jduanen/Acoustic-Camera/RASPBERRY_PI.md

# Running `acoustic_camera_p3.py` on a Raspberry Pi 5

Guide for running the existing Phase 3 live script (`src/acoustic_camera_p3.py`, 16-ch
UMA-16 v2 → 2D beamform → webcam overlay) directly on a Raspberry Pi 5, today, with the
mic array hardware that already exists. This is distinct from the Phase 4 plan
([PHASE4.md](./PHASE4.md)), which uses a Pi 5 as the compute host for a *future* 96-ch
FPGA-fed array. The steps below get the current 16-ch pipeline running standalone in
the meantime, and most of the setup (OS packages, PortAudio, OpenBLAS) carries over
directly to that later phase.

Assumes Raspberry Pi OS, 64-bit, Pi 5 (4 or 8 GB). Written against Debian Bookworm and
confirmed hands-on on Trixie as well. Package names, PortAudio, and the CSI-camera/
`picamera2` situation are the same on both. One real difference found on Trixie: OpenBLAS
is **not** installed by default (see §2). Do that check/install regardless of which OS
version you're on.

**Desktop vs. Lite**: §5 (Display) assumes the Desktop image, which auto-starts a GUI
session (X11 or Wayland). On **Raspberry Pi OS Lite**, there is no display server
running at all -- see the Lite-specific fix in §5.

## 1. System Packages

```bash
sudo apt update
sudo apt install -y libportaudio2 portaudio19-dev python3-opencv v4l-utils
```

- `libportaudio2` / `portaudio19-dev`: `sounddevice` is a thin wrapper over PortAudio;
  without the shared lib it fails to import.
- `python3-opencv`: Raspberry Pi OS's apt build of OpenCV includes GTK GUI support, so
  `cv2.imshow` works out of the box. **Prefer this over `pip install opencv-python`**:
  the PyPI wheel is frequently built headless on ARM and silently breaks `cv2.imshow`
  with a "not implemented" backend error at runtime, not at import time.
- `v4l-utils`: gives you `v4l2-ctl --list-devices` to confirm a USB webcam enumerates
  before wiring it into the script.

## 2. Python Environment

Reuse the project's existing `requirements.txt`. No Pi-specific fork needed, but skip
the packages the live script doesn't import (`acoular`, `pyroomacoustics`, `acoupipe`
are Phase 1 simulation-only):

```bash
python3 -m venv --system-site-packages venv
source venv/bin/activate
pip install numpy scipy sounddevice
```

`--system-site-packages` matters here: it lets the venv see the apt-installed
`cv2` (with GUI support) instead of pulling in a headless wheel from PyPI.

**Confirmed on Raspberry Pi OS Trixie: OpenBLAS is not installed by default.** A stock
Trixie image only has `libblas3`/`liblapack3` (Netlib reference implementations; no
NEON vectorization, single-threaded). `numpy.show_config()` on an unmodified Trixie
install shows generic `name: blas` / `name: lapack` with `openblas configuration:
unknown`, which is the tell that it's riding on the reference implementation rather
than OpenBLAS. This makes MVDR/MUSIC (`scipy.linalg.inv`, `numpy.linalg.eigh`) far
slower than the estimates in §6, so install it explicitly:

```bash
sudo apt install libopenblas0-pthread
```

Debian's `update-alternatives` gives the OpenBLAS build a higher priority (100) than
the reference implementation (10), so this switches automatically. Confirm this with:

```bash
update-alternatives --display libblas.so.3-aarch64-linux-gnu
update-alternatives --display liblapack.so.3-aarch64-linux-gnu
```

Both should report "link currently points to" a path containing `openblas-pthread`.
If not, force it with `sudo update-alternatives --config libblas.so.3-aarch64-linux-gnu`
(and the `liblapack` equivalent) and pick the OpenBLAS entry.

Then confirm from Python:

```bash
python3 -c "import numpy; numpy.show_config()"
```

Note that even with OpenBLAS correctly selected via `update-alternatives`,
`numpy.show_config()` may still print the generic `blas`/`lapack` name with
`openblas configuration: unknown` rather than an explicit `openblas` entry. NumPy's
build-time pkgconfig detection doesn't see through Debian's alternatives indirection.
The `update-alternatives --display` output above is the reliable way to confirm which
implementation is actually linked, not `show_config()`'s `name` field.

This was not something the Bookworm-era assumption in this guide accounted for
(Bookworm's `python3-numpy` was believed to pull in OpenBLAS directly). Treat "is
OpenBLAS actually selected" as a required check on any fresh Pi OS install, not a
formality.

## 3. UMA-16 v2 Hookup

This is dentical to the desktop case -- the UMA-16 is a driverless UAC2 USB device, no Pi-specific
driver needed. Verify it enumerates the same way as in
[nb16](./notebooks/16_uma16_capture.ipynb):

```bash
lsusb | grep -i minidsp        # miniDSP UMA16v2
arecord -l                     # card N: UMA16v2, device 0
python3 -c "import sounddevice as sd; print([d for d in sd.query_devices() if 'uma' in d['name'].lower()])"
```

`find_device()` in `acoustic_camera_p3.py` matches on `'uma' in name`, same as the
notebooks, so no `--device` override should be needed. USB bandwidth for 16 channels ×
24-bit × 48 kHz is trivial for any Pi 5 USB port (no hub/bandwidth concerns).

## 4. Camera

### USB Webcam

The script uses `cv2.VideoCapture(args.video)` (i.e. a V4L2 device index), this only
works with a **USB webcam**, not the Pi Camera Module (CSI). Bookworm removed the
legacy camera stack; the CSI camera is exposed through `libcamera`/`picamera2`, which
`cv2.VideoCapture` cannot open directly. If you only have a Camera Module on hand:

- Easiest: plug in a USB webcam instead; zero code changes.
- Camera Module: use the `--csi` flag — see below. Same direction
  [PHASE4.md](./PHASE4.md#why-pi-5-not-pi-4-or-cm4) already planned for the future 96-ch
  host, implemented here first instead of doing this work twice.

Use `v4l2-ctl --list-devices` to find the right `--video` index. It will very likely
**not** be 0 on a Pi with both a USB webcam and other V4L2-capable hardware present.

### MIPI-CSI Camera

Install 22-pin ribbon cable on one of the connectors near RJ45 connector (contacts facing towards the RJ45).
Earlier Raspberry Pis used 15-pin ribbon cables, can use adaptors to make some of these cameras work with Raspberry Pi 5 boards.
Use camera with M12 lens mount so I can select a lens with the desired FOV.

**Lens choice: 100° FOV.** Two reasons this beats both narrower and wider options on hand
(80/100/120/140/160/200°):

- **Matches the beamforming display window.** The overlay/crosshair math
  (`px = (az_peak + az_fov/2) / az_fov * w`) is a *linear* angle-to-pixel mapping, so the
  camera's real FOV needs to match `--az_fov`/`--el_fov` for the overlay to land on the
  correct pixel. **Confirmed**: switched to this lens, and the code defaults are now
  `az_fov=100°` (matches the lens spec directly) and `el_fov=42°` (scaled from `az_fov`
  by the frame's pixel aspect ratio, `542/1280`, rather than assuming a vertical-FOV
  spec — consistent with the code's own linear-degrees-per-pixel convention, but still
  an approximation pending an empirical check: point the camera at two reference points
  a known angle apart and confirm the crosshair lands where expected).
- **Avoids fisheye distortion.** Lenses above ~100-120° horizontal FOV are essentially
  always fisheye/equidistant-projection, not rectilinear — the linear pixel mapping above
  would be systematically wrong (worse toward the frame edges) without adding a lens
  calibration + `cv2.remap()` undistortion step, which isn't implemented. 100° is the
  widest of the available lenses still likely to be genuinely rectilinear; 80° would be
  the more conservative/certain choice at the cost of a narrower view.

If the wider lenses (120°+) end up preferred later for scene coverage, undistortion is
cheap to add if needed: a one-time `cv2.fisheye.initUndistortRectifyMap()` at startup,
then `cv2.remap()` per frame (~5-8ms at 1280x720 on this hardware, extrapolating from
the comparable-cost `cv2.resize` step already measured in §7 — fits easily in the ~19 ms
of slack under the 50 ms/20 fps budget). The lens calibration itself (checkerboard
capture + `cv2.fisheye.calibrate`) is a one-time setup cost, not a runtime one.

Sensor resolution: no reason to exceed the Touch Display 2's own **1280x720** — the
pipeline never uses more pixels than it displays (no zoom/pan on the video), and §7
already shows overlay-render/`cv2.imshow` cost scaling with pixel count. Target the
sensor's 720p output mode rather than its highest native resolution.

**Software**: `cv2.VideoCapture` cannot open a CSI camera directly (see above), so the
script uses `picamera2` as a second, alternate capture path — pass `--csi` to select it
(`--video` is ignored in that case):

```bash
sudo apt install python3-picamera2   # if not already present on the Desktop image
python src/acoustic_camera_p3.py --algo ds --grid_deg 1.0 --csi
```

`picamera2` is an apt package tied to the system `libcamera` stack, not pip-installable
in an isolated venv — same reasoning as `python3-opencv` in §2: the venv needs
`--system-site-packages` to see it.

Implementation note: `picamera2`'s `"RGB888"` format is actually packed as BGR in
memory (a known naming quirk in `libcamera`), which happens to be exactly the byte
order `cv2` expects — so the capture wrapper (`Picam2Capture` in
`acoustic_camera_p3.py`) does **not** call `cv2.cvtColor` on it. **Confirmed correct on
hardware** — colors display correctly with no conversion. If colors ever look swapped
(red/blue reversed) on a different `picamera2` version, that conversion is the first
thing to add back.

**Confirmed on hardware — this was worth doing**: `cam=0.6 ms`, vs. the USB webcam's
40.7 ms (§7). Total per-frame work drops to ~30.8 ms, under the 50 ms budget, so the
adaptive pacing fix (§7) sleeps out the remainder and this hits the full **~20 fps**
target — a large improvement over the USB webcam's ~14 fps. See §7 for the full
before/after comparison.

Default capture size is `1280x542`, not the panel's native `1280x720` — the missing
`178px` (`2*44 + 90`) is reserved for the Fhi slider strip, spectrum plot, and Flo
slider strip stacked below the video (see README.md's Phase 3 "Touch UI" writeup for
why they're laid out that way), so the combined display still exactly fills the
1280x720 panel with no letterboxing.

## 5. Display

`cv2.imshow` needs a real GUI session. The options below assume the **Desktop** image,
which auto-starts a local GUI session (X11, confirmed by what worked below) on the
HDMI-attached monitor at boot.

**Important distinction confirmed on hardware**: "a desktop session is running on the
Pi" is not the same as "your shell can draw to it." A plain SSH login is a separate
session (`XDG_SESSION_TYPE=tty`, no `DISPLAY`/`XAUTHORITY` set) from the auto-started
local desktop session on `seat0`, even though both exist on the same machine at the
same time (check with `loginctl list-sessions`). Three distinct scenarios:

- **Logged in locally** (keyboard/monitor directly on the Pi, or VNC into that same
  session): just works, `DISPLAY` is already set correctly in that session's own
  terminal.
- **SSH with `-X`/`-Y` forwarding**: works, but *not* by drawing on the Pi's monitor:
  it creates a **new**, separate X11 display on the Pi that tunnels every frame back
  over the network to your own machine's X server. The window appears on your laptop,
  not the Pi's HDMI output. Also far too slow for live 15-20 fps video, it is useful only
  for a one-off sanity check.
- **SSH, no `-Y`, attaching to the Pi's own already-running local desktop session**:
  this is what actually renders on the Pi's physical HDMI monitor while running the
  command remotely. **Confirmed working recipe:**

  ```bash
  export DISPLAY=:0
  export XAUTHORITY=/home/pi/.Xauthority   # your actual home dir
  python acoustic_camera_p3.py --video 0 --grid_deg 1.0
  ```

  Both variables are required. `DISPLAY=:0` alone fails with "could not connect to
  display" (Qt still needs the auth cookie to attach to someone else's X session).
  This is a plain X11 session using the standard per-user `~/.Xauthority`, which is simpler
  than initially expected; no Xwayland-specific rootless auth file hunting needed.

Add `--fullscreen` to fill the whole monitor (borderless window) -- see §6.

### Raspberry Pi OS Lite (partial, not fully validated)

Lite has no display server running at all -- no X11, no Wayland compositor. `cv2.imshow`
fails with:

```
qt.qpa.xcb: could not connect to display
qt.qpa.plugin: Could not load the Qt platform plugin "xcb" ...
```

This looks like a GTK-vs-Qt OpenCV backend problem (the plugin list even offers
`wayland`), but it isn't; there is simply no compositor for any backend to attach to.
The lightest fix, in principle, is a bare X server with no window manager, using
`xinit` to launch the script as the sole X client:

```bash
sudo apt install --no-install-recommends xserver-xorg xinit x11-xserver-utils
xinit /path/to/venv/bin/python /path/to/acoustic_camera_p3.py --video 0 --grid_deg 1.0 -- :0
```

**This was not fully validated**: on real hardware this problem occurred `Fatal server error:
Cannot run in framebuffer mode. Please specify busIDs for all framebuffer devices`.
Xorg is falling back to the `fbdev` driver instead of `modesetting`/KMS (the Pi 5 has no
non-KMS mode). The likely fix is forcing the driver explicitly:

```bash
sudo mkdir -p /etc/X11/xorg.conf.d
sudo tee /etc/X11/xorg.conf.d/10-modesetting.conf <<'EOF'
Section "Device"
    Identifier "Pi5"
    Driver "modesetting"
    Option "kmsdev" "/dev/dri/card0"
EndSection
EOF
```

(`modesetting` is built into `xserver-xorg-core`, not a separate package; no install
needed for the driver itself.) This was not re-tested. The Pi was reinstalled with
the Desktop image instead, which avoids the whole class of problem. If you need a
Lite-based headless deployment later (e.g. a lighter Phase 4 field unit), start here
but expect to need this driver fix, and confirm `/dev/dri/card0` is actually the right
device (`ls /dev/dri/`) before assuming it.

### DSI Display

Tested first using HDMI-attached display. Now using the Raspberry Pi Touch Display 2
(https://www.raspberrypi.com/documentation/accessories/touch-display-2.html#raspberry-pi-touch-display-2),
connected via the DSI port. Touch works out of the box as mouse input for the script's
frequency sliders — no config needed there.

The panel's native orientation is portrait; rotate it to landscape at login. Raspberry
Pi OS Desktop on Trixie runs **Wayland (`labwc`)**, with `:0` served via XWayland for X11
compatibility — so this must be done with `wlr-randr` (the Wayland-native output tool),
**not** `xrandr`: `xrandr` talks to XWayland's emulated root window, which can't be
resized/rotated and fails with a RandR `BadMatch` error for this. `wlr-randr` talks to
the compositor directly and works.

First confirm your actual output name (`wlr-randr` with no arguments lists all outputs —
this DSI port enumerated as `DSI-2`, not `DSI-1`, on this hardware; don't assume it
matches without checking), then add the rotation to `labwc`'s autostart script so it
applies on every login, not just the current session:

```bash
wlr-randr                      # confirm the output name first
mkdir -p ~/.config/labwc
echo 'wlr-randr --output DSI-2 --transform 270 &' >> ~/.config/labwc/autostart
chmod +x ~/.config/labwc/autostart
```

`--transform` takes `90`/`180`/`270` (or `flipped-90` etc. for mirrored orientations) —
adjust if the picture comes up rotated the wrong way. Reboot (or log out/in) to confirm
it persists; a manually-run `wlr-randr` command only affects the current session.

#### Touchscreen

Edit `/etc/xdg/libfm/libfm.conf` and change `single_click=0` to `single_click=1`.

### Auto-start on boot

A system-level systemd unit ([systemd/acoustic-camera.service](./systemd/acoustic-camera.service))
launches the script automatically once the Desktop image's auto-login GUI session comes
up, using the same `DISPLAY=:0` / `XAUTHORITY` recipe confirmed above. It's a system
unit rather than a `~/.config/systemd/user/` one so it doesn't depend on whether
labwc's autologin session actually signals `graphical-session.target` for the user's
systemd instance — instead it targets `graphical.target` (reached once any display
manager/session starts) and leans on `Restart=on-failure` + `RestartSec=5` (with the
`[Unit]` start-limit disabled) to self-heal through the boot race if it launches before
the desktop session has actually finished coming up, rather than a bespoke wait-for-X
script. Pressing `q` to quit exits 0, so it won't auto-relaunch after a deliberate quit.

Install:

```bash
sudo cp systemd/acoustic-camera.service /etc/systemd/system/
sudo systemctl daemon-reload
sudo systemctl enable --now acoustic-camera.service
```

The unit hardcodes user `jdn` and path `/home/jdn/Code/Acoustic-Camera` — edit
`User=`, `WorkingDirectory=`, `XAUTHORITY=`, and `ExecStart=` if deploying under a
different account or checkout path. Check status/logs with
`systemctl status acoustic-camera.service` / `journalctl -u acoustic-camera.service -f`.

### Home Screen Icons for System Control

Once the `Exit` button is pushed on the Acoustic Camera application's popup window, the application will exit and the Raspberry Pi Trixie desktop will be shown.
In addition to the standard desktop taskbar, there are several icons on the Desktop that can be used to quickly control the application and system.

#### Acoustic Camera



Touching this icon starts the Acoustic Camera application (which takes over the full screen).

The Acoustic Camera icon's action is defined in `./Desktop/acousticcamera.desktop`.

#### Reboot

Reboot Icon

Touching this icon causes the Raspberry Pi to reboot and relaunch the Acoustic Camera application.

The system reboot icon's action is defined in `./Desktop/reboot.desktop`.

#### System Shutdown

Shutdown Icon

Touching this icon will cause the system to shutdown.

The system shutdown icon's action is defined in `./Desktop/shutdown.desktop`.

#### Battery

Battery Icon

Shows the current UPS charge as a percentage, baked into the icon graphic itself (green ≥50%, amber ≥20%, red below). The icon is regenerated from the INA219 fuel-gauge chip (same reading as the live overlay's own battery indicator, see `src/acoustic_camera_p3.py`) by `bin/battery_icon.py`, which writes `assets/battery_icon.png`. Touching the icon re-runs that script for an immediate refresh; otherwise it's kept current automatically by `battery-icon.timer` (every 60s).

The battery icon's action is defined in `./Desktop/battery.desktop`. Install the timer:

```bash
sudo cp etc/systemd/system/battery-icon.service etc/systemd/system/battery-icon.timer /etc/systemd/system/
sudo systemctl daemon-reload
sudo systemctl enable --now battery-icon.timer
```

Note: whether the desktop actually redraws an already-displayed icon when its target PNG changes on disk depends on the desktop shell's icon-cache behavior — `bin/battery_icon.py` also touches `Desktop/battery.desktop`'s mtime after each render as a best-effort nudge, but this hasn't been fully validated against Trixie's desktop (pcmanfm/labwc). If it doesn't auto-refresh in practice, tapping the icon (or `F5`) forces a redraw.

#### Calibrate

Calibrate Icon

Runs `src/calibrate_uma16.py`, a terminal walkthrough of the same boresight-reference procedure as [`notebooks/17_uma16_calibration.ipynb`](notebooks/17_uma16_calibration.ipynb) (frequency-domain cross-correlation for per-mic delay, RMS ratios for per-mic gain), so the array can be re-calibrated directly on the appliance without a dev machine or Jupyter. It records a 5s boresight clip on prompt, prints the measured delay/gain per channel, backs up any existing `test/UMA16/cal.npy` to `cal.npy.bak`, saves the new calibration vector, and reports the boresight DoA peak (D&S and MVDR) before vs after as a sanity check.

Touching the icon opens `lxterminal` running `bin/calibrate.sh`, so the prompts and results are visible; the window stays open until you press Enter at the final prompt. The calibrate icon's action is defined in `./Desktop/calibrate.desktop` — it assumes `lxterminal` is the installed terminal emulator (Raspberry Pi OS's default); swap the `Exec=` command if a different one is in use.

**Tone frequency**: the script prompts for a **1 kHz** tone (`CAL_FREQ` in `src/calibrate_uma16.py`), matching both source notebooks. 1 kHz is:
- well below the array's ~4082 Hz spatial Nyquist (`NYQUIST` in `src/beamforming.py`, set by the 42mm mic spacing), so there's no spatial-aliasing ambiguity in the phase measurement;
- easily reproduced cleanly by a phone or laptop speaker (most roll off below 1 kHz or beam/distort above it);
- short enough a wavelength (~343mm) relative to typical mic-to-mic delays that the delay-to-phase conversion (`2π·f·delay`) stays well within ±π, avoiding phase-wrap ambiguity.

Any phone tone-generator app works, or from a laptop with `sox` installed:
```bash
play -n synth 5 sine 1000
```

**Device selection**: like `acoustic_camera_p3.py`, the script auto-detects the UMA-16 via
`find_device()` (first device whose name contains "uma" with ≥16 input channels), or you can
pin it explicitly with `--device IDX`. Do this if the main app needs `--device` to find the
right entry too (some ALSA setups enumerate the same physical device more than once, e.g. a
raw `hw:X` PCM alongside a `plughw`/`dsnoop`-wrapped one). Run
`python -c "import sounddevice as sd; print(sd.query_devices())"` to see all candidates and
their indices.

**Recording method**: the script captures via `sd.InputStream(..., blocksize=256, callback=...)`
— the exact same method `acoustic_camera_p3.py` uses — rather than the simpler
`sd.rec()`/`sd.wait()` convenience call, which lets PortAudio pick its own default
blocksize/latency. This wasn't confirmed to be the actual cause of any specific failure, but
matching the main app's proven-working capture method removes one source of behavioral
difference between the two scripts.

**Validity check is SNR-based, not amplitude-based**: `calibrate_uma16.py` checks that
`CAL_FREQ` is at least `_MIN_SNR_DB` (20 dB) above the noise floor, not that the recording
is loud in absolute terms. This matters because a real, usable tone can be very quiet in
absolute amplitude — well under 1% of full scale — if the source is distant or this
particular UMA-16 unit's capture chain runs at low gain, while still being extremely clean
relative to the noise floor (a real observed case: ~46 dB SNR at ~0.1% of full scale). An
earlier version of this check used absolute peak amplitude instead and incorrectly rejected
recordings like that one. If you ever want to check a recording's SNR by hand:
```bash
python3 -c "
import numpy as np, scipy.io.wavfile as wavfile
fs, ref = wavfile.read('test/UMA16/cal_ref.wav')
seg = ref[:8192, 0].astype(np.float32) * np.hanning(8192)
F = np.abs(np.fft.rfft(seg))**2
freqs = np.fft.rfftfreq(8192, 1/fs)
pk = np.argmin(np.abs(freqs - 1000))
print('SNR (dB):', 10*np.log10(F[pk-3:pk+4].mean() / np.median(F)))
"
```

**If the tone isn't actually audible to the array** — too quiet, too far, not playing, or
the wrong input device — the reference recording is just mic/ADC self-noise, and the
resulting delay/gain estimates are meaningless (typically visible as several channels
locking onto suspiciously identical exact-integer-sample delays, since noise has no real
cross-channel phase relationship). `calibrate_uma16.py` checks for this: if the loudest
sample in the recording is below 2% of full scale, it aborts with an explanation instead of
saving a bogus calibration — the existing `cal.npy` is left untouched. Watch the per-channel
RMS bar chart the script prints right after recording; a real tone shows clearly elevated
bars, not near-empty ones.

## 6. Performance Expectations

The Pi 5's Cortex-A76 @ 2.4 GHz with OpenBLAS runs dense BLAS roughly 3-4× slower than a
modern desktop CPU (measured basis for this estimate: [PHASE4.md](./PHASE4.md) scaling
analysis for the 96-ch Phase 4 host). Scaling the existing 16-ch desktop benchmarks from
[PHASE3.md](./PHASE3.md)'s `benchmark_algos.py` results:

| Grid | D&S (desktop measured) | D&S (Pi 5, est.) | MVDR/MUSIC (Pi 5, est.) | CLEAN-SC 20 iter (Pi 5, est.) |
|---|---|---|---|---|
| 0.5°/pt (181×121 = 21,901 pts) | ~21 ms | ~70-85 ms | ~75-90 ms | ~300-350 ms |
| 1.0°/pt (91×61 = 5,551 pts) | ~7 ms  | ~20-25 ms | ~20-25 ms | ~55-65 ms |

At 1.0°/pt, D&S/MVDR/MUSIC should sustain roughly 15-20 fps on the Pi 5 *purely on compute
cost*. At the default 0.5°/pt, D&S is likely still fine but MVDR/MUSIC and especially
CLEAN-SC will visibly lag. **These estimates only cover the CSM+beamform math** — see §7
for what the live script actually costs end-to-end, which is substantially more than this
table alone would suggest.

**Recommended starting command**: coarser grid, cheapest algorithm, confirm it runs
before turning up resolution or trying MVDR/MUSIC/CLEAN-SC:

```bash
python src/acoustic_camera_p3.py --algo ds --grid_deg 1.0
```

For a fixed HDMI-monitor "camera appliance" deployment, add `--fullscreen` to fill the
whole screen with a borderless window (see §5 for how to get the display attached in
the first place):

```bash
python src/acoustic_camera_p3.py --algo ds --grid_deg 1.0 --fullscreen
```

If you want real numbers instead of estimates before wiring up the camera/display,
run the existing benchmark script directly on the Pi first. It needs no camera, no
display, and no live mic input (it loads `test/UMA16/capture_nb16.wav`):

```bash
python src/benchmark_algos.py --grid_deg 1.0
```

That gives per-algorithm mean time and RT% on the actual Pi 5 hardware, which is more
trustworthy than the estimates in the table above.

## 7. Performance Measurements

The §6 estimates come from the offline `benchmark_algos.py` script, which only measures
CSM + beamform math. The live script (`acoustic_camera_p3.py`) also does camera capture,
overlay rendering, and `cv2.imshow`, none of which appear in that benchmark — and on real
hardware, those turned out to matter more than the compute estimates did. The script has a
`--profile` flag that prints a per-stage timing breakdown to stderr every 20 frames:

```bash
python src/acoustic_camera_p3.py --algo ds --grid_deg 1.0 --video 0 --profile
```

**Confirmed on hardware** (Pi 5, D&S, 1.0°/pt, real UMA-16):

| Stage | USB webcam (`--video 0`) | No camera (`--video 99`) | MIPI-CSI (`--csi`) |
|---|---|---|---|
| camera capture | 40.7 ms | 0.1 ms | **0.6 ms** |
| audio buffer → array | 6.2 ms | 6.0 ms | 6.5 ms |
| CSM + D&S | 13.1 ms | 12.6 ms | 13.2 ms |
| overlay render | 6.3 ms | 5.7 ms | 6.2 ms |
| `cv2.imshow` + `waitKey` | 4.0 ms | 3.9 ms | 4.3 ms |
| **compute total** | **70.3 ms** | **28.2 ms** | **30.8 ms** |

`--fullscreen` made no measurable difference to any of these — the source frame `cv2.imshow`
receives is the same size either way; only the window-manager-side scale-to-screen changes,
which isn't where the cost is.

- USB webcam: 70.3 ms of work already exceeds the 50 ms budget → sleep contributes ~0 →
  **~14 fps** (up from the original ~8 fps), limited purely by camera capture cost
- No camera: 28.2 ms of work + ~21.8 ms sleep ≈ 50 ms/frame → **~20 fps** (hits the intended target after fixing the loop delay bug)
- MIPI-CSI: 30.8 ms of work + ~19.2 ms sleep ≈ 50 ms/frame → **~20 fps** — matches the
  no-camera ceiling, i.e. the CSI camera is effectively free compared to the beamforming
  compute cost. This is the best available camera configuration on this hardware.

### Camera Backend: default auto-selection was already the best option

`cam.read()`'s ~40 ms floor was tried two ways to reduce, both regressions on this hardware:

| Backend | `cam.read()` |
|---|---|
| Default (`cv2.VideoCapture(idx)`, auto-selects GStreamer) | **40.7 ms** |
| Forced `cv2.CAP_V4L2`, no format hint | 65.2 ms |
| Forced `cv2.CAP_V4L2` + explicit `cv2.VideoWriter_fourcc(*'MJPG')` | 64.0 ms |

Likely explanation: GStreamer's auto-negotiated pipeline was probably already requesting a
compressed (MJPEG) format from the webcam, while raw V4L2 without an explicit format request
defaulted to something uncompressed (e.g. YUYV) — roughly double the bytes over USB plus more
software color-conversion work. **Reverted to the plain default** (`cv2.VideoCapture(args.video)`,
no explicit backend/format) — confirmed the fastest of the three on this specific webcam/Pi
combination. This is device-specific; a different USB webcam could behave differently.

### Confirmed: MIPI-CSI camera via `picamera2` solves the camera bottleneck

Implemented (`--csi` flag, see §4) and confirmed on hardware — numbers above. A
CSI-attached Camera Module bypasses USB and GStreamer entirely, talking to the Pi's
ISP/DMA pipeline directly via `picamera2` rather than `cv2.VideoCapture` (which cannot
open a CSI camera at all). Same direction
[PHASE4.md](./PHASE4.md#camera-pi-camera-module-3-wide) already planned for the 96-ch
host — implemented here first instead of doing the work twice. Colors confirmed correct
with no `cv2.cvtColor` needed (see §4's `RGB888`/BGR note).

## 8. System Hardware

When running the `acoustic_camera_p3.py` program, the system consumes up to around 1.75A @ 5V.
This means that not only do I have to power this with a (ideally battery) source that can provide in excess of 2A at 5.V (actually 5.1V), but I also have to have cabling that can support this current load without imposing a significant resistive loss.

Furthermore, even with a large heatsink with a fan, the CPU temperature gets up to ~60C (with ~25C ambient).

### Power Supply

The system is powered by three 18650 Li batteries in a series configuration and managed by a Waveshare UPS 3S module (see https://www.waveshare.com/ups-module-3s.htm).

The Battery Management System (BMS) provides balanced charging, reverse warning, and battery protection for the Li batteries, as well as voltage and current monitoring, 3.3V and 5V regulation, and an I2C bus interface to the Raspberry Pi.

The Raspberry Pi's I2C interface must first be enabled by running `raspi-config` and selecting `Options -> I2C -> Yes`.

A Waveshare-provided program that prints the current voltage, current, power, and remaining battery percentage is found in https://files.waveshare.com/upload/e/ea/UPS_Module_3S_Code.zip.

`acoustic_camera_p3.py` reads the same INA219 chip directly (via `ups/UPS_Module_3S_V2/INA219.py`, I2C address `0x41`) and draws a battery icon + percentage next to the settings tab in the top-right corner of the live display. It needs apt's `python3-smbus` (see requirements.txt); without it, or without a UPS attached, the indicator is simply not drawn.

N.B. It is important to source the Li batteries from a well-known reliable source as they are very energetic and could cause a problem if they were to malfunction.

## 9. Known Issues Summary

| Symptom | Cause | Fix |
|---|---|---|
| `sounddevice` import error | missing `libportaudio2` | `apt install libportaudio2` |
| `cv2.imshow` errors "not implemented" | headless OpenCV wheel from `pip` | use apt `python3-opencv`, venv with `--system-site-packages` |
| Camera won't open / wrong device | Pi Camera Module (CSI), not a USB webcam | use a USB webcam, or pass `--csi` for `picamera2` (see §4/§7) |
| `cv2.imshow` hangs / X errors over SSH | no display session, or SSH session not attached to the Pi's local desktop session | log in locally/VNC, or export `DISPLAY=:0` + `XAUTHORITY=~/.Xauthority` (see §5) |
| `ssh -Y` window appears on your own machine, not the Pi's monitor | `-Y` tunnels a **new** X display back to your client; it never touches the Pi's HDMI output | use the `DISPLAY`/`XAUTHORITY` attach recipe in §5 instead of `-Y` |
| Low fps at default settings | 0.5°/pt grid + MVDR/MUSIC/CLEAN-SC too heavy for Pi 5 | `--grid_deg 1.0`, start with `--algo ds` |
| Live fps much lower than §6 compute estimates suggest | camera capture (~40 ms) + a frame-pacing bug (fixed sleep added *on top of* work, not a target) both add cost the offline benchmark never measured | see §7; pacing bug is fixed in current code, camera cost is a hardware floor with this webcam |
| MVDR/MUSIC far slower than §6 estimates | OpenBLAS not installed (confirmed default on Trixie); NumPy silently falls back to reference BLAS/LAPACK | `apt install libopenblas0-pthread`, verify with `update-alternatives --display libblas.so.3-aarch64-linux-gnu` |
| Xorg: `Cannot run in framebuffer mode...` (Lite only) | falling back to `fbdev` instead of `modesetting`/KMS | force `modesetting` via `/etc/X11/xorg.conf.d` (see §5, not fully validated) |
| Touch sliders felt laggy / seemed to cross despite clamping | stale read used for display, not the clamp math | see README.md's Phase 3 "Touch UI" section |
| `calibrate_uma16.py` aborts with "X Hz is only Y dB above the noise floor" | genuinely no usable tone in the recording — not just quiet, but no clean peak at `CAL_FREQ` at all | confirm the tone is really playing (not timed out/stopped), check device selection, re-run — see §8 Calibrate |
| RMS bars all look tiny / peak amplitude is well under 1% of full scale | not necessarily a problem — check the printed SNR line instead of judging by eye. A real tone can be very quiet in absolute terms yet still pass easily (observed: ~46 dB SNR at ~0.1% of full scale) | see §8 Calibrate's "Validity check is SNR-based" note; if SNR is also low, then it's a real issue (see row above) |
