jduanen/Acoustic-Camera/assets/arm_board.png

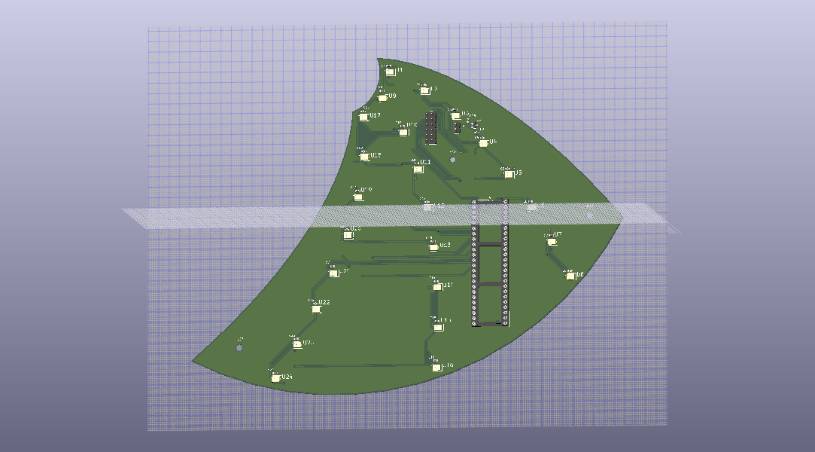
assets/arm_board.png
