jduanen/Acoustic-Camera/assets/hub.png

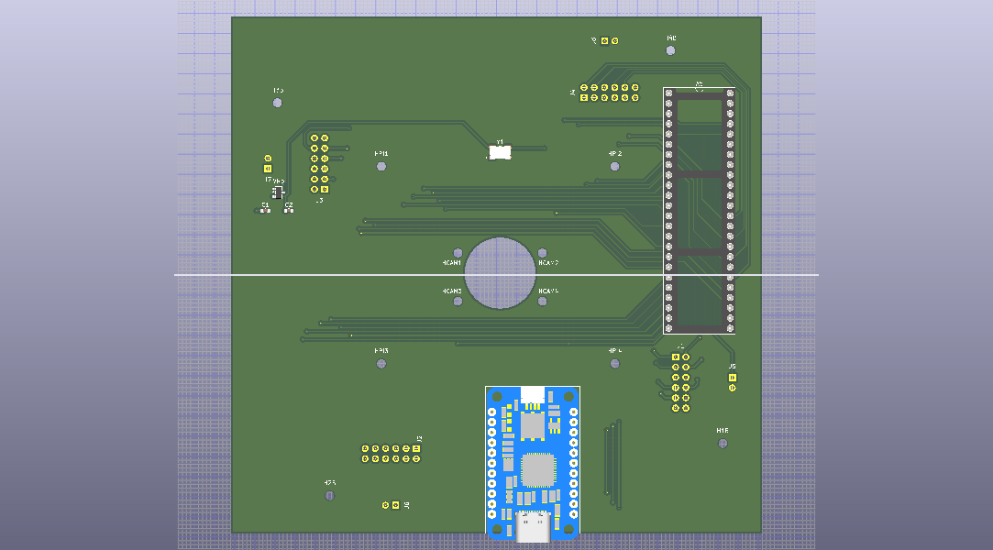
assets/hub.png
