jduanen/Acoustic-Camera/assets/Phase3InsideTop.jpg

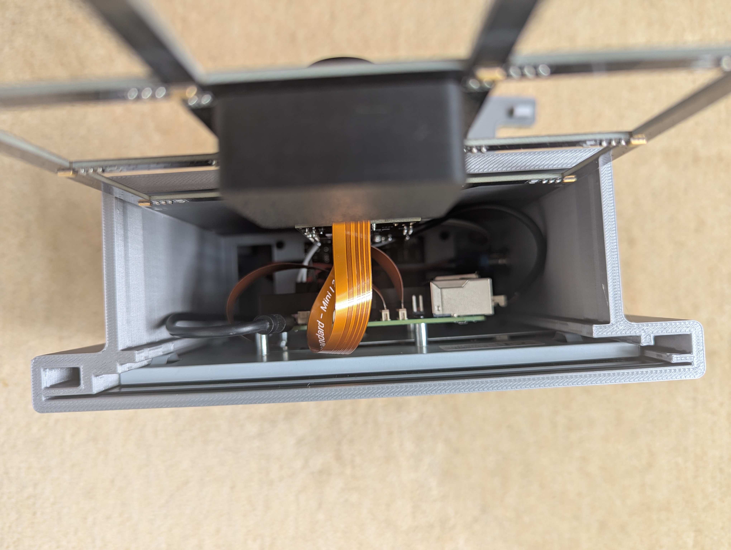
assets/Phase3InsideTop.jpg
