jduanen/Acoustic-Camera/images/phase4_array_configs.png

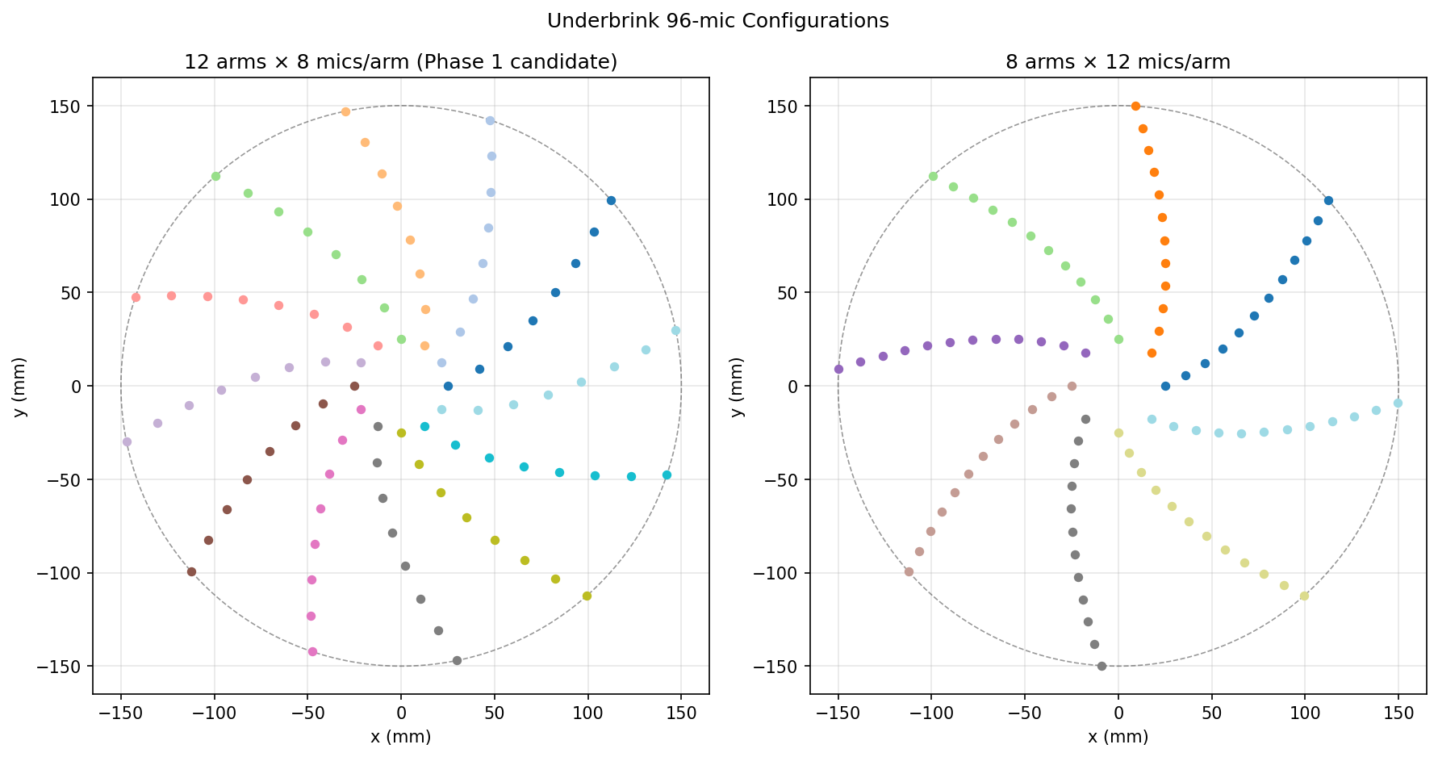
images/phase4_array_configs.png
