jduanen/Acoustic-Camera/images/phase4_array_layout.png

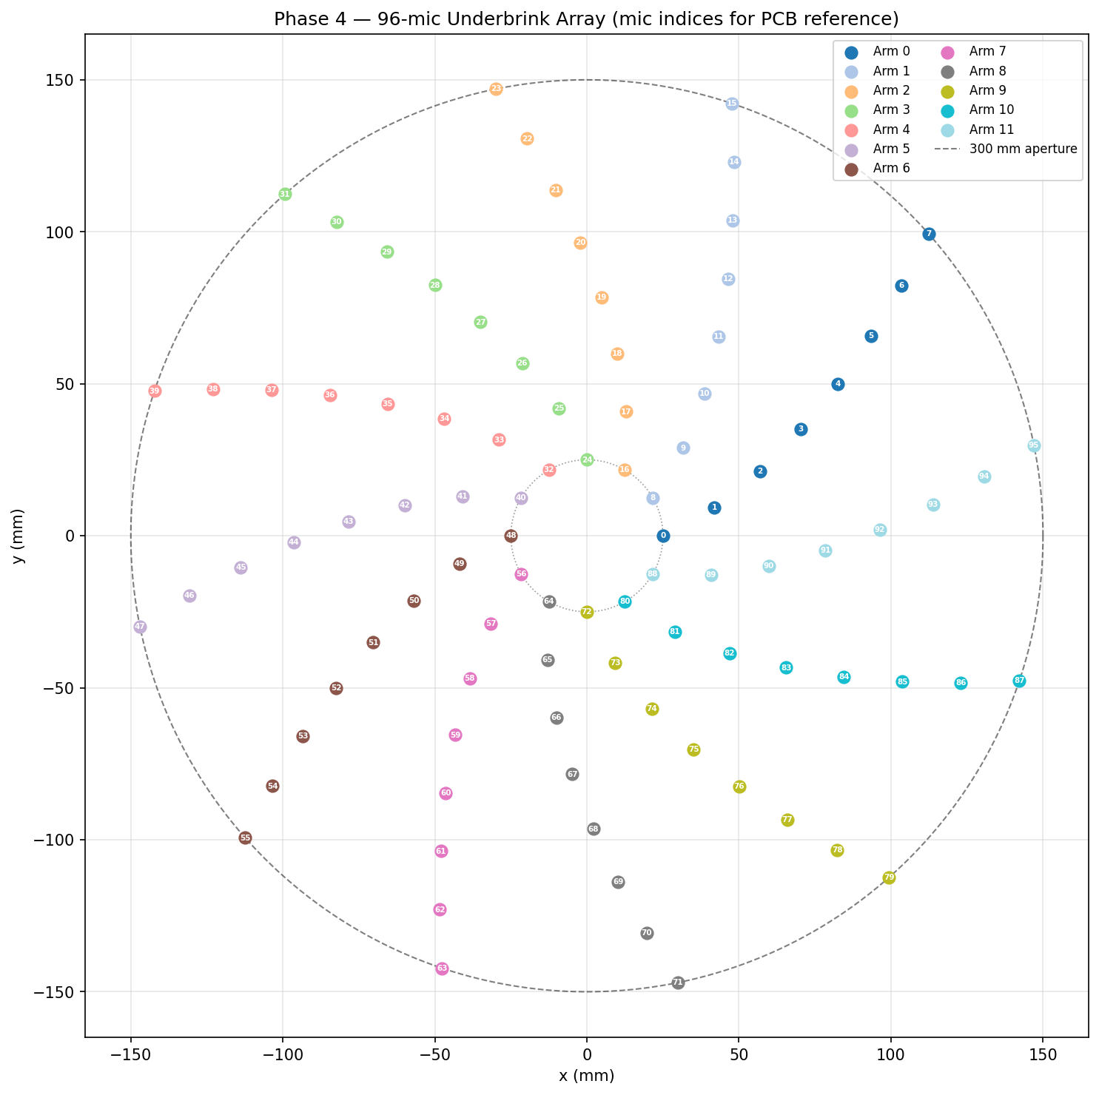
images/phase4_array_layout.png
