jduanen/Acoustic-Camera/images/phase4_hpbw.png

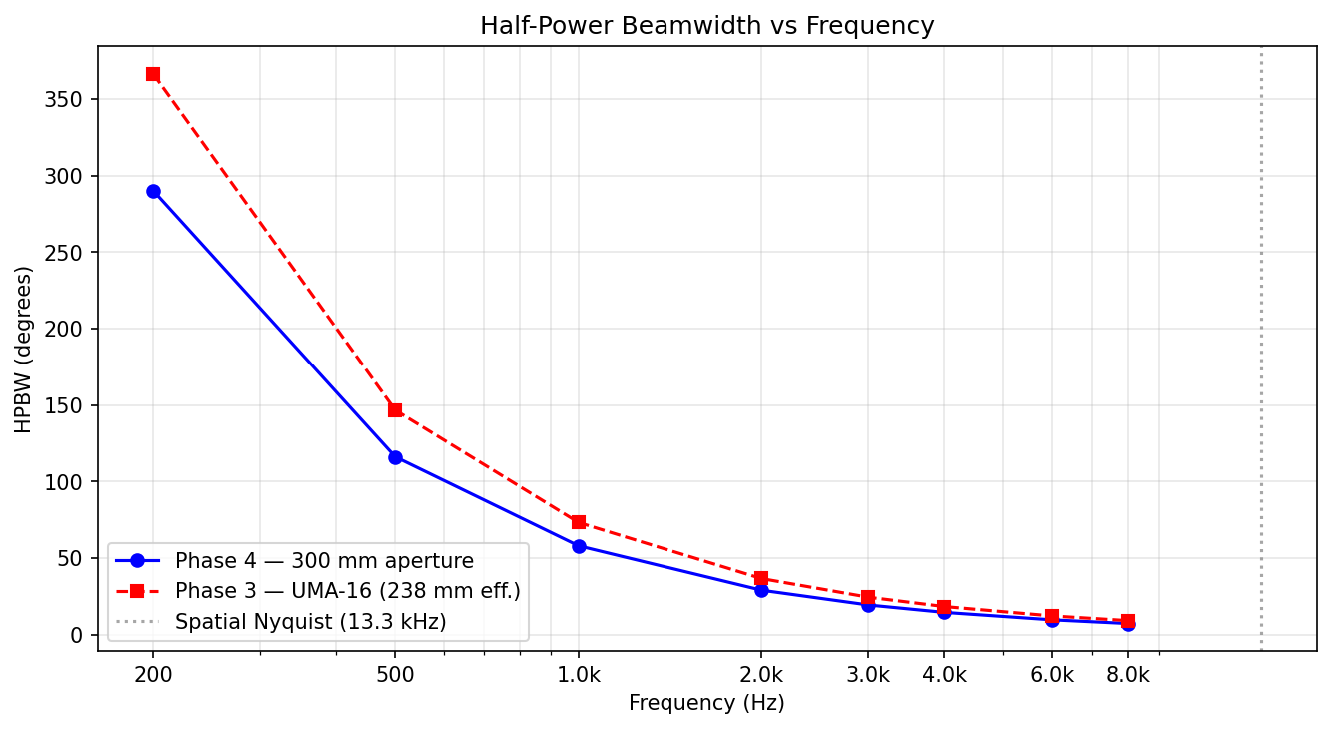
images/phase4_hpbw.png
