jduanen/Acoustic-Camera/images/phase4_nn_hist.png

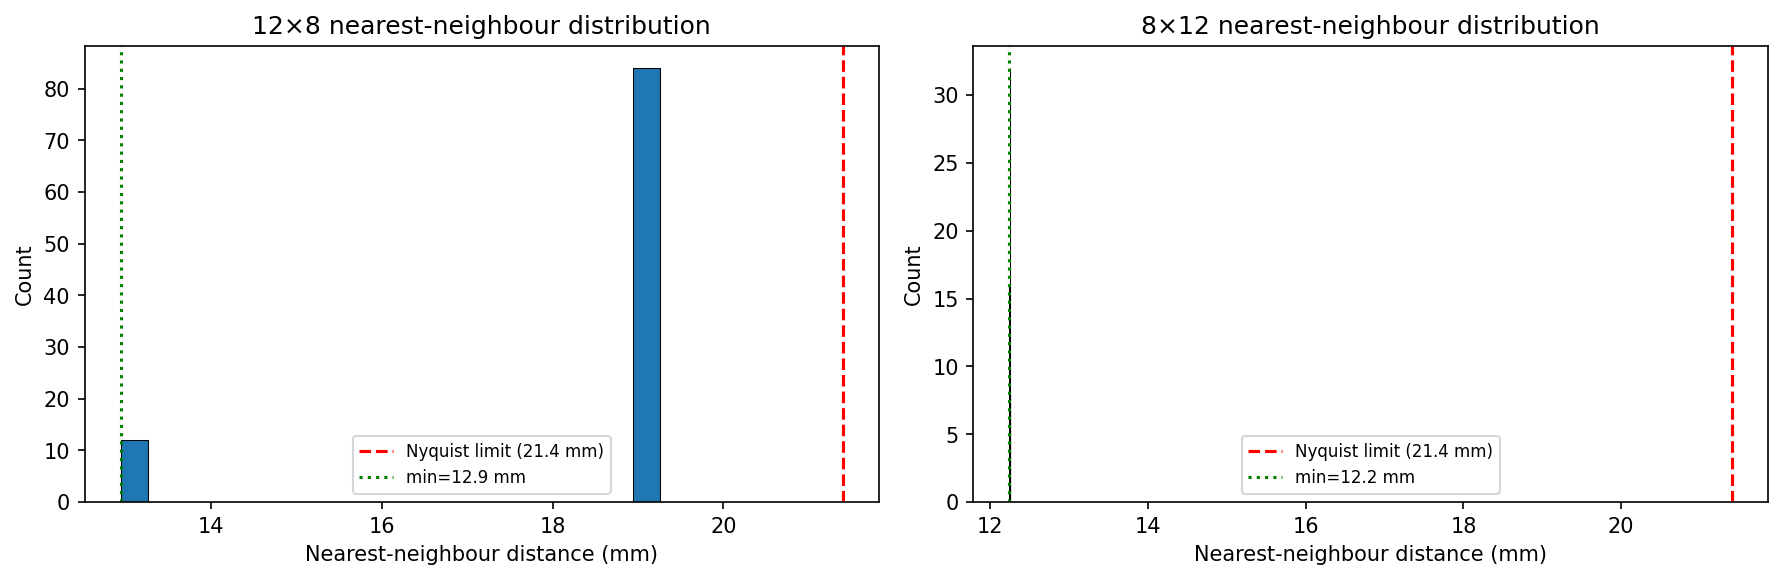
images/phase4_nn_hist.png
