jduanen/Acoustic-Camera/notebooks/2d_algo_comparison.png

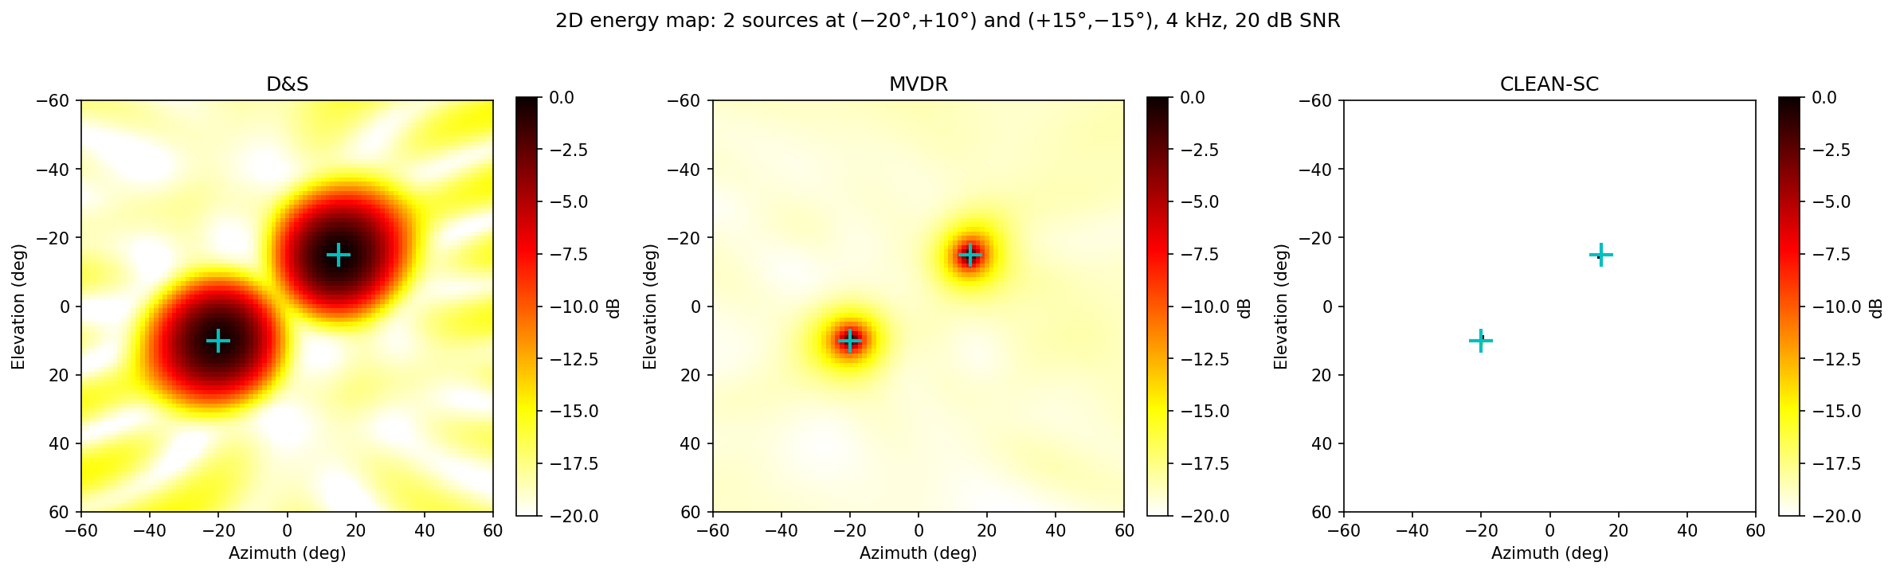
notebooks/2d_algo_comparison.png
