jduanen/Acoustic-Camera/notebooks/2d_psf_freq.png

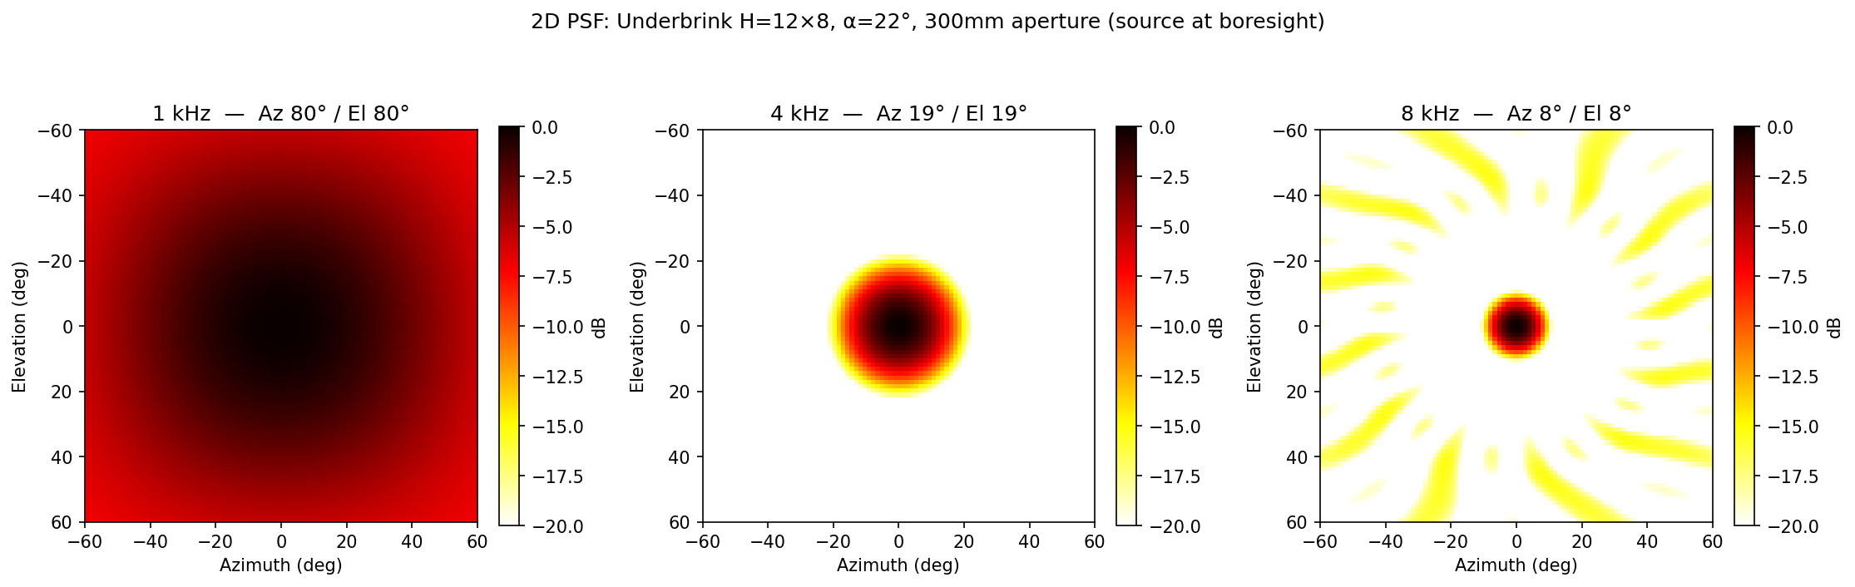
notebooks/2d_psf_freq.png
