jduanen/Acoustic-Camera/notebooks/algo_single_source.png

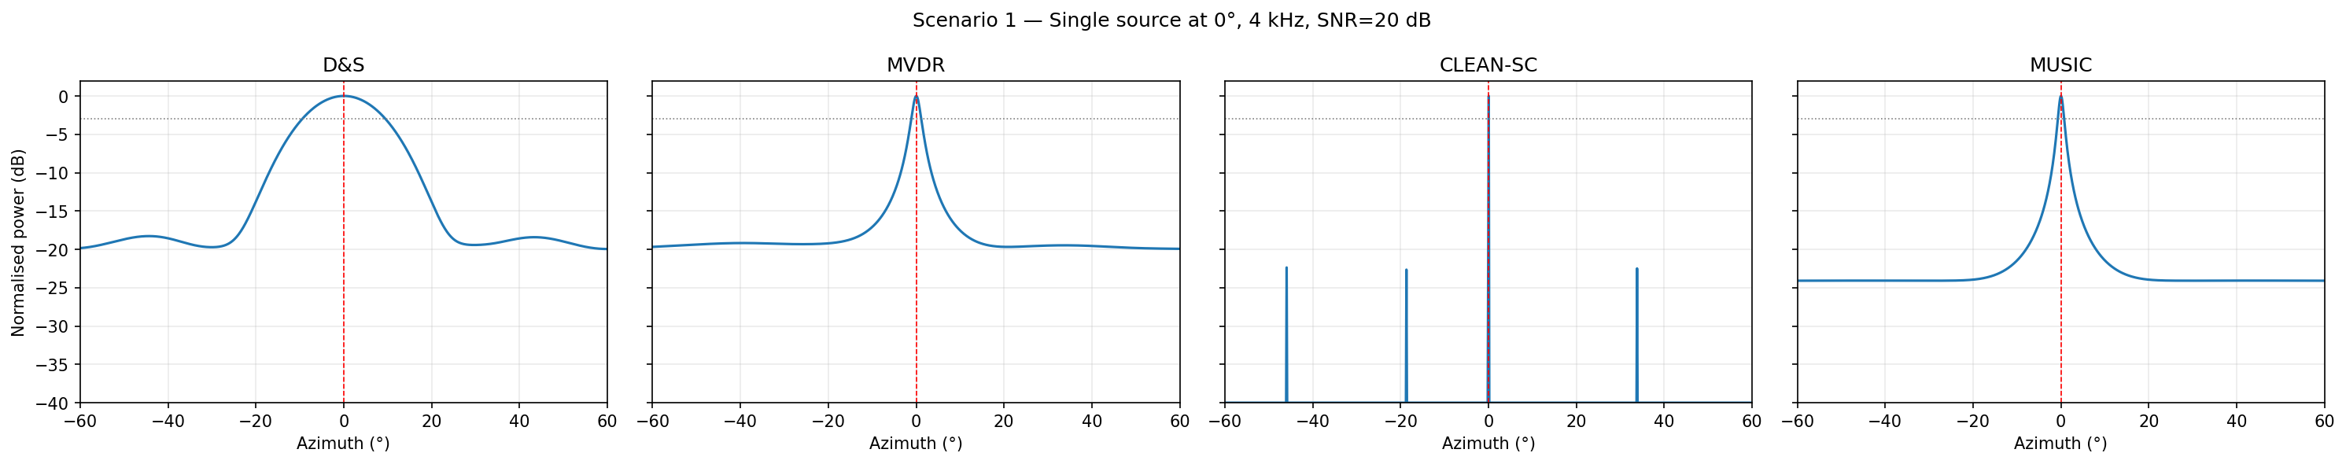
notebooks/algo_single_source.png
