jduanen/Acoustic-Camera/notebooks/algo_snr_sweep.png

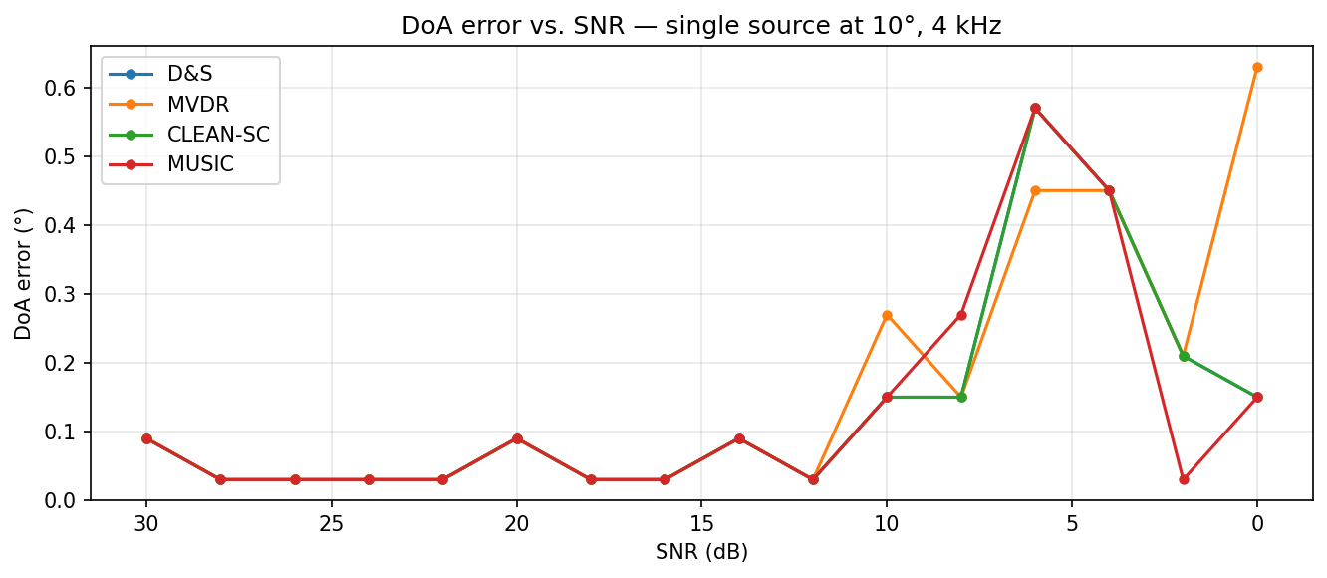
notebooks/algo_snr_sweep.png
