jduanen/Acoustic-Camera/notebooks/algo_two_sources_30deg.png

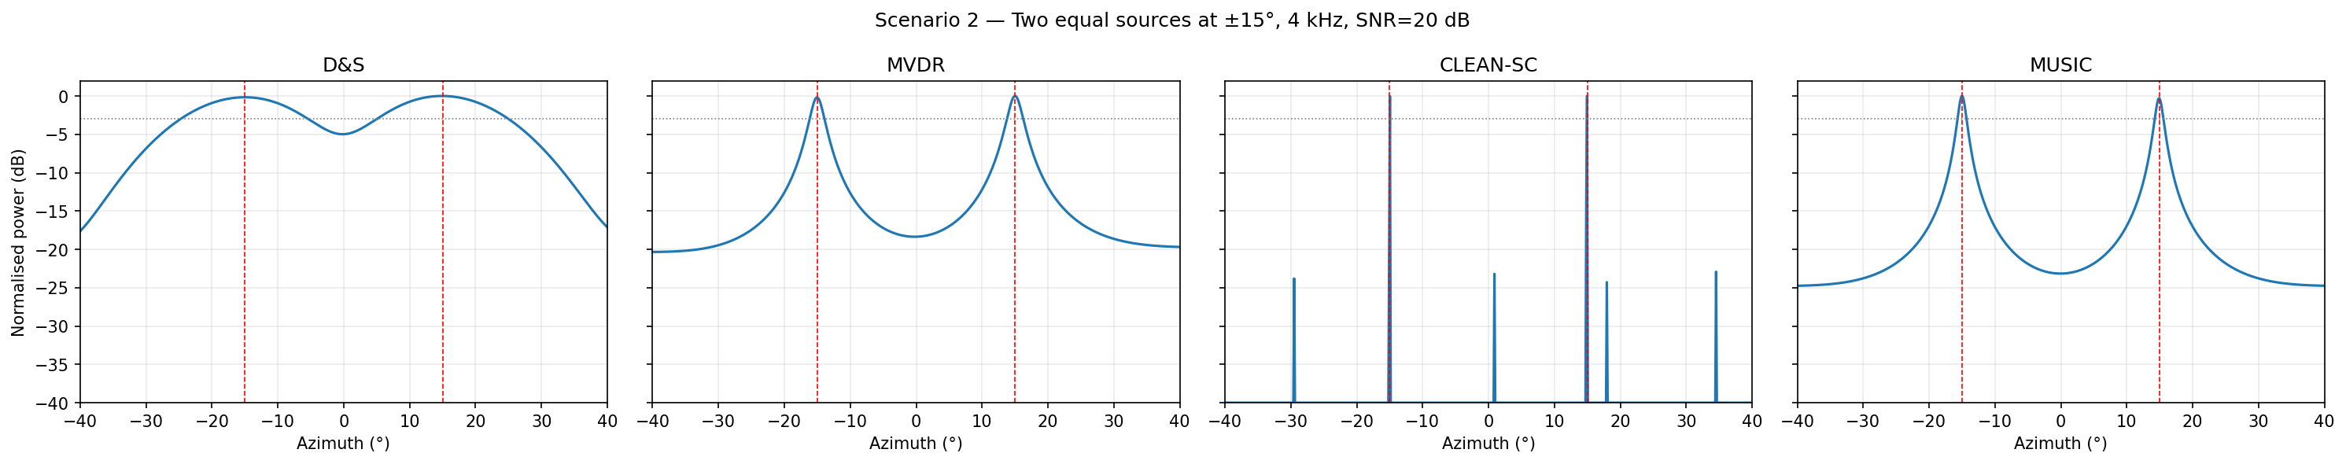
notebooks/algo_two_sources_30deg.png
