jduanen/Acoustic-Camera/notebooks/algo_two_sources_close.png

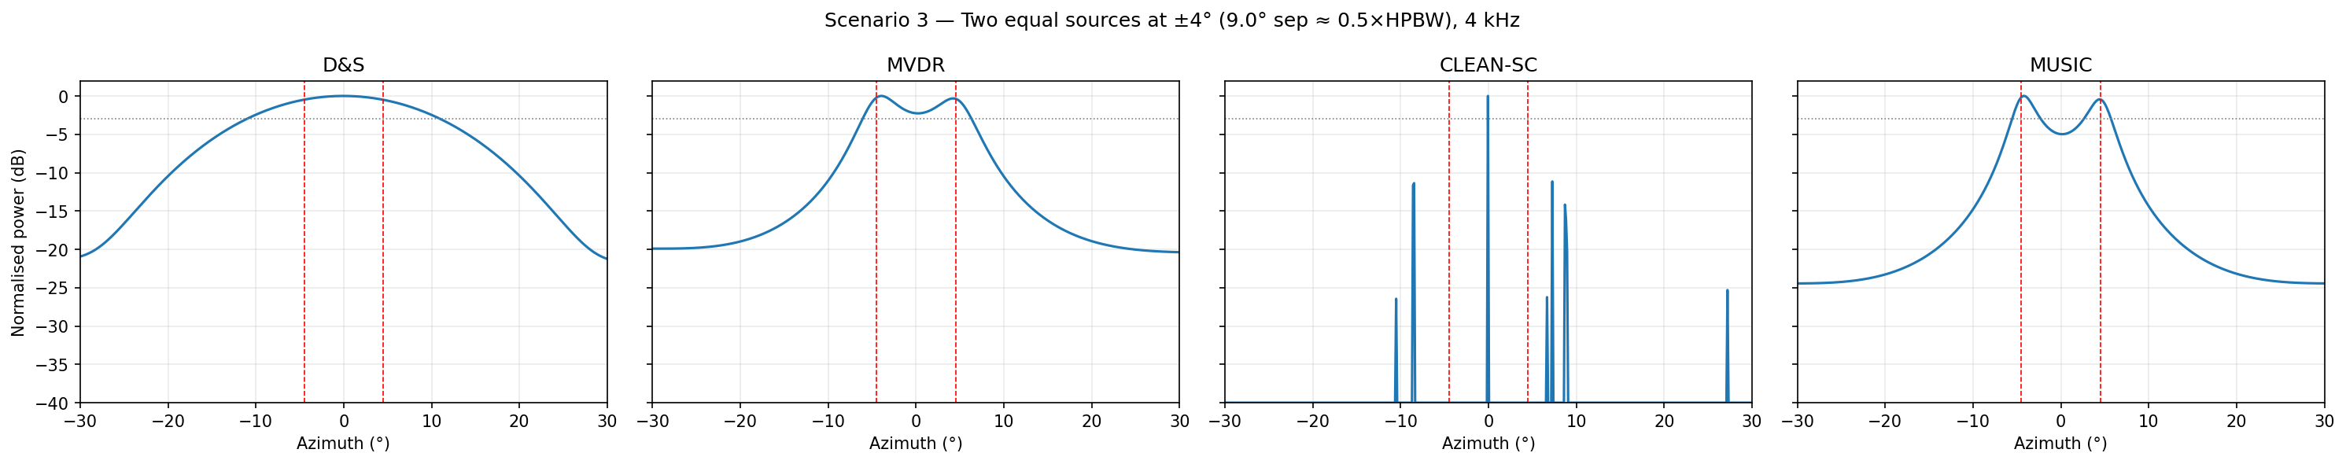
notebooks/algo_two_sources_close.png
