jduanen/Acoustic-Camera/notebooks/array_layouts.png

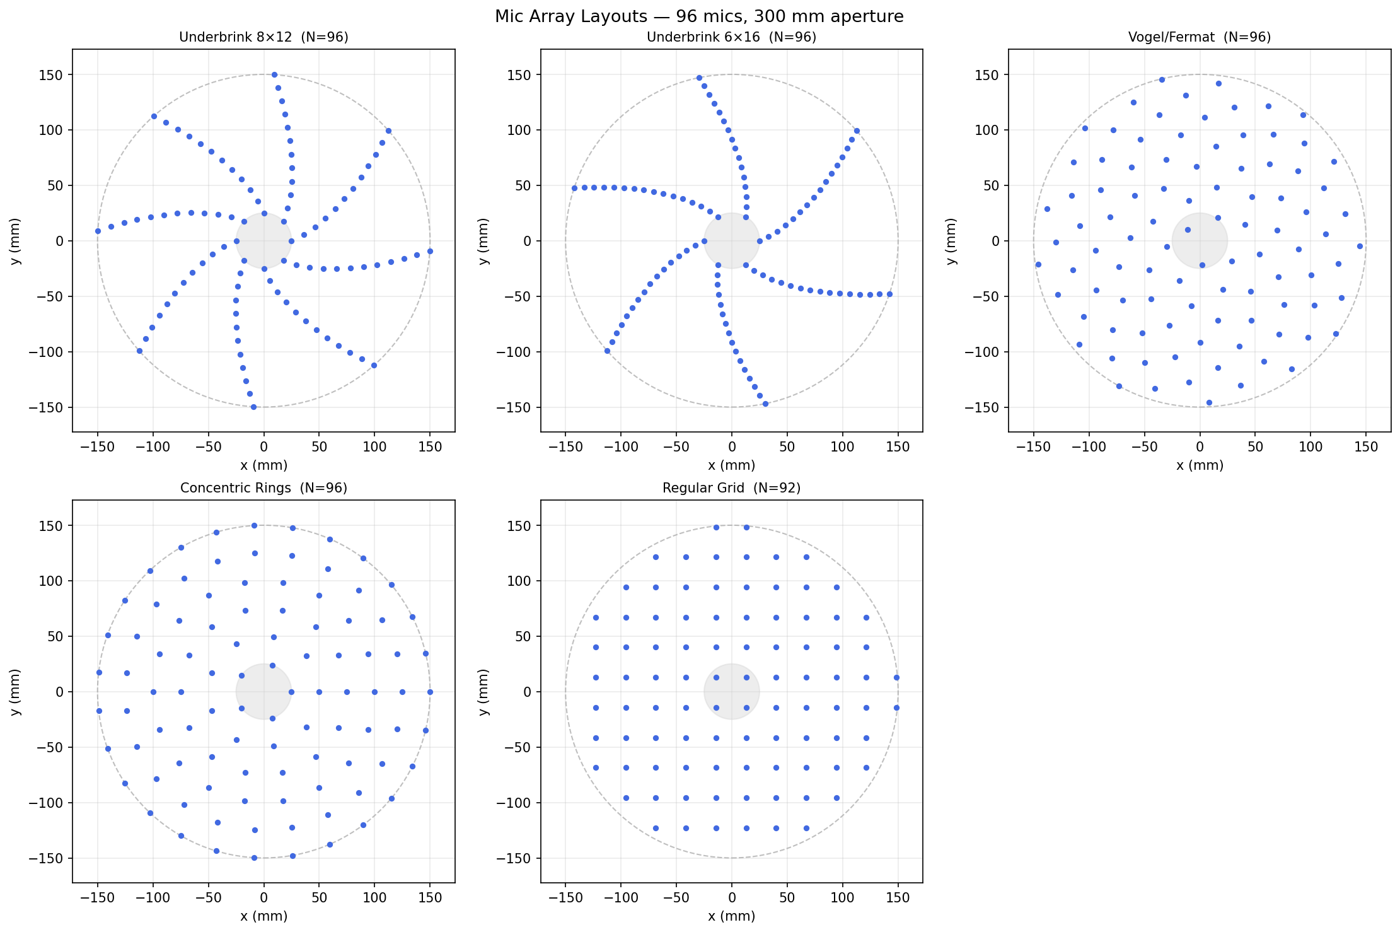
notebooks/array_layouts.png
