jduanen/Acoustic-Camera/notebooks/bb_algo_vs_freq.png

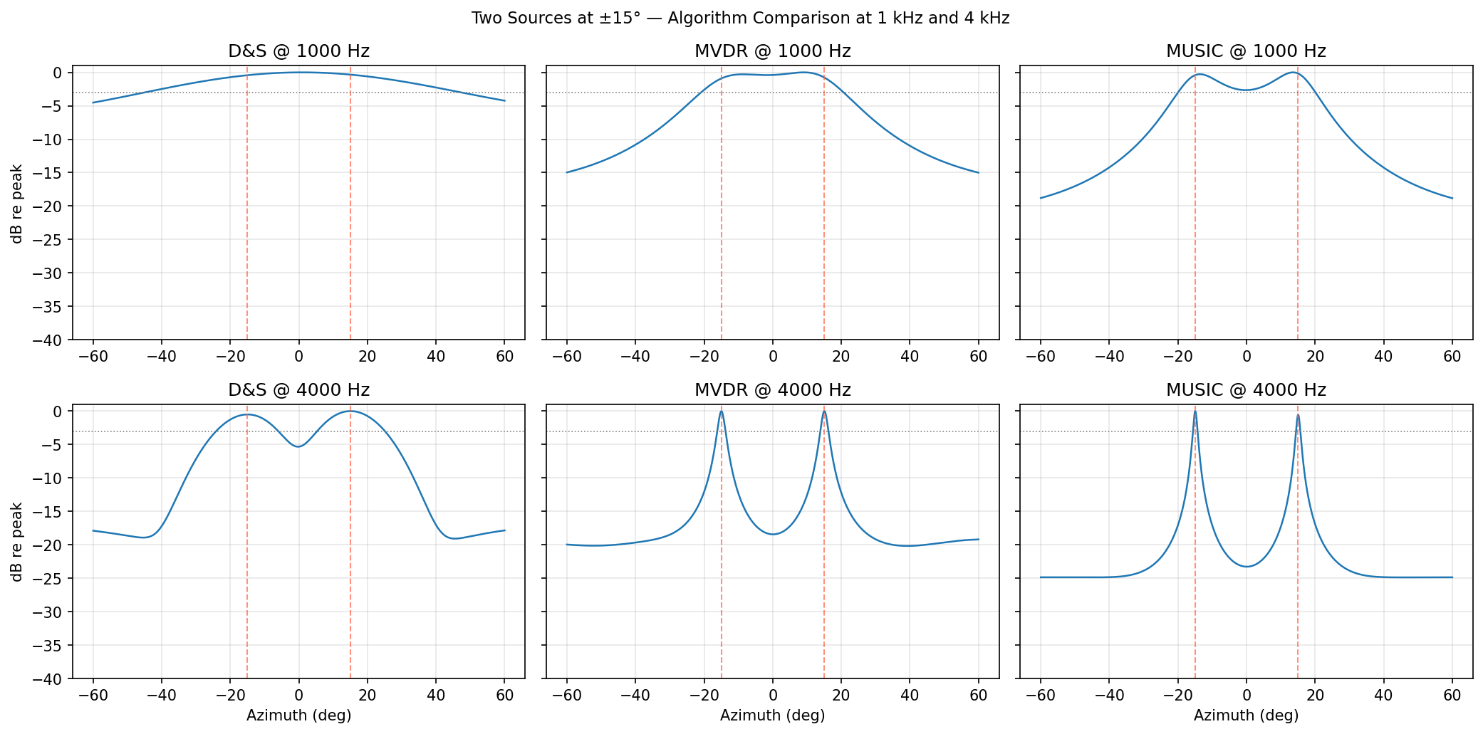
notebooks/bb_algo_vs_freq.png
