jduanen/Acoustic-Camera/notebooks/bb_aliasing.png

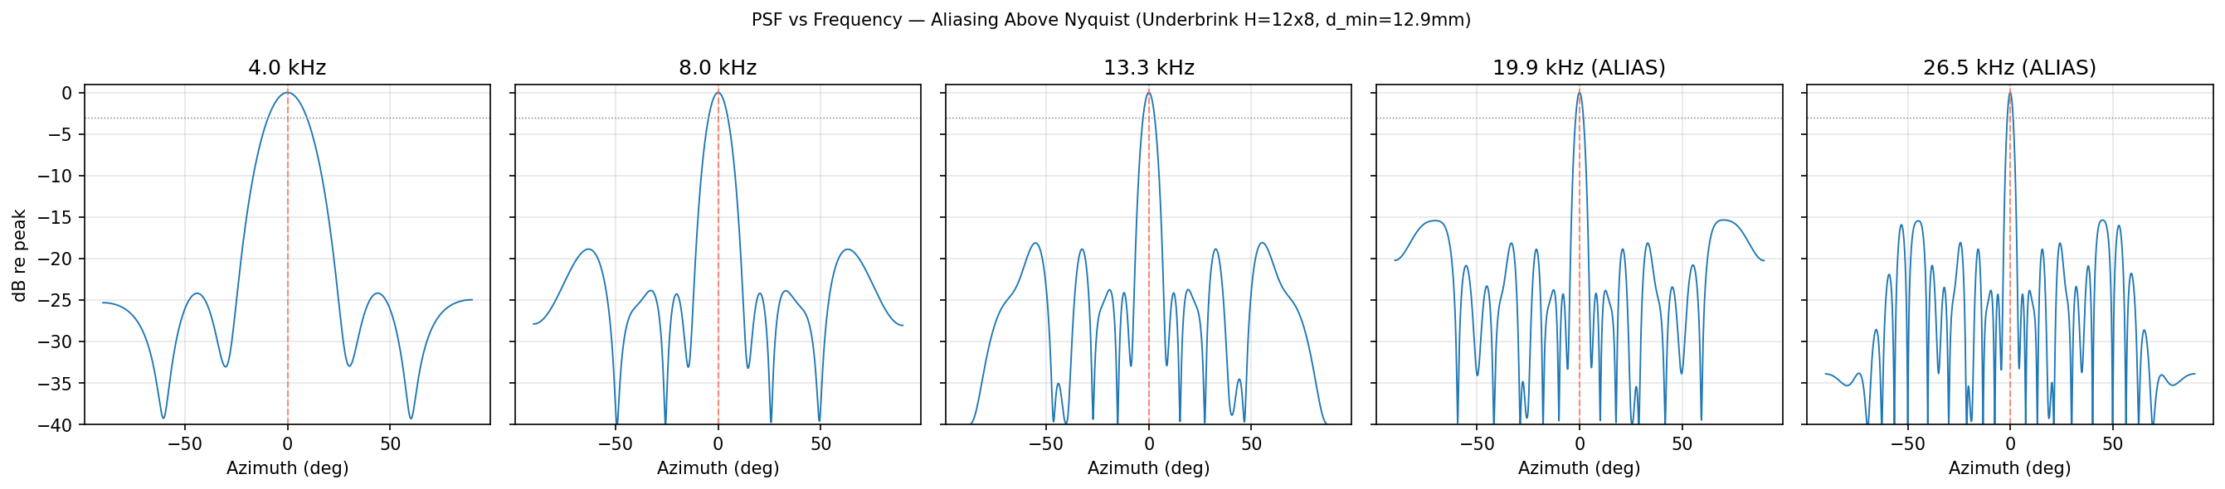
notebooks/bb_aliasing.png
