jduanen/Acoustic-Camera/notebooks/bb_hpbw_vs_freq.png

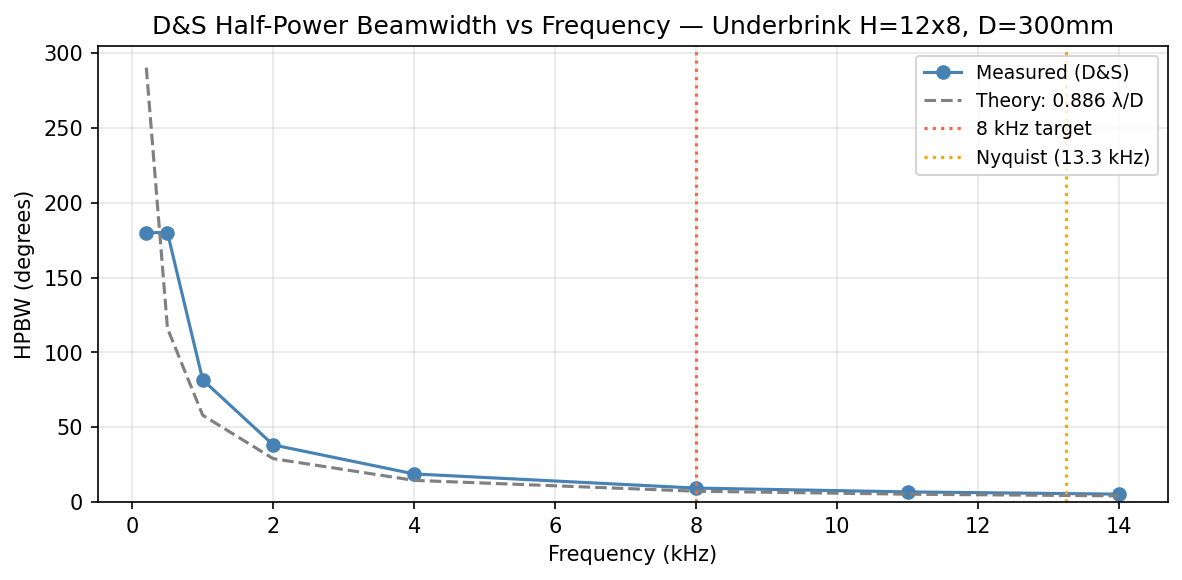
notebooks/bb_hpbw_vs_freq.png
