jduanen/Acoustic-Camera/notebooks/bb_octave_maps.png

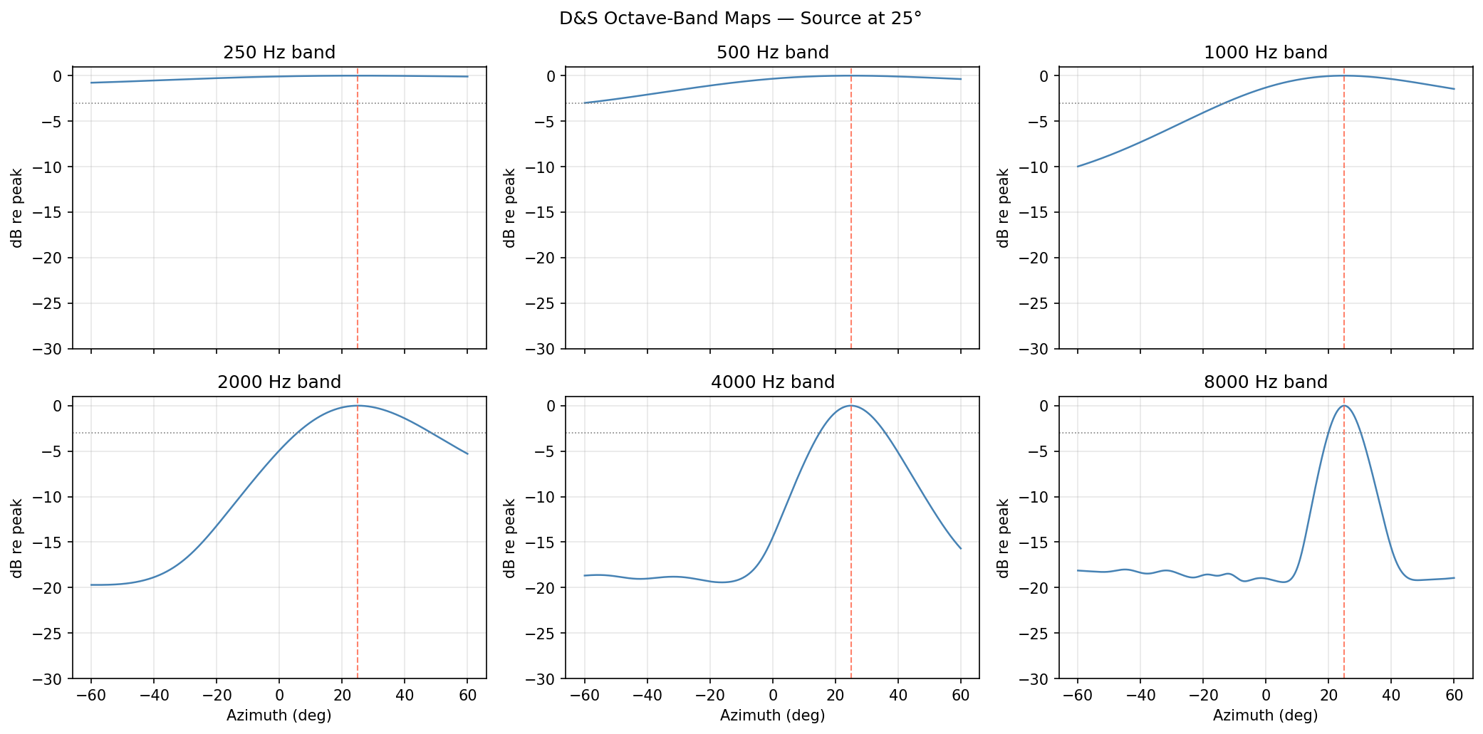
notebooks/bb_octave_maps.png
