jduanen/Acoustic-Camera/notebooks/bb_octave_overlay.png

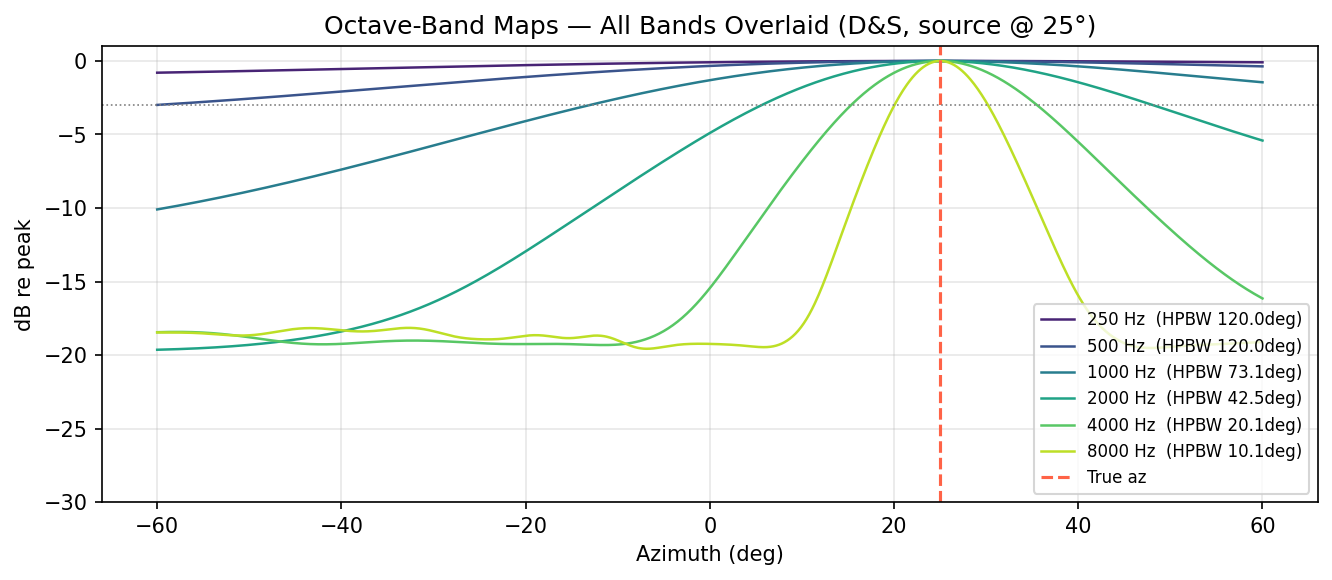
notebooks/bb_octave_overlay.png
