jduanen/Acoustic-Camera/notebooks/cal_correction_effect.png

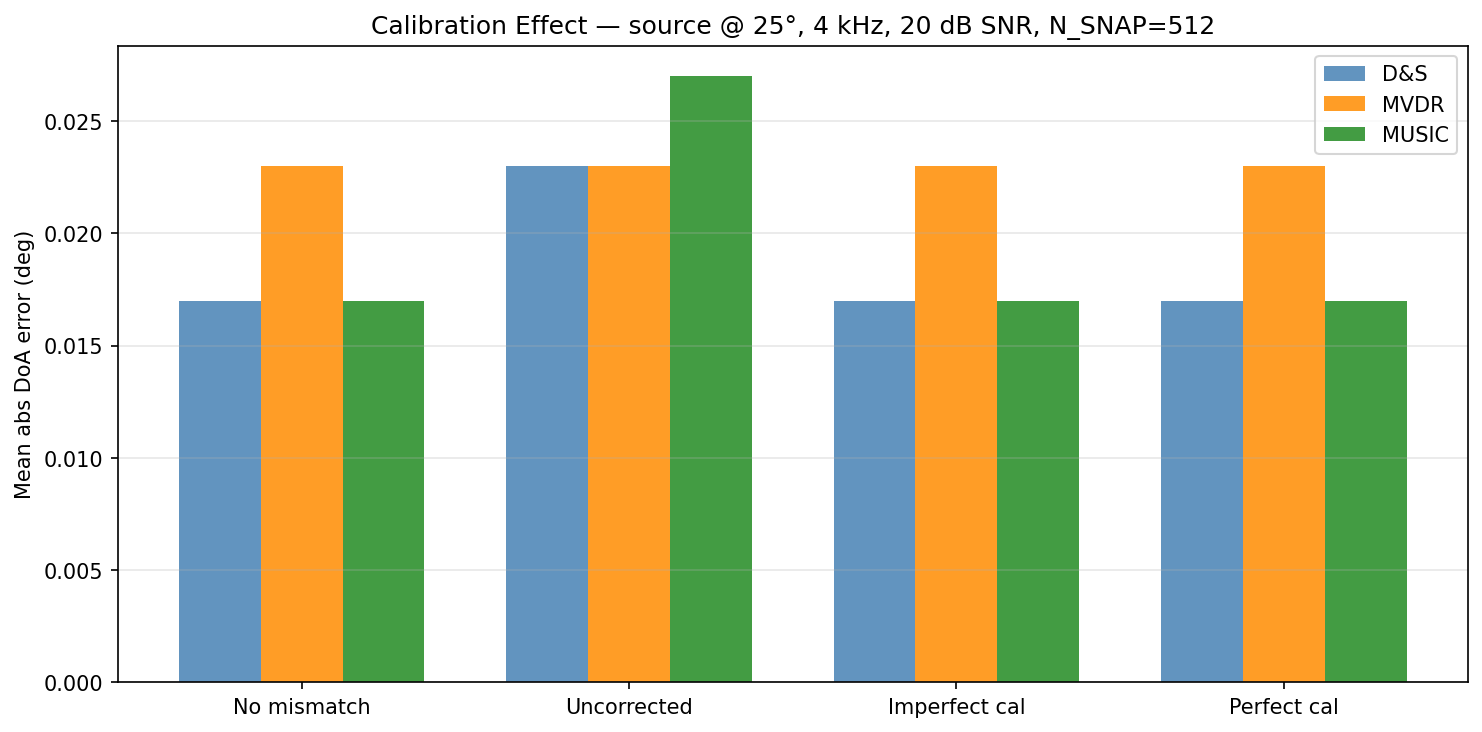
notebooks/cal_correction_effect.png
