jduanen/Acoustic-Camera/notebooks/cal_doa_vs_mismatch.png

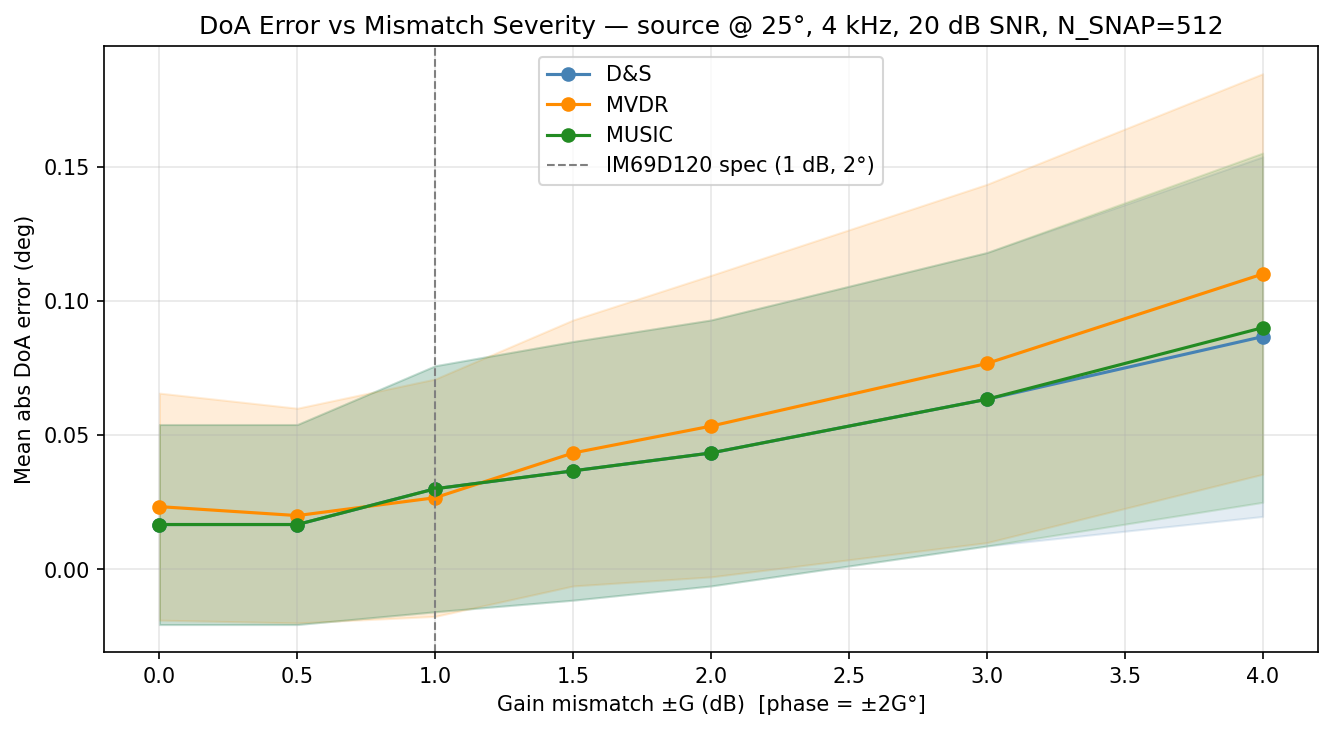
notebooks/cal_doa_vs_mismatch.png
