jduanen/Acoustic-Camera/notebooks/music_detect_vs_snap.png

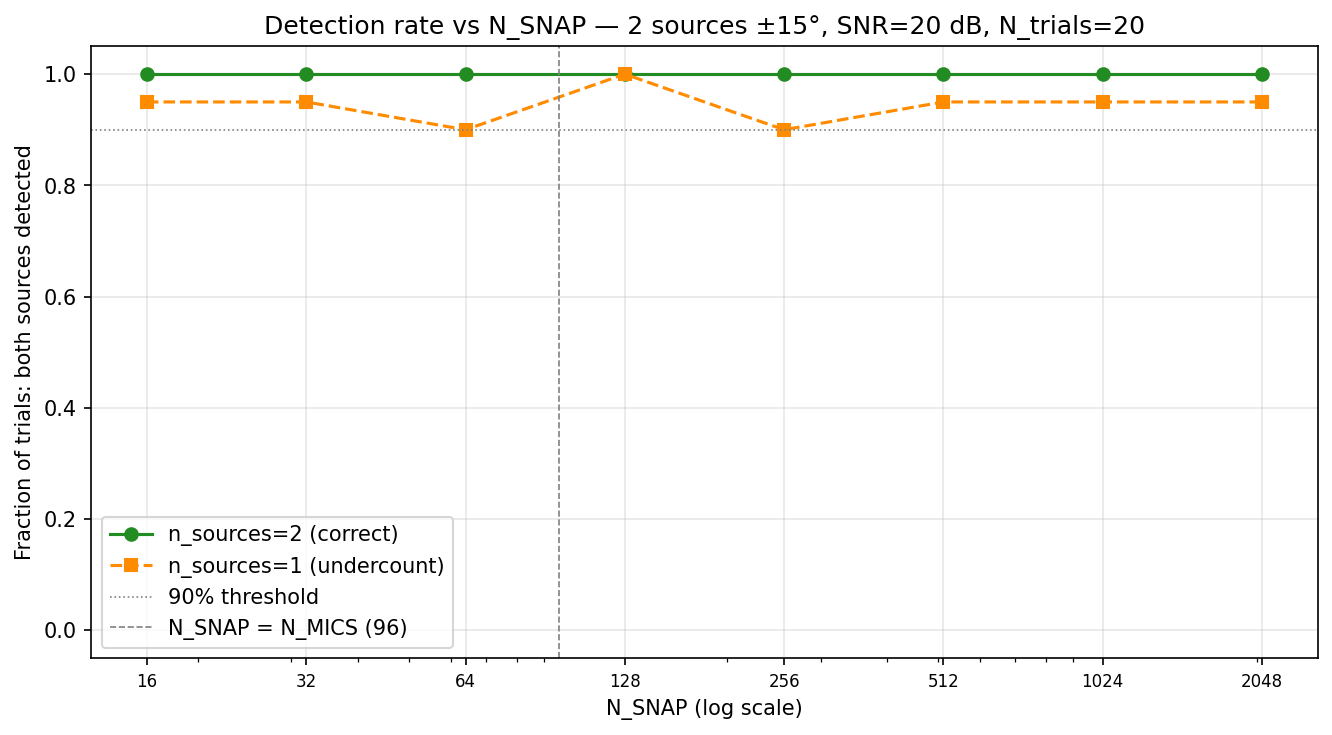
notebooks/music_detect_vs_snap.png
