jduanen/Acoustic-Camera/notebooks/music_detect_vs_snr.png

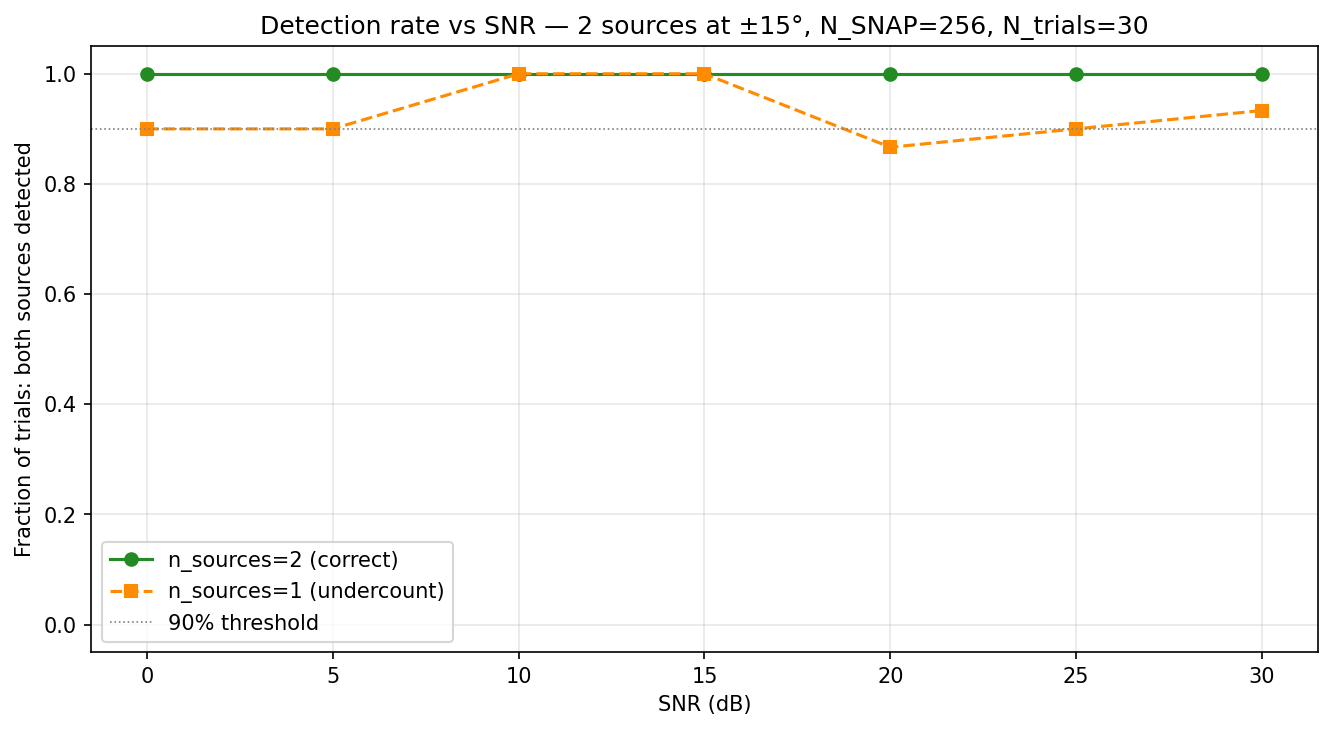
notebooks/music_detect_vs_snr.png
