jduanen/Acoustic-Camera/notebooks/music_fa_vs_snr.png

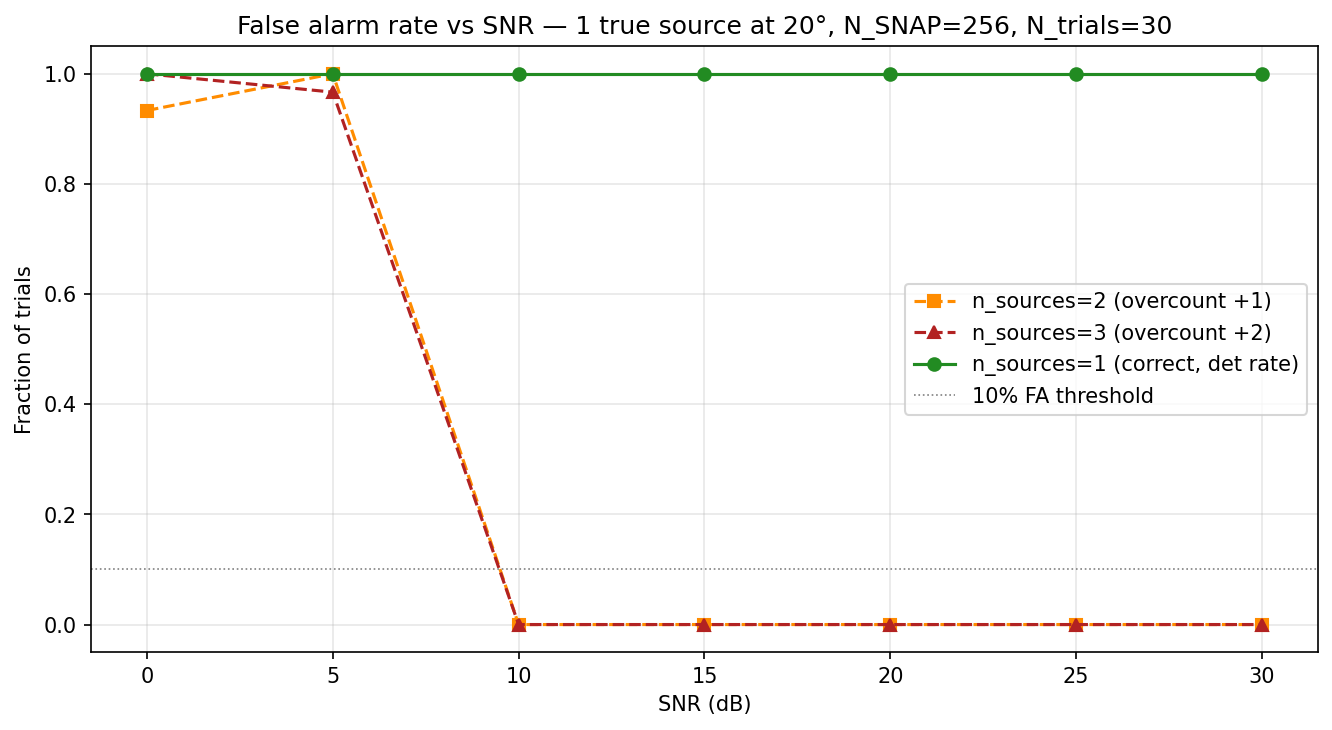
notebooks/music_fa_vs_snr.png
