jduanen/Acoustic-Camera/notebooks/music_spectrum_mismatch.png

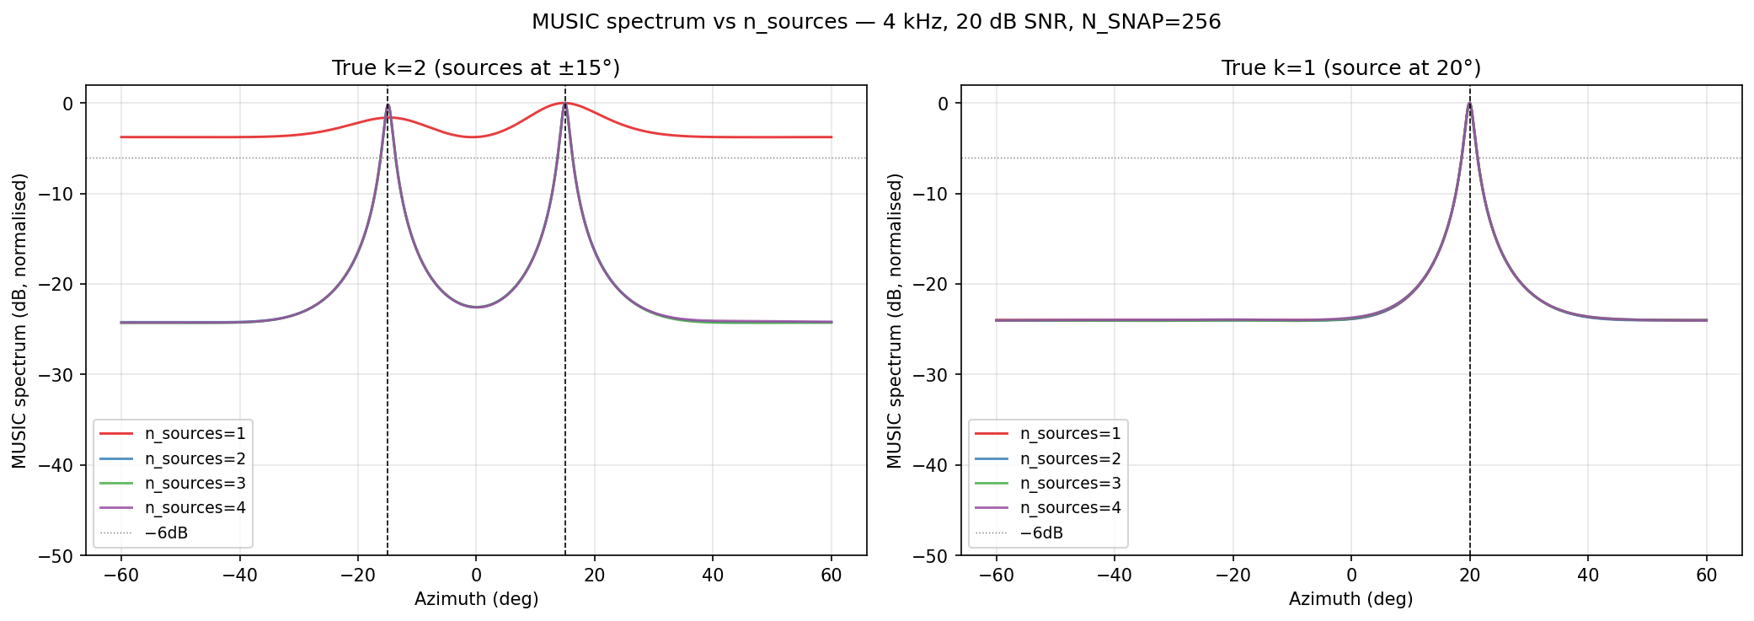
notebooks/music_spectrum_mismatch.png
