jduanen/Acoustic-Camera/notebooks/nf_1d_comparison.png

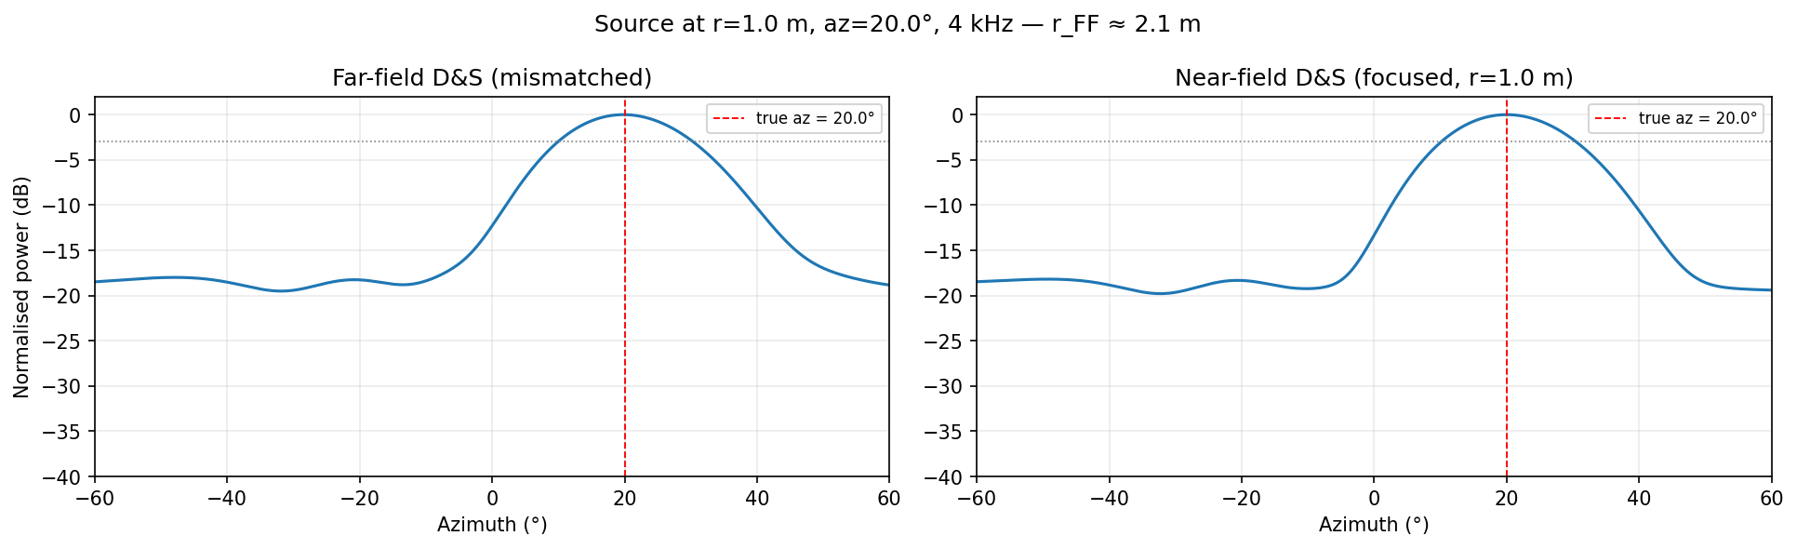
notebooks/nf_1d_comparison.png
