jduanen/Acoustic-Camera/notebooks/nf_cleansc_doa_vs_range.png

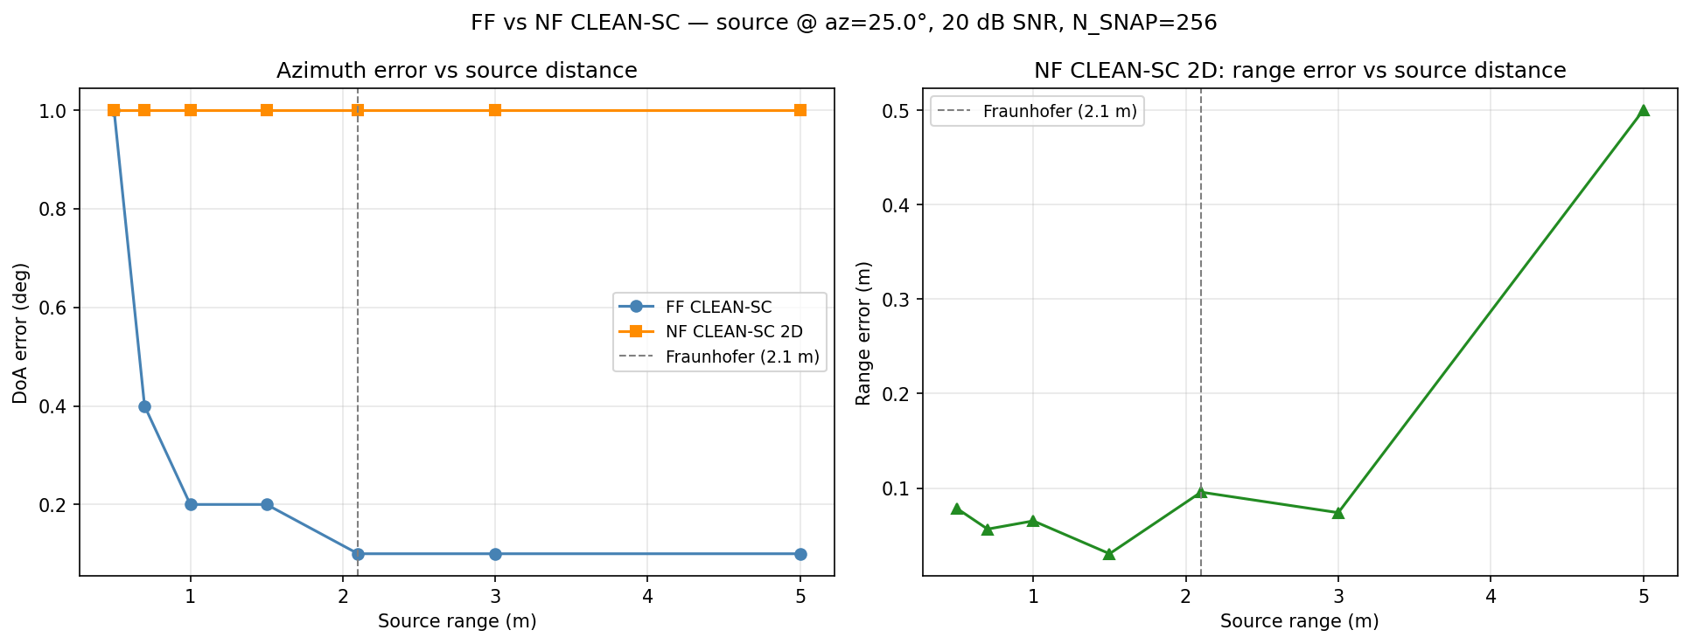
notebooks/nf_cleansc_doa_vs_range.png
