jduanen/Acoustic-Camera/notebooks/nf_cleansc_range_sep.png

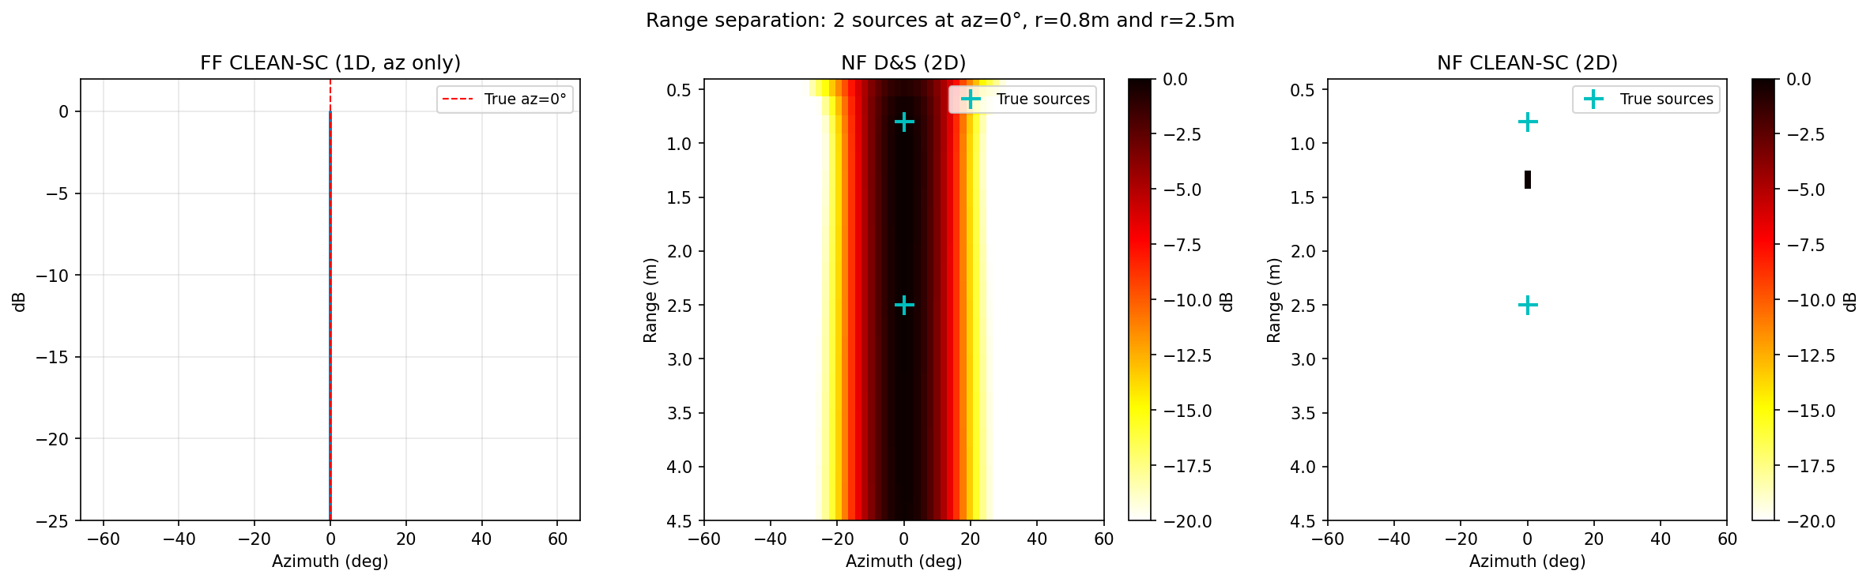
notebooks/nf_cleansc_range_sep.png
