jduanen/Acoustic-Camera/notebooks/nf_cleansc_single.png

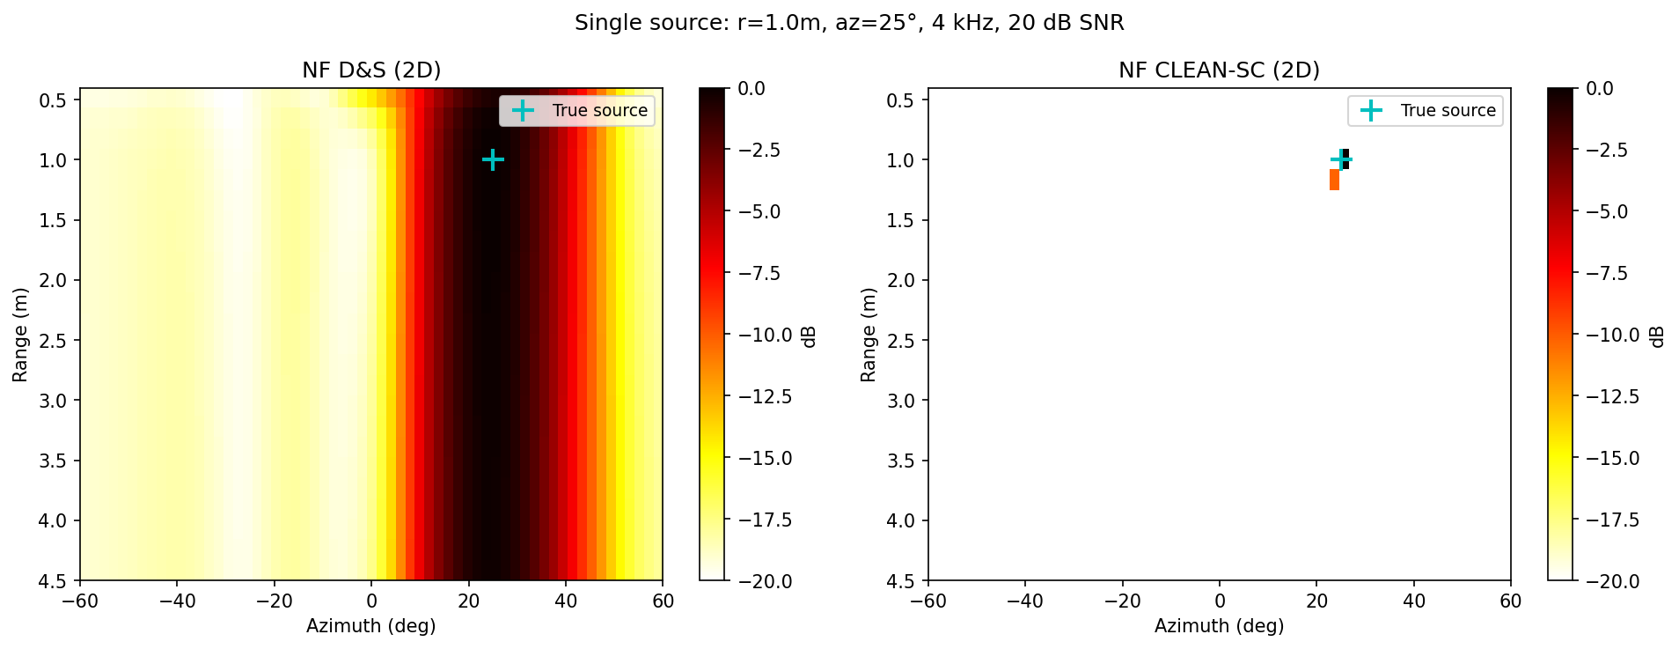
notebooks/nf_cleansc_single.png
