jduanen/Acoustic-Camera/notebooks/nf_cleansc_twosrc_2d.png

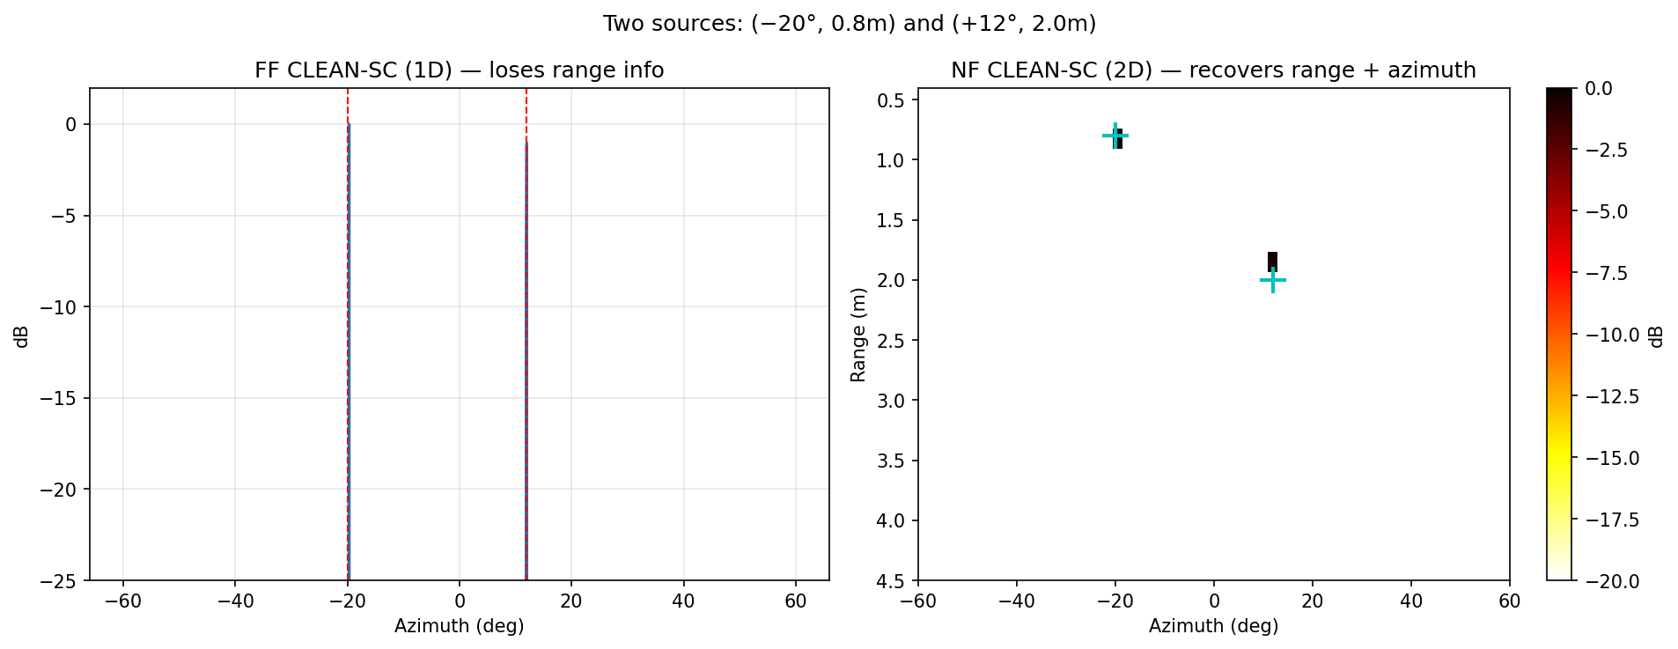
notebooks/nf_cleansc_twosrc_2d.png
