jduanen/Acoustic-Camera/notebooks/nf_criterion.png

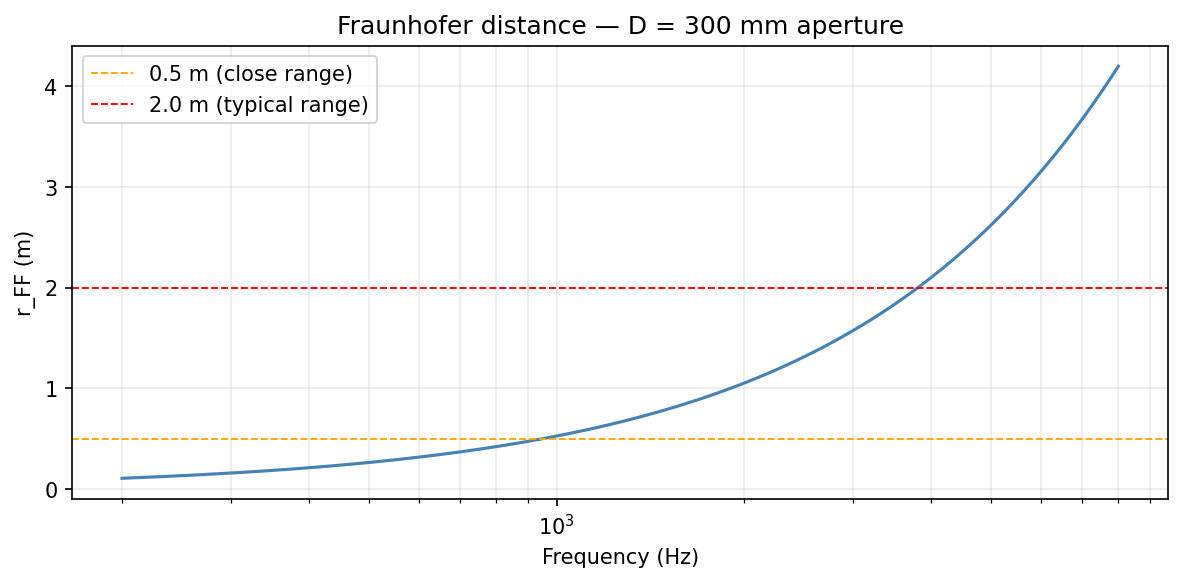
notebooks/nf_criterion.png
