jduanen/Acoustic-Camera/notebooks/nf_focused_2d.png

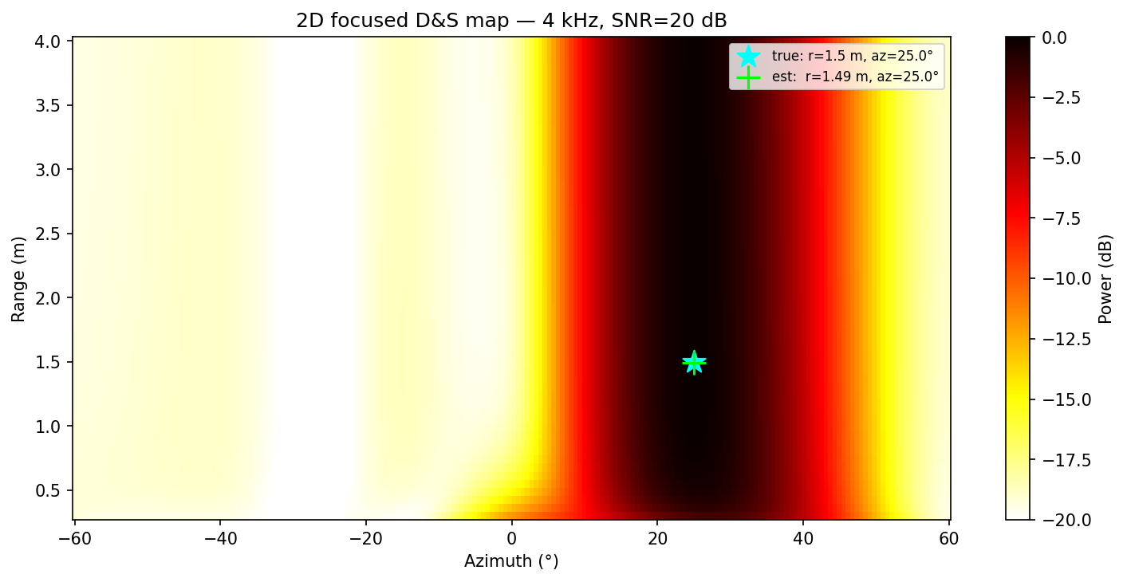
notebooks/nf_focused_2d.png
