jduanen/Acoustic-Camera/notebooks/nf_focused_2d_twosrc.png

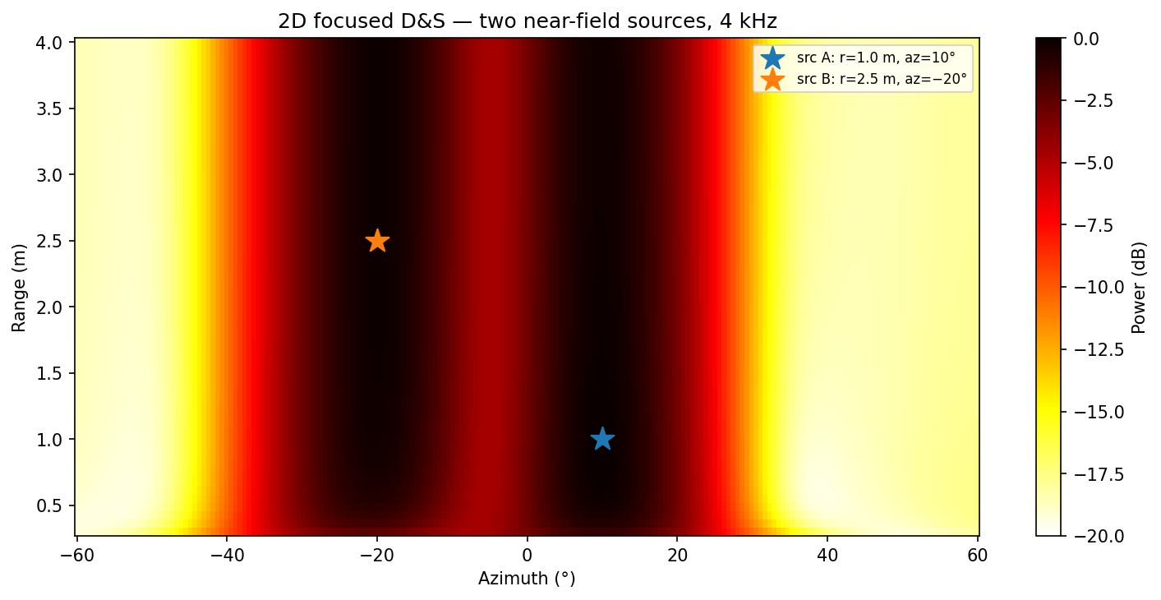
notebooks/nf_focused_2d_twosrc.png
