jduanen/Acoustic-Camera/notebooks/nf_range_sweep.png

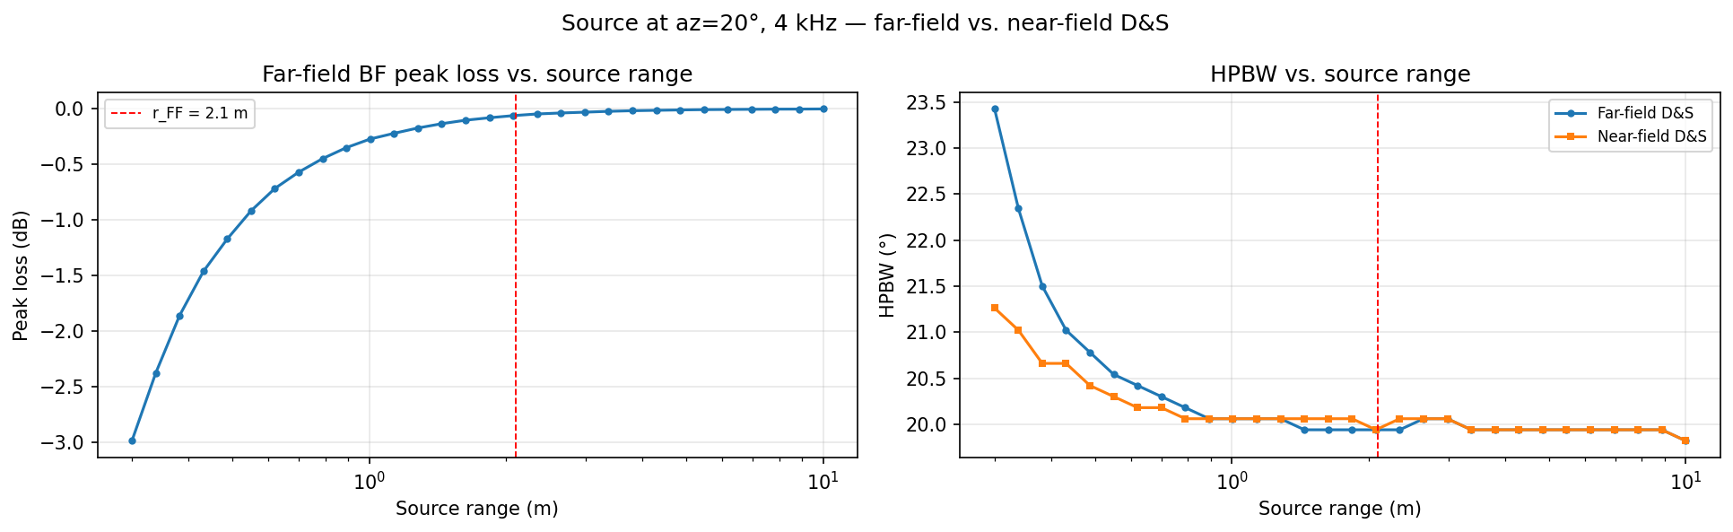
notebooks/nf_range_sweep.png
