jduanen/Acoustic-Camera/notebooks/psf_2d_final_comparison.png

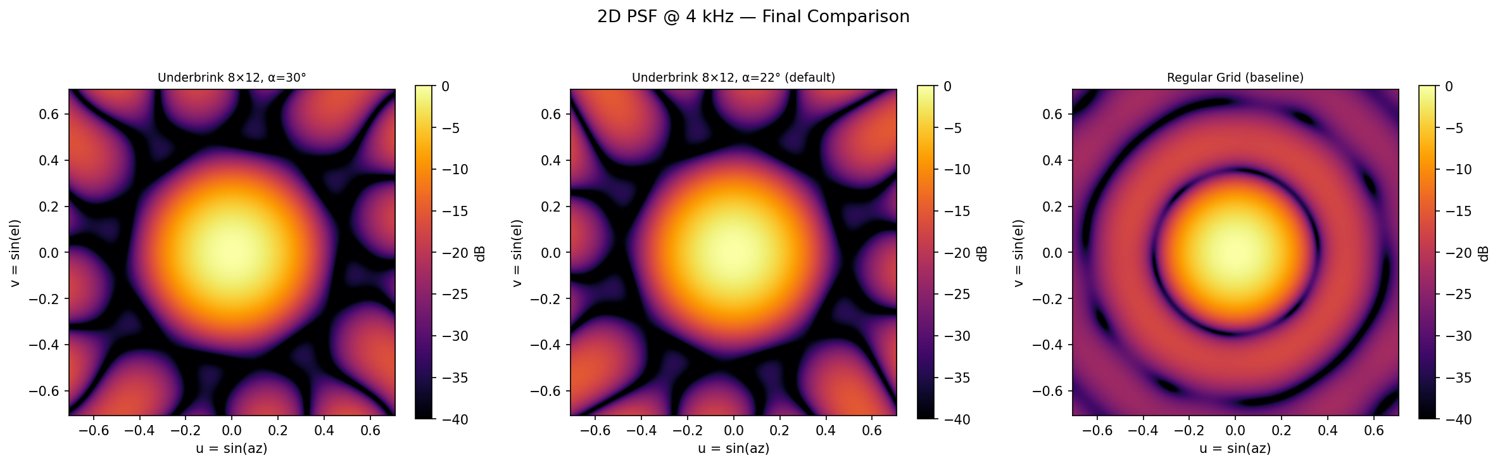
notebooks/psf_2d_final_comparison.png
