jduanen/Acoustic-Camera/notebooks/psf_2d_underbrink_8x12.png

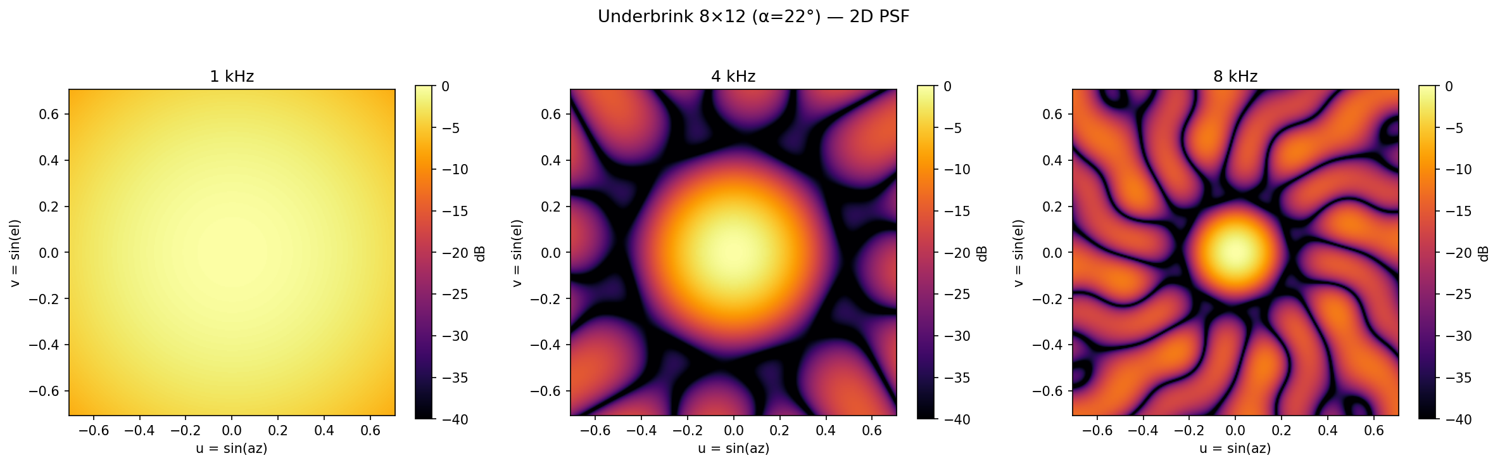
notebooks/psf_2d_underbrink_8x12.png
