jduanen/Acoustic-Camera/notebooks/psf_angle_comparison.png

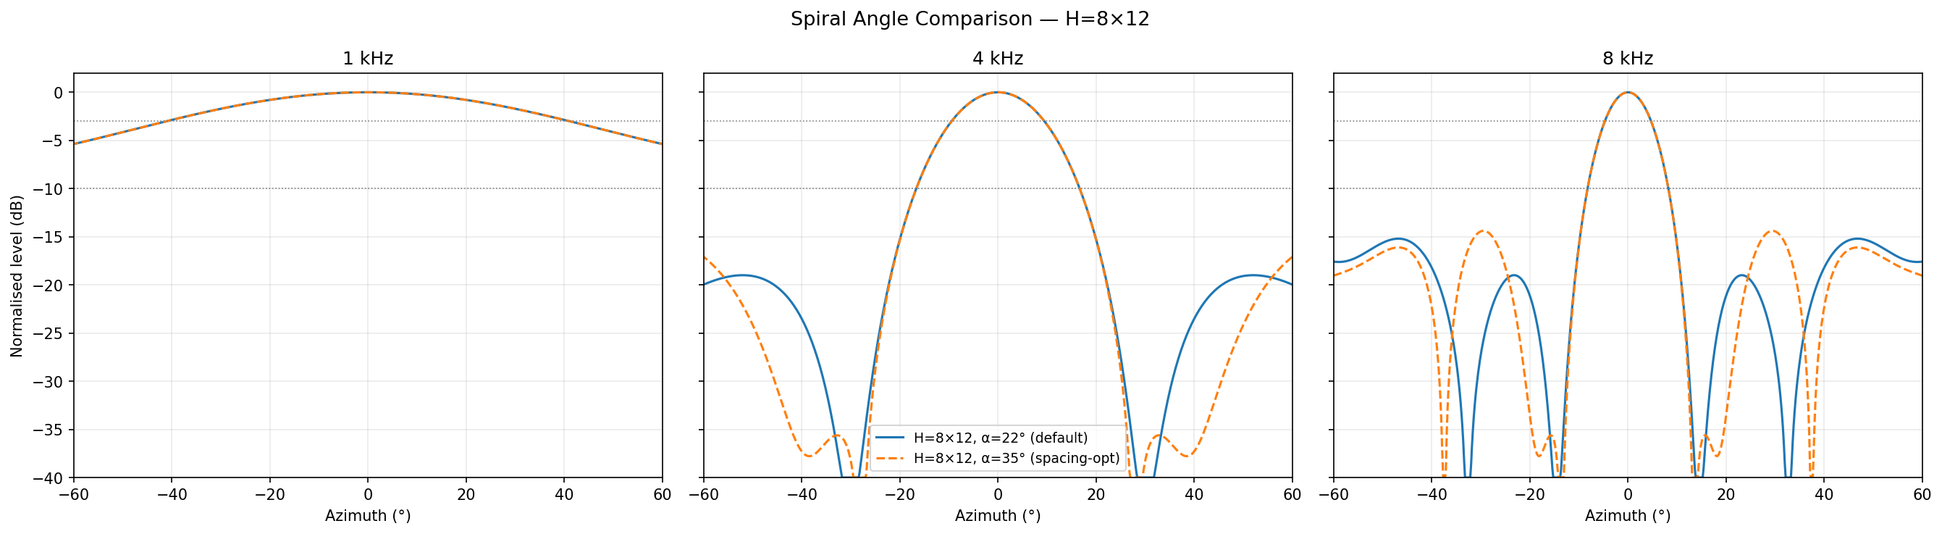
notebooks/psf_angle_comparison.png
