jduanen/Acoustic-Camera/notebooks/psf_angle_vs_metrics.png

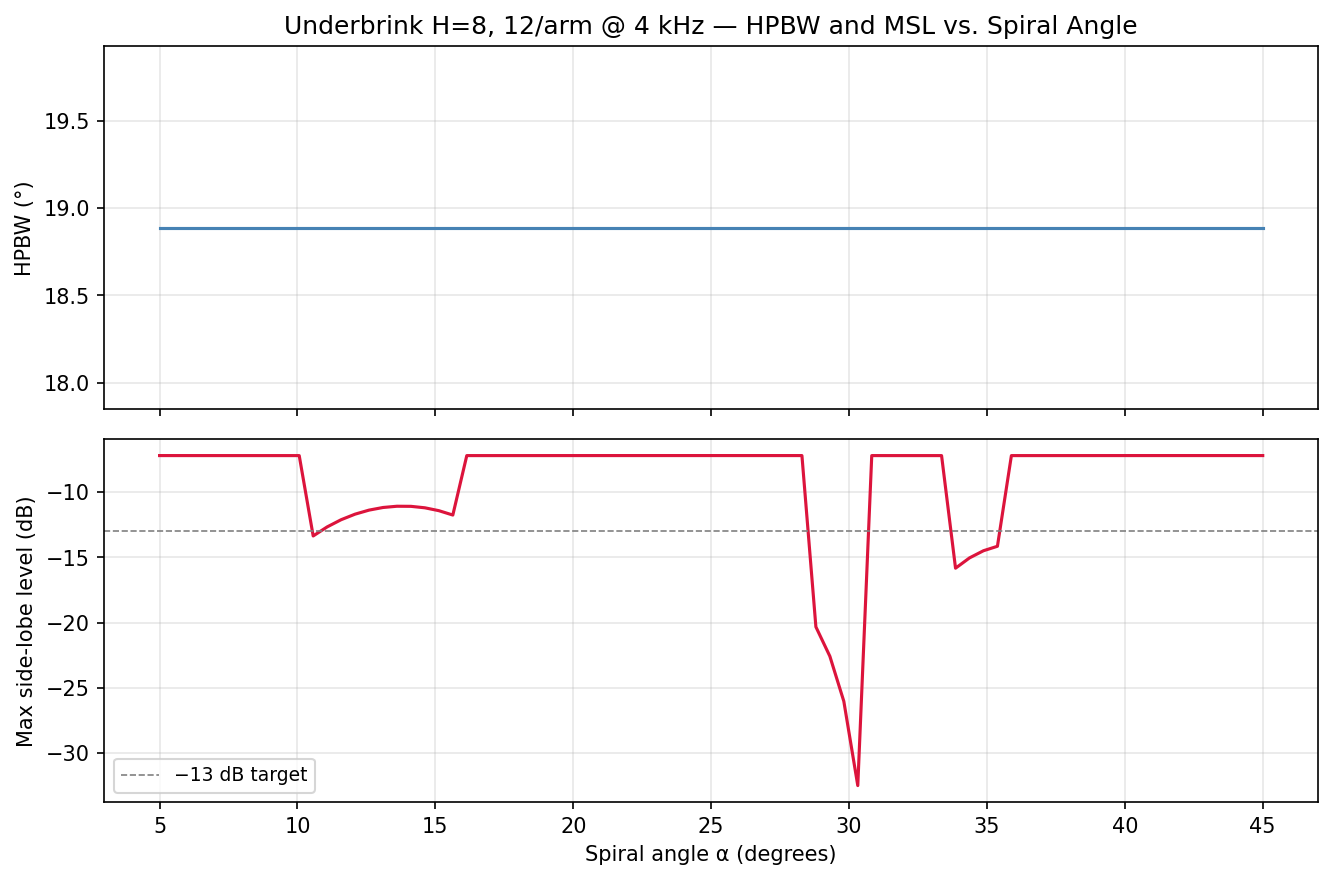
notebooks/psf_angle_vs_metrics.png
