jduanen/Acoustic-Camera/notebooks/psf_arms_sweep_4kHz.png

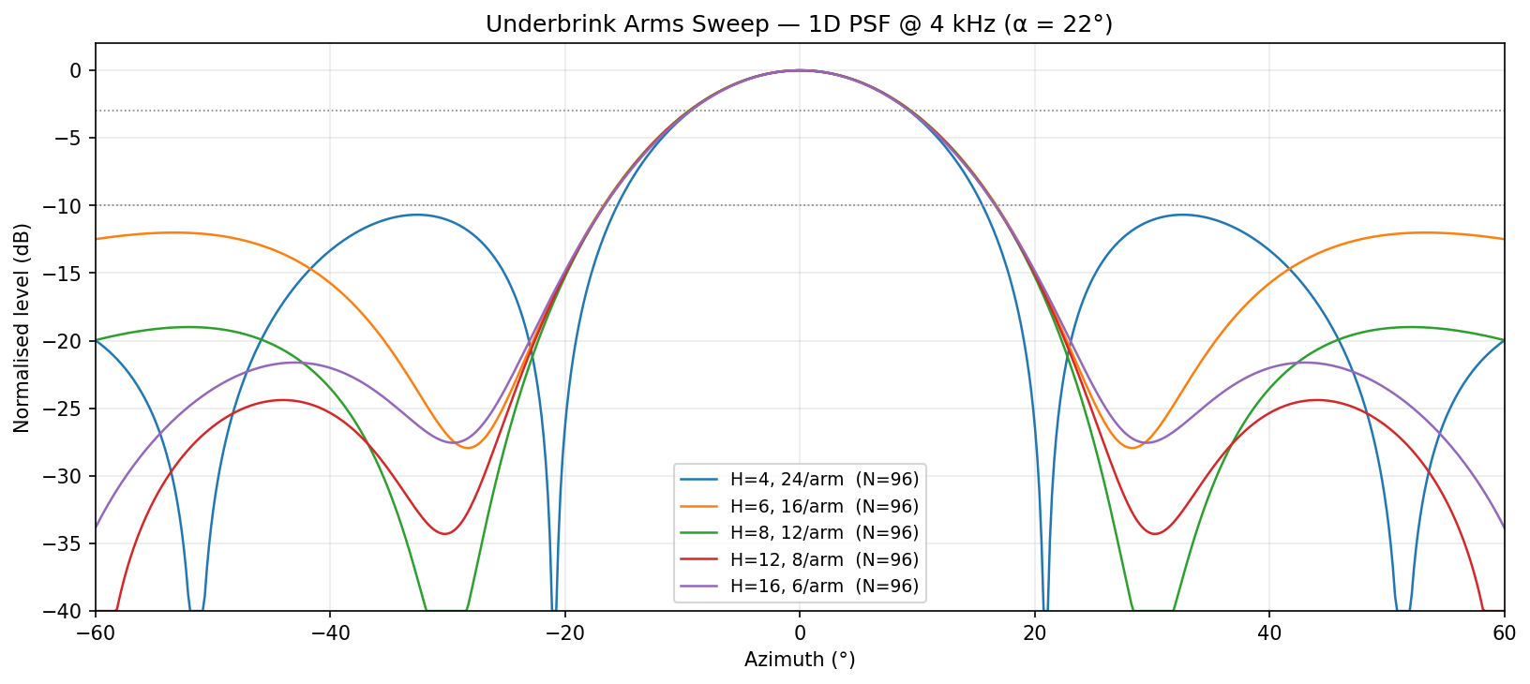
notebooks/psf_arms_sweep_4kHz.png
