jduanen/Acoustic-Camera/notebooks/psf_pattern_comparison.png

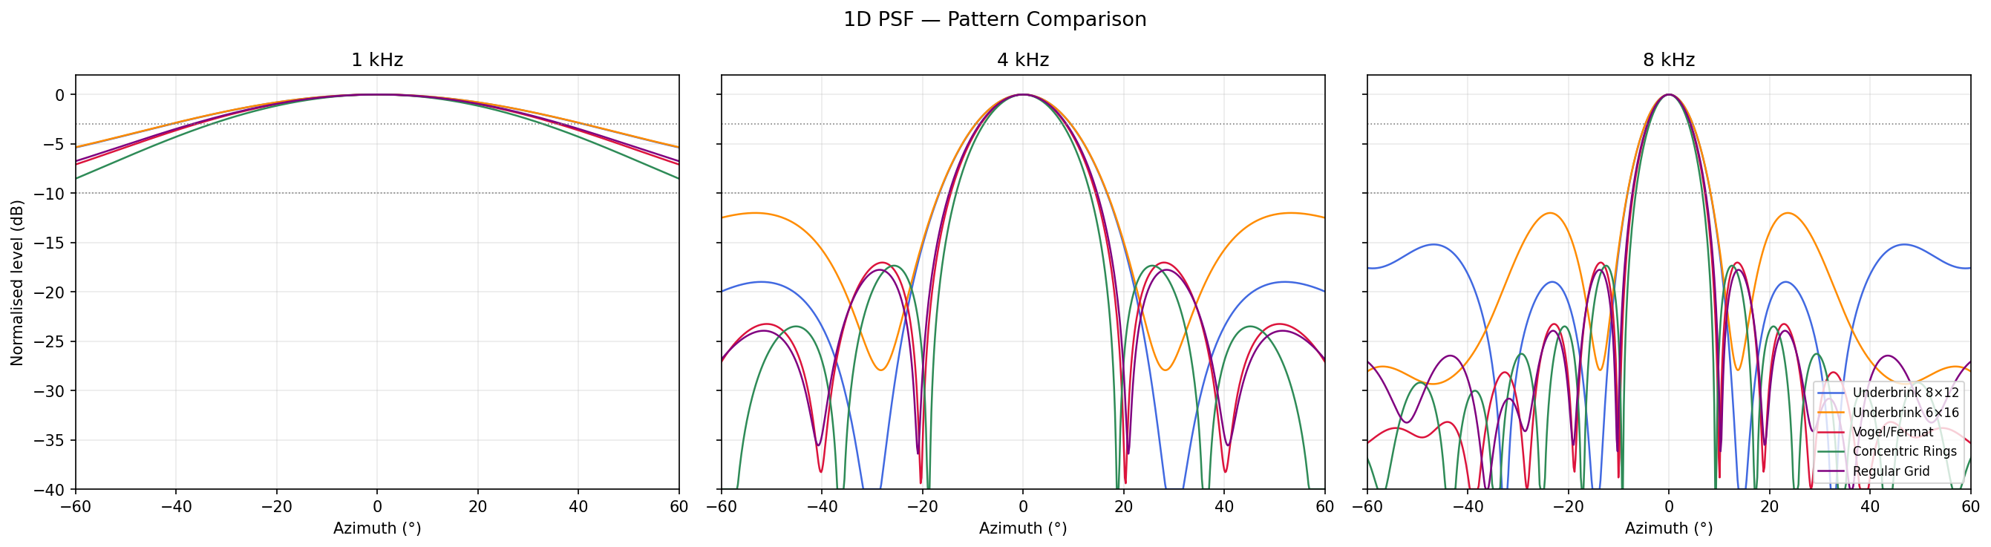
notebooks/psf_pattern_comparison.png
