jduanen/Acoustic-Camera/notebooks/respeaker_algo_comparison.png

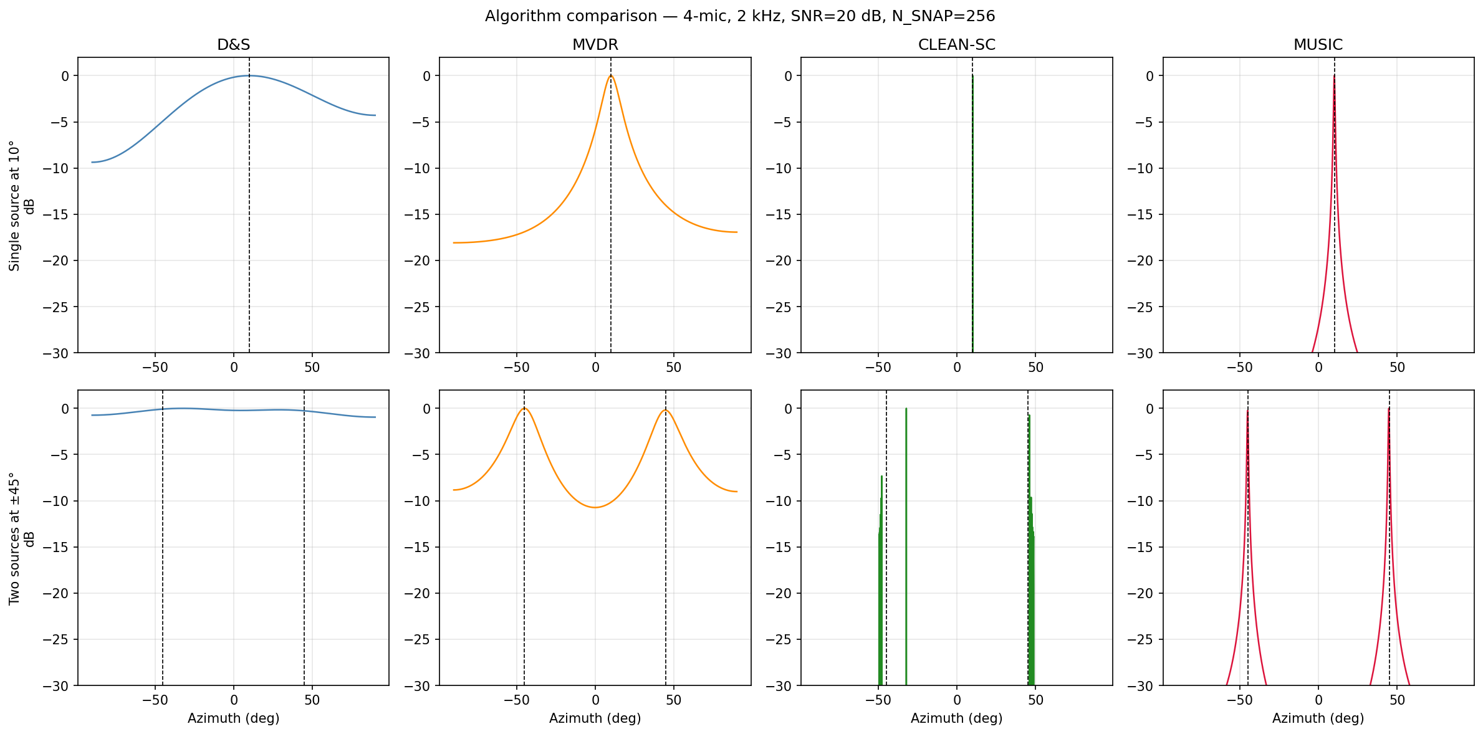
notebooks/respeaker_algo_comparison.png
