jduanen/Acoustic-Camera/notebooks/respeaker_aliasing.png

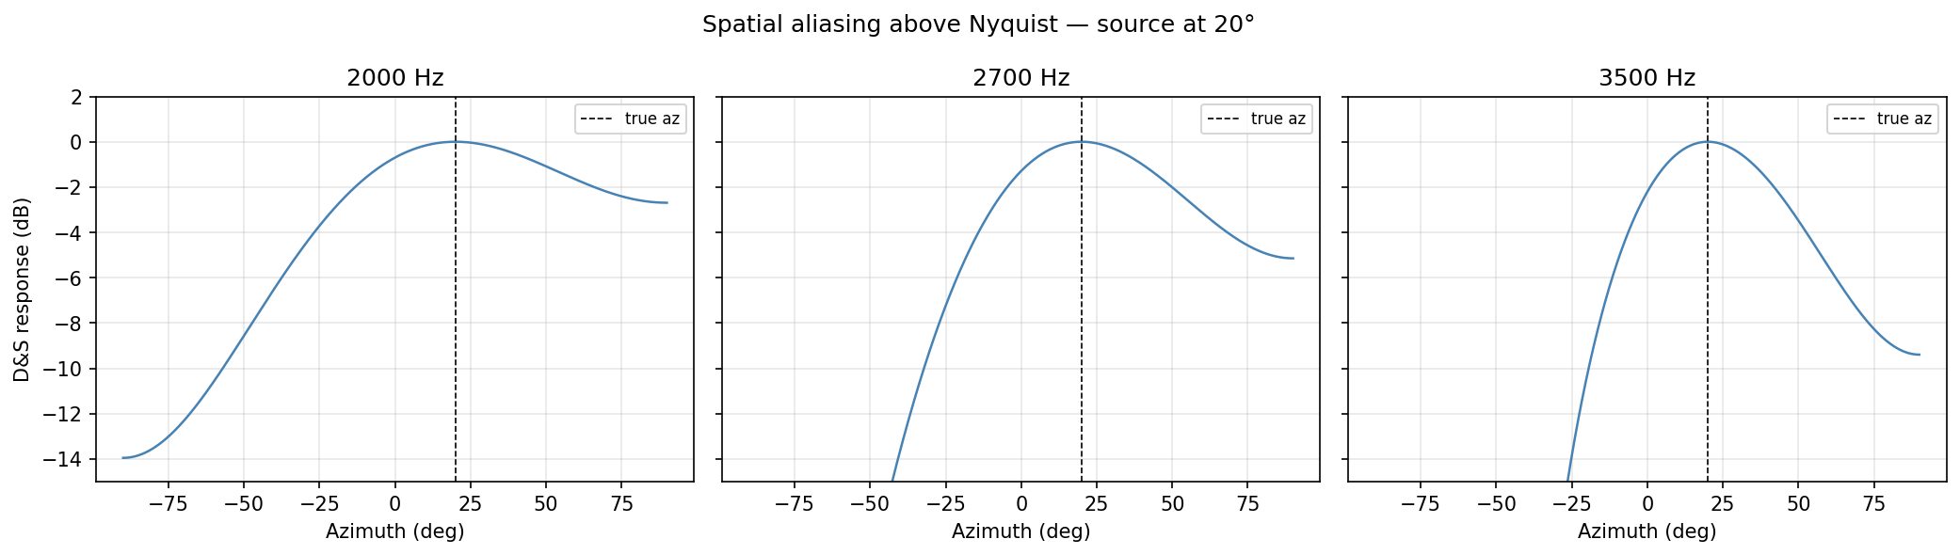
notebooks/respeaker_aliasing.png
