jduanen/Acoustic-Camera/notebooks/respeaker_beamform.png

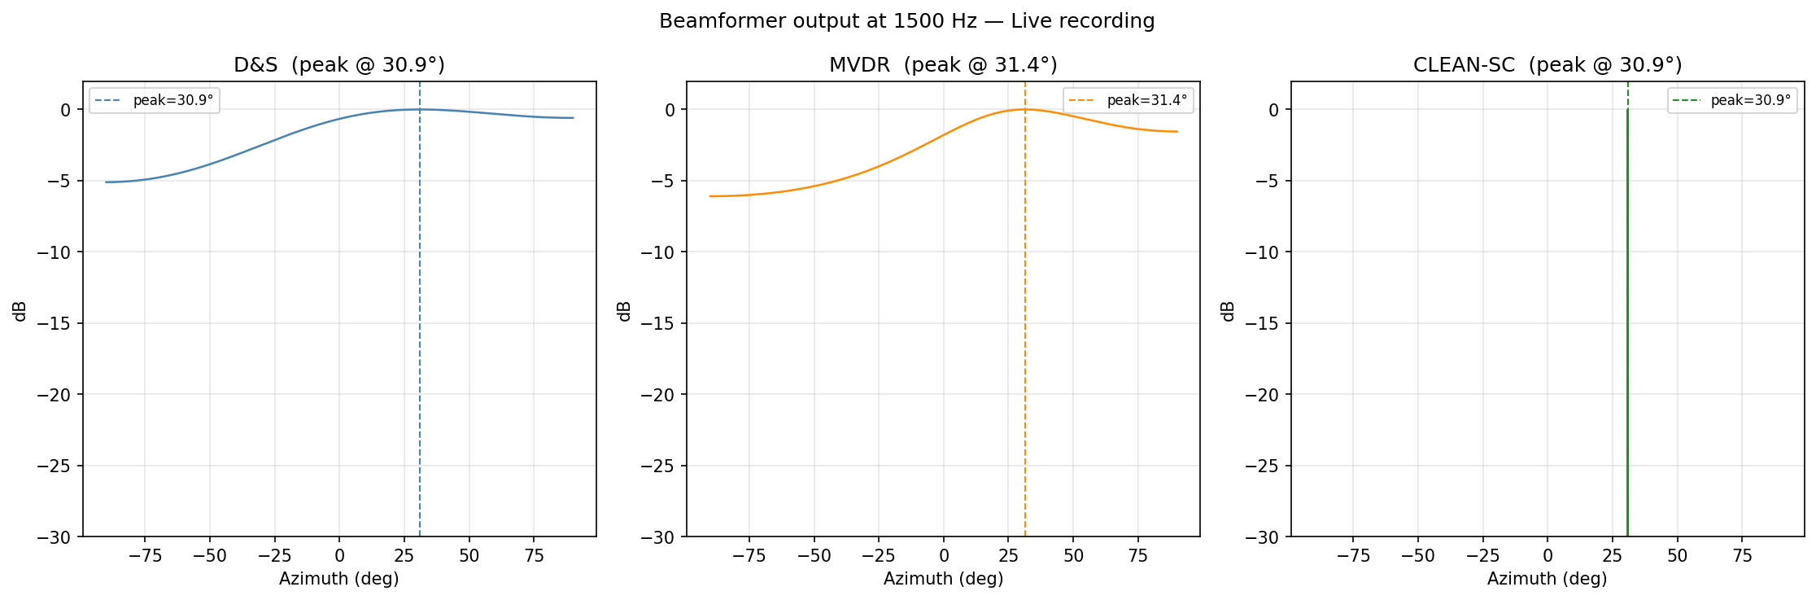
notebooks/respeaker_beamform.png
