jduanen/Acoustic-Camera/notebooks/respeaker_cal_csm.png

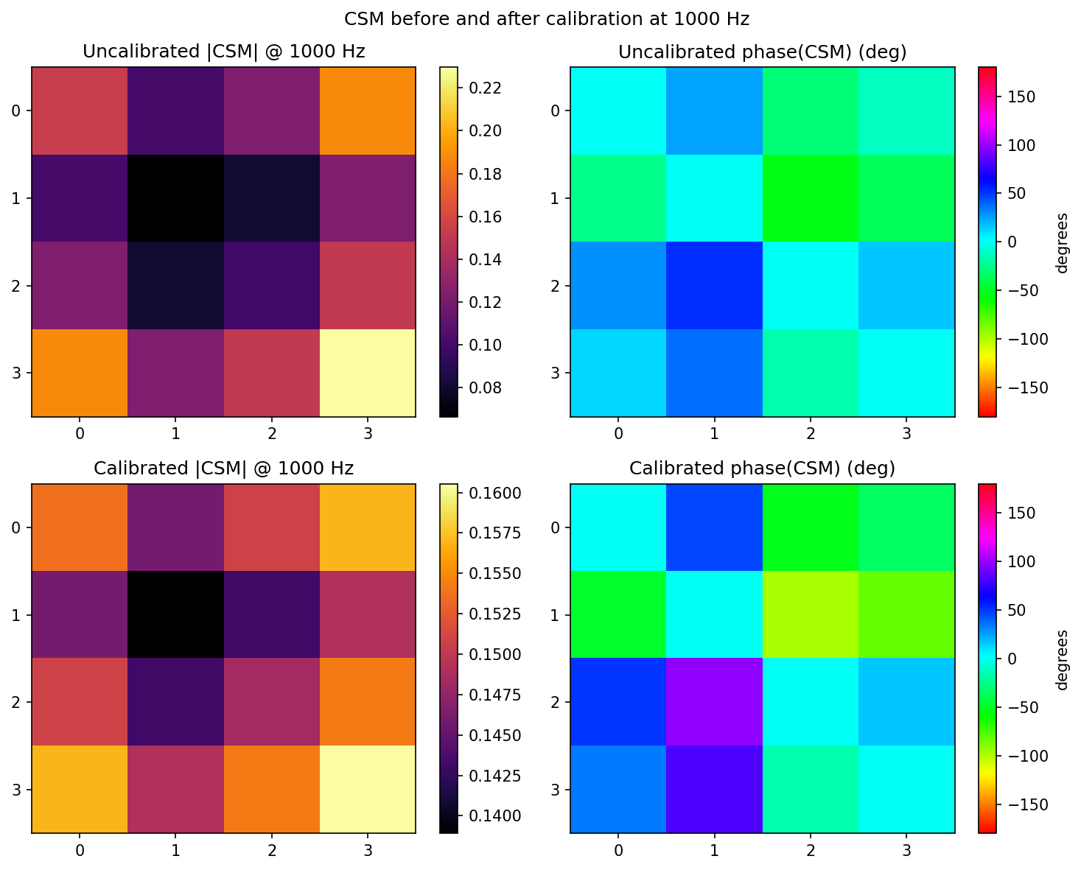
notebooks/respeaker_cal_csm.png
