jduanen/Acoustic-Camera/notebooks/respeaker_cal_doa_ref.png

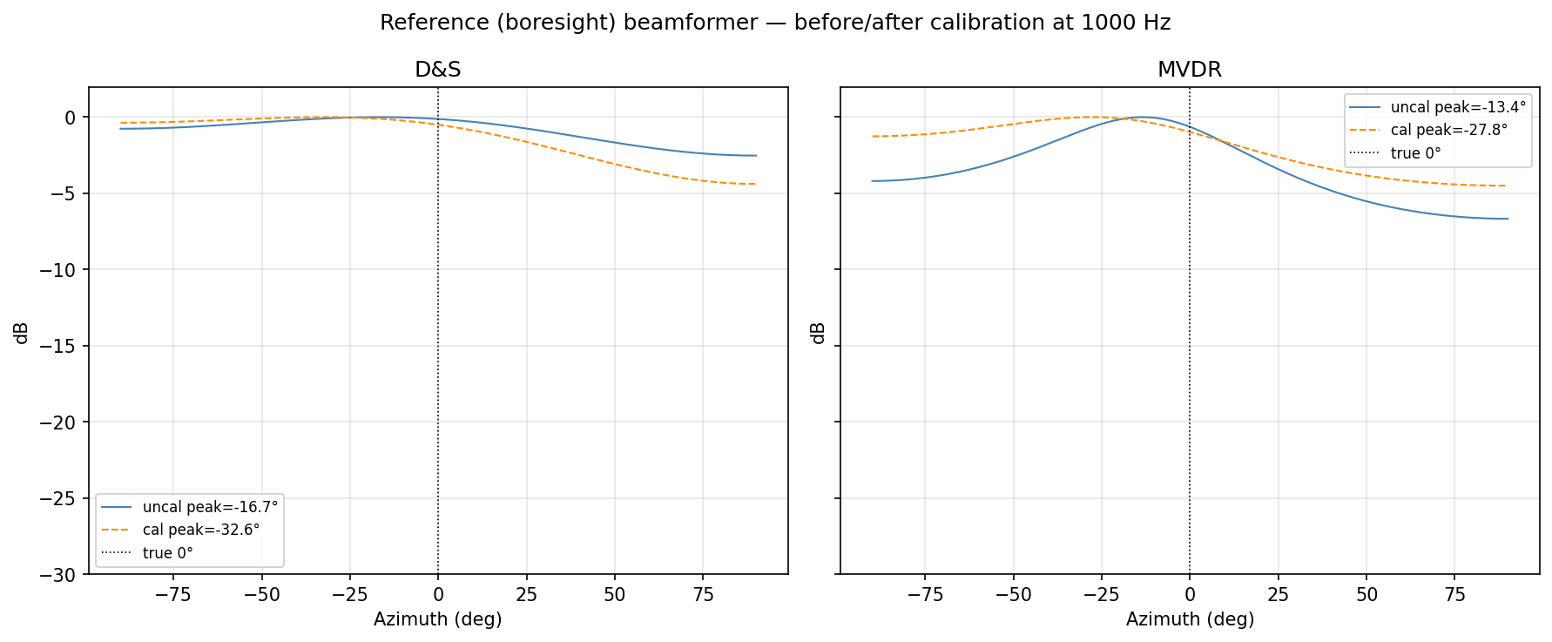
notebooks/respeaker_cal_doa_ref.png
