jduanen/Acoustic-Camera/notebooks/respeaker_channels_waveform.png

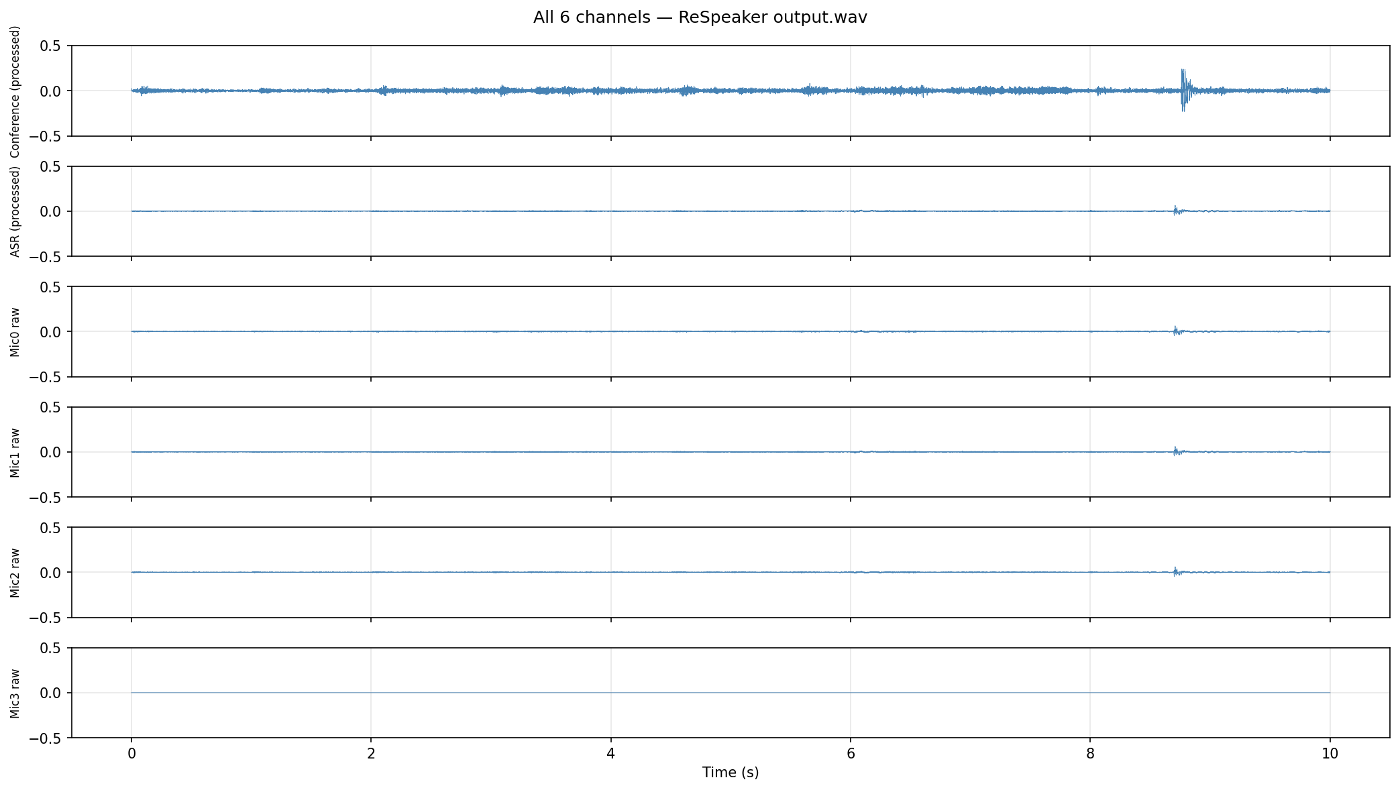
notebooks/respeaker_channels_waveform.png
