jduanen/Acoustic-Camera/notebooks/respeaker_csm.png

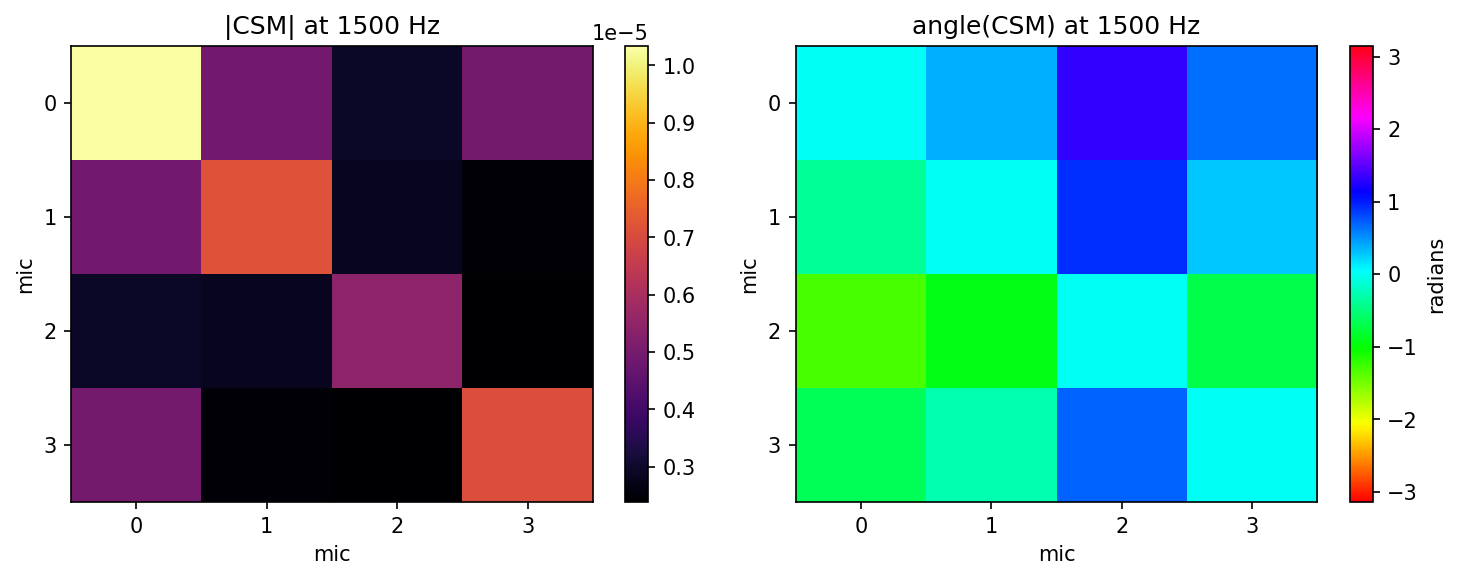
notebooks/respeaker_csm.png
