jduanen/Acoustic-Camera/notebooks/respeaker_freq_sweep.png

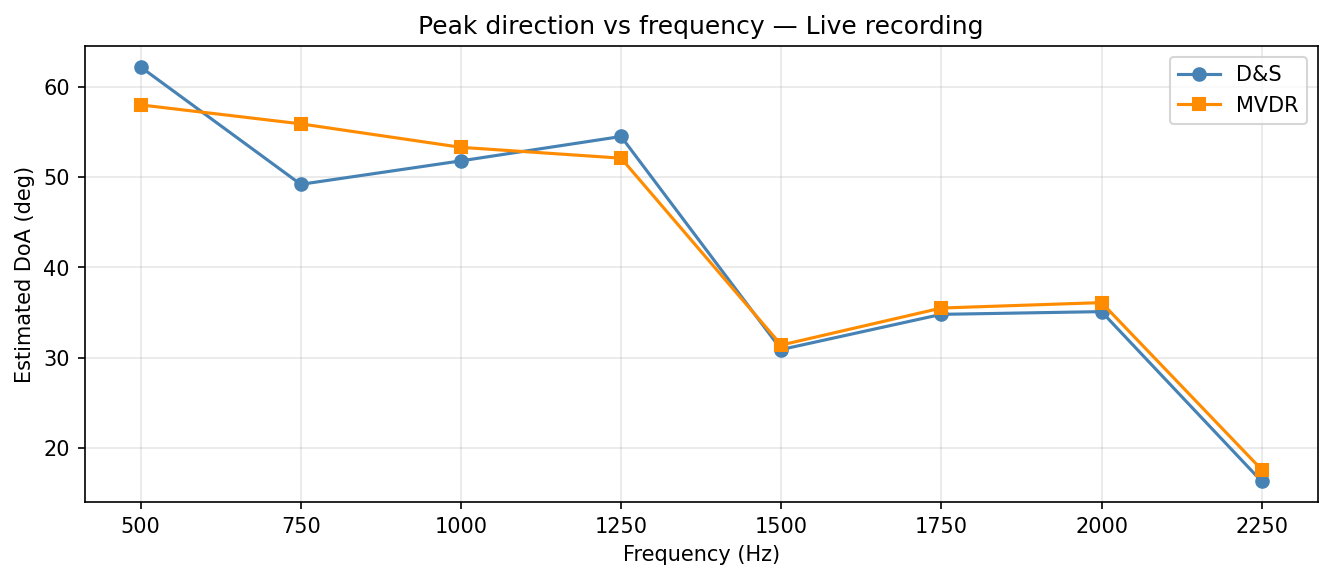
notebooks/respeaker_freq_sweep.png
