jduanen/Acoustic-Camera/notebooks/respeaker_geometry.png

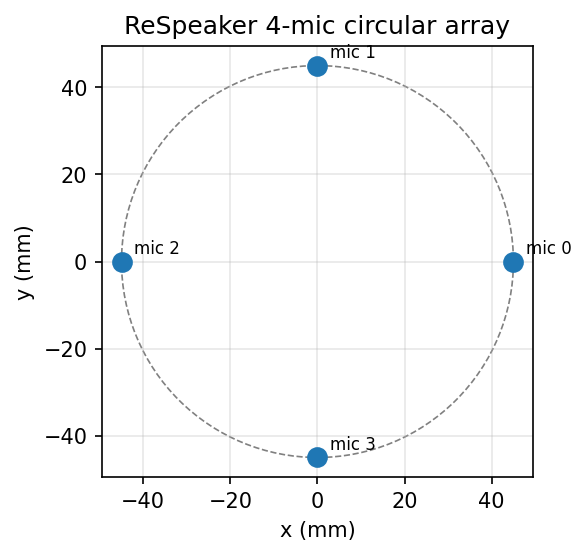
notebooks/respeaker_geometry.png
