jduanen/Acoustic-Camera/notebooks/respeaker_live_waveform.png

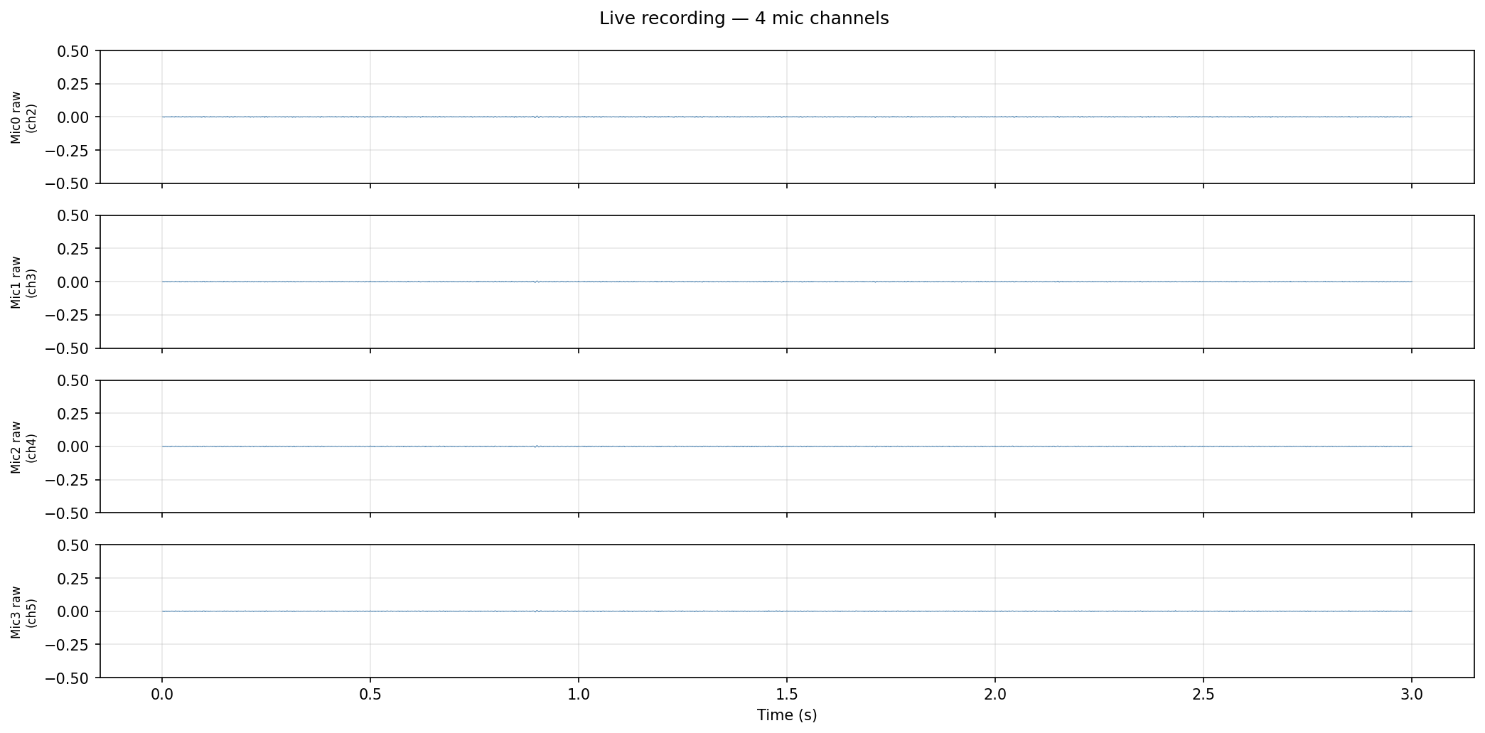
notebooks/respeaker_live_waveform.png
