jduanen/Acoustic-Camera/notebooks/respeaker_psf.png

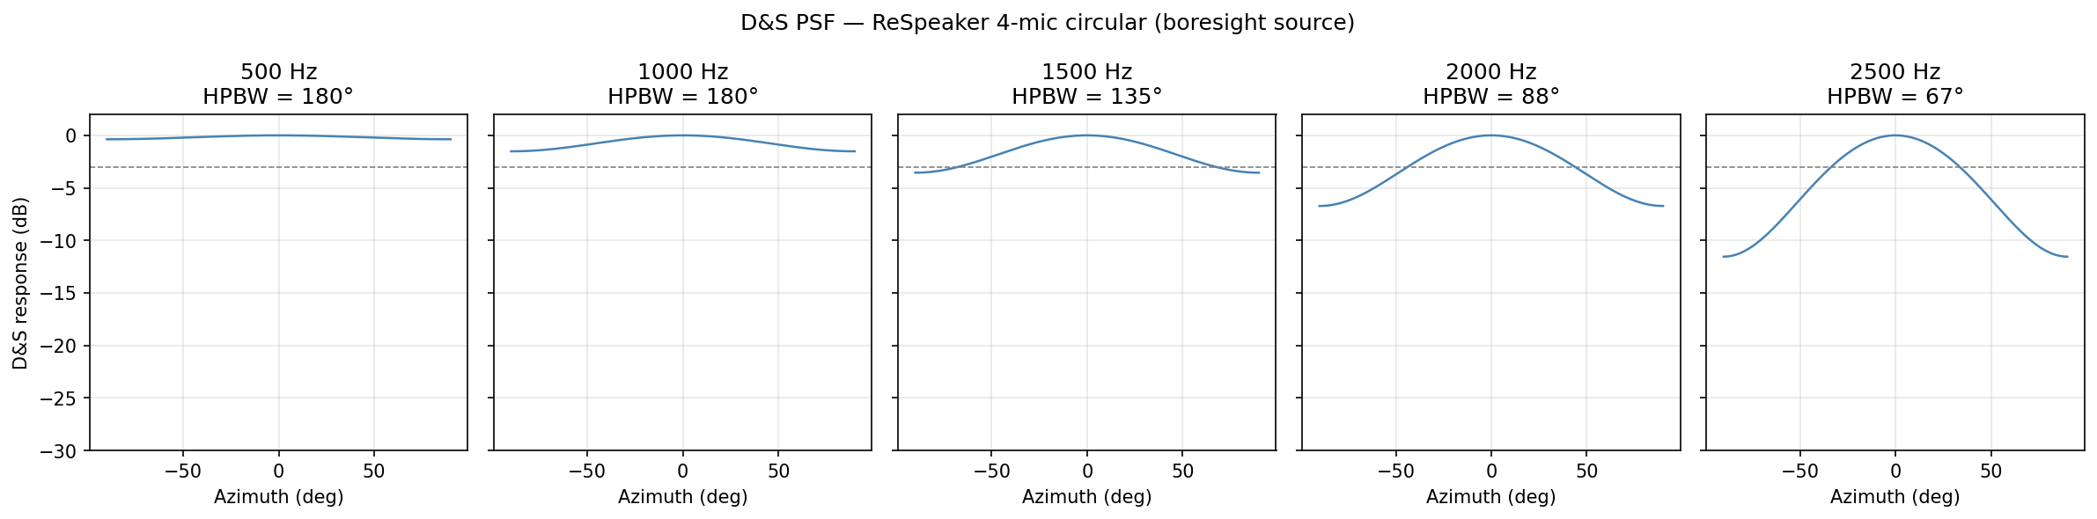
notebooks/respeaker_psf.png
