jduanen/Acoustic-Camera/notebooks/respeaker_snap_sweep.png

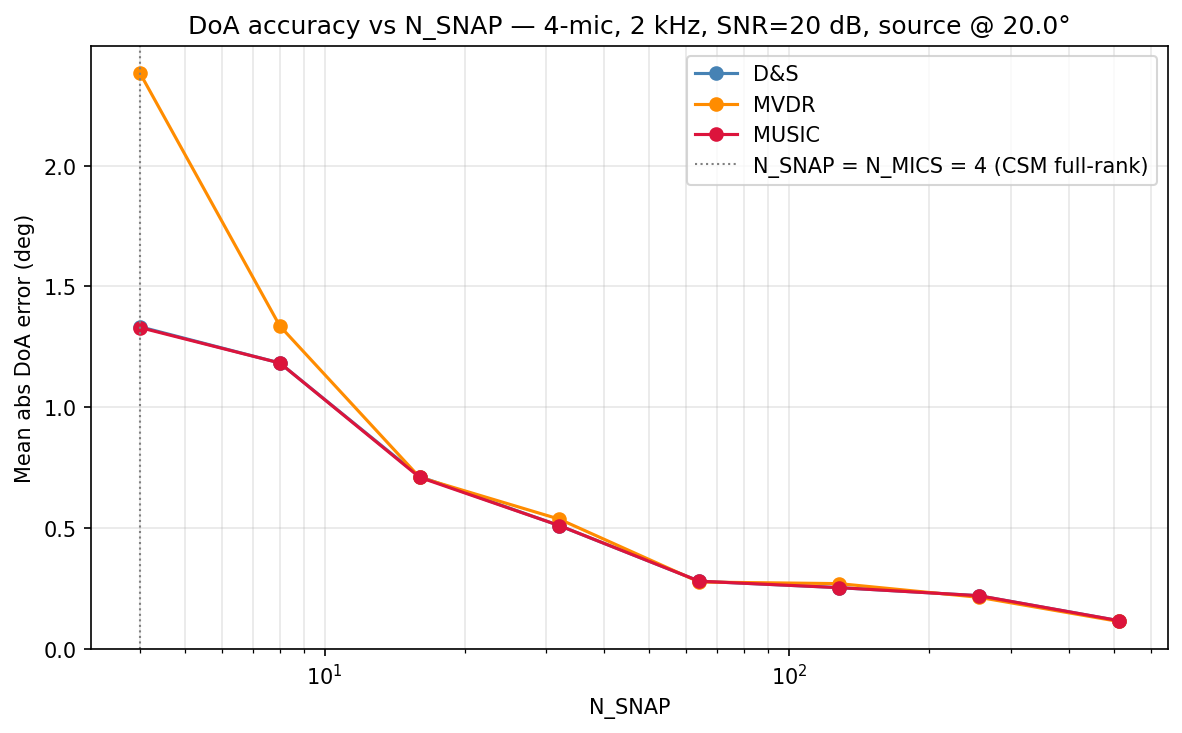
notebooks/respeaker_snap_sweep.png
