jduanen/Acoustic-Camera/notebooks/respeaker_snr_sweep.png

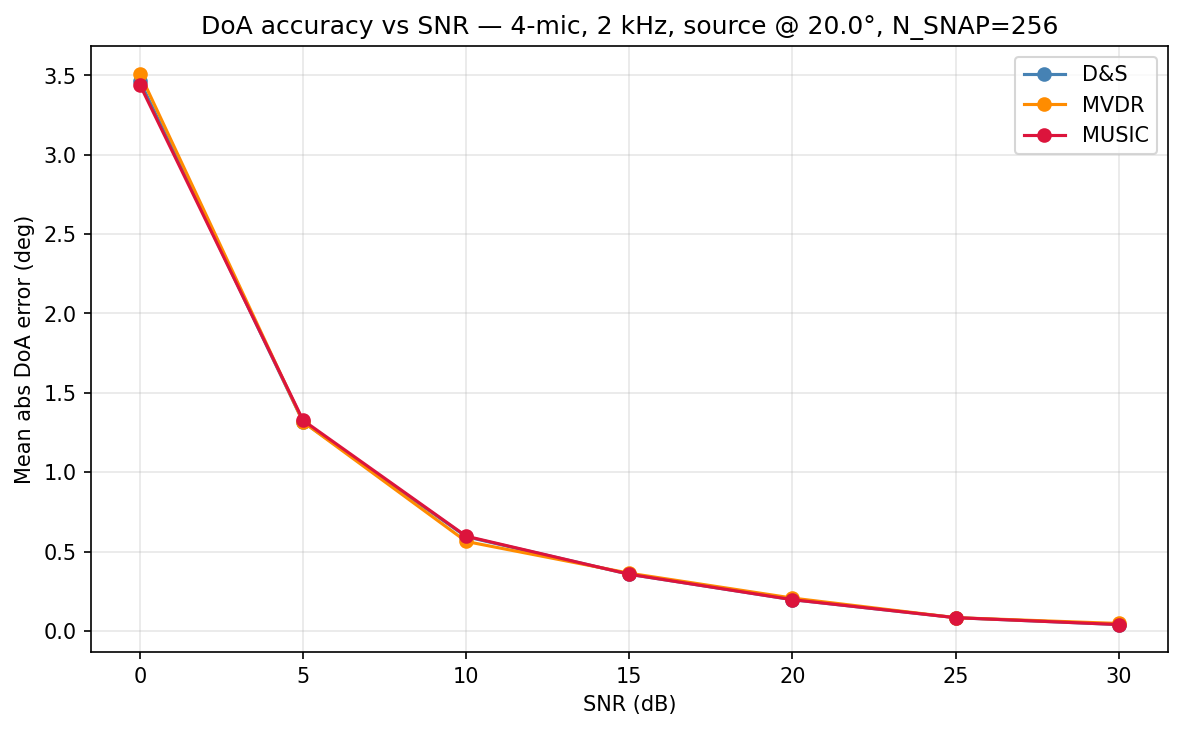
notebooks/respeaker_snr_sweep.png
