jduanen/Acoustic-Camera/notebooks/respeaker_xcorr.png

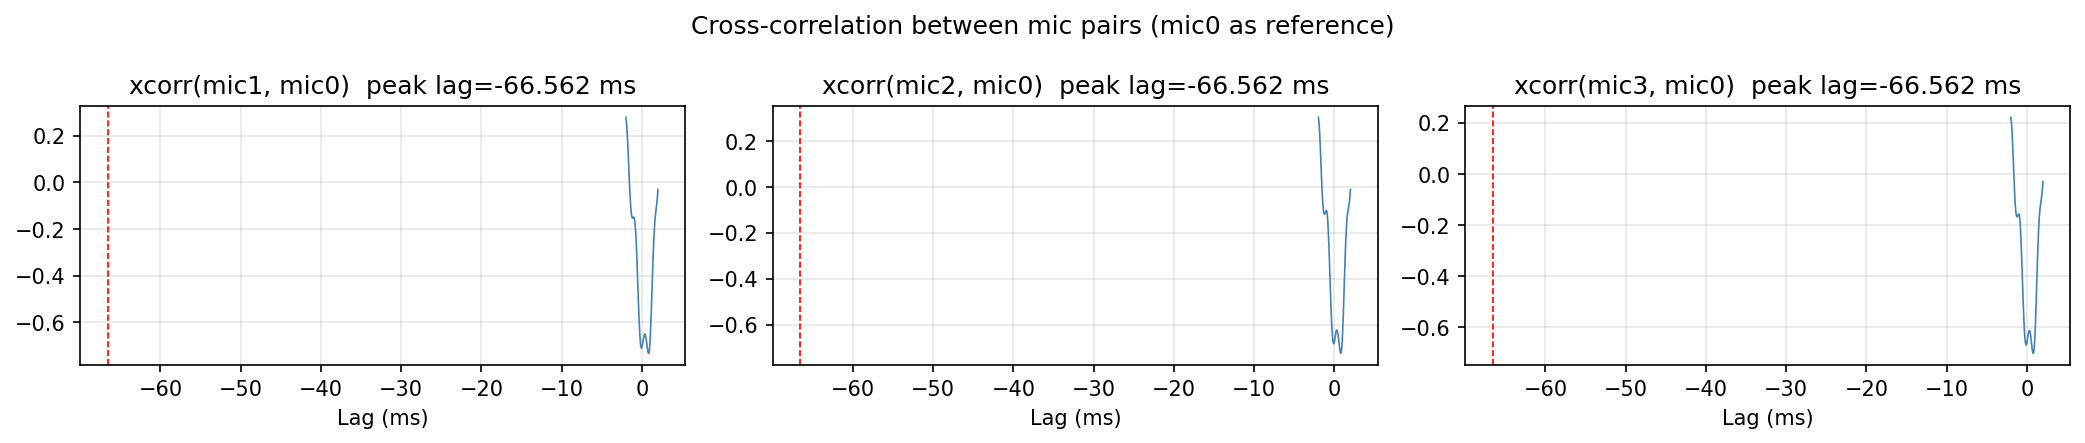
notebooks/respeaker_xcorr.png
