jduanen/Acoustic-Camera/notebooks/reverb_coherent_ghost.png

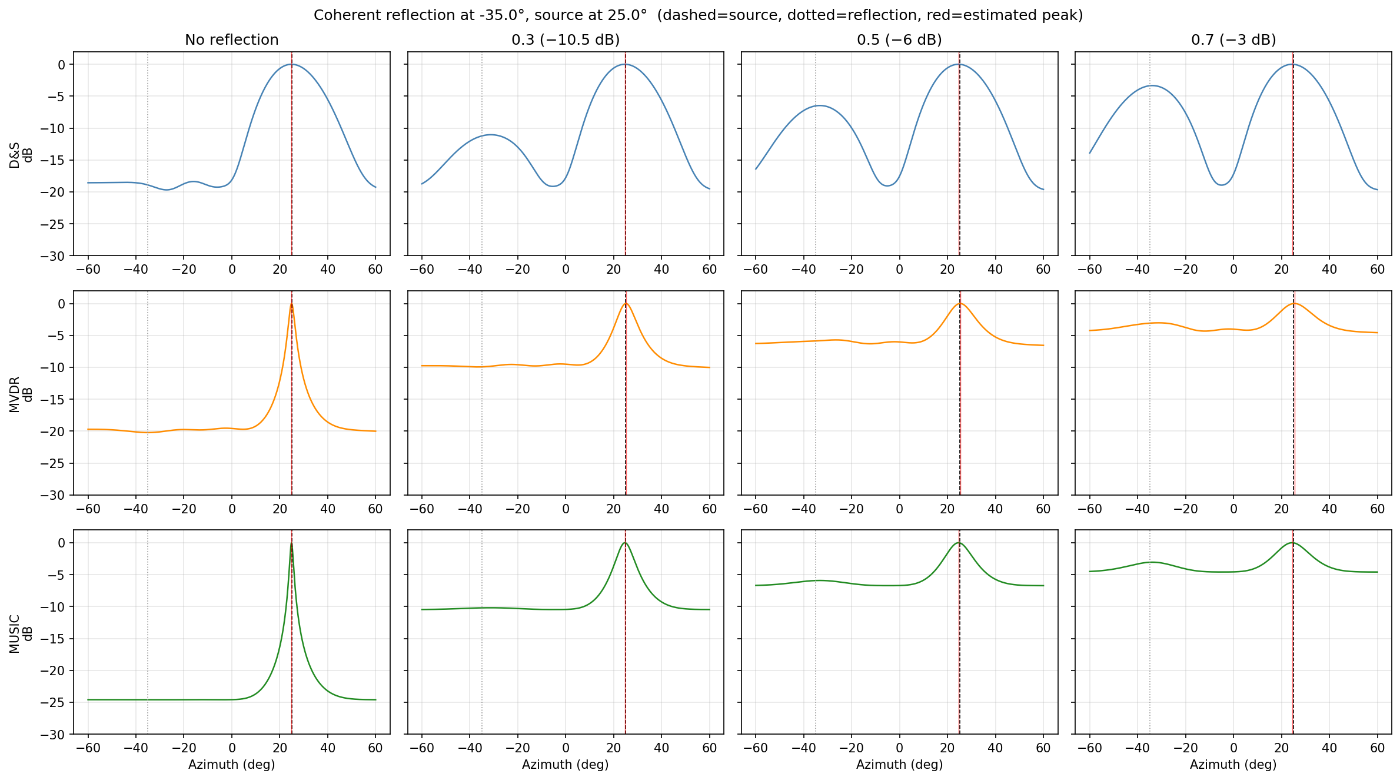
notebooks/reverb_coherent_ghost.png
