jduanen/Acoustic-Camera/notebooks/reverb_doa_vs_drr.png

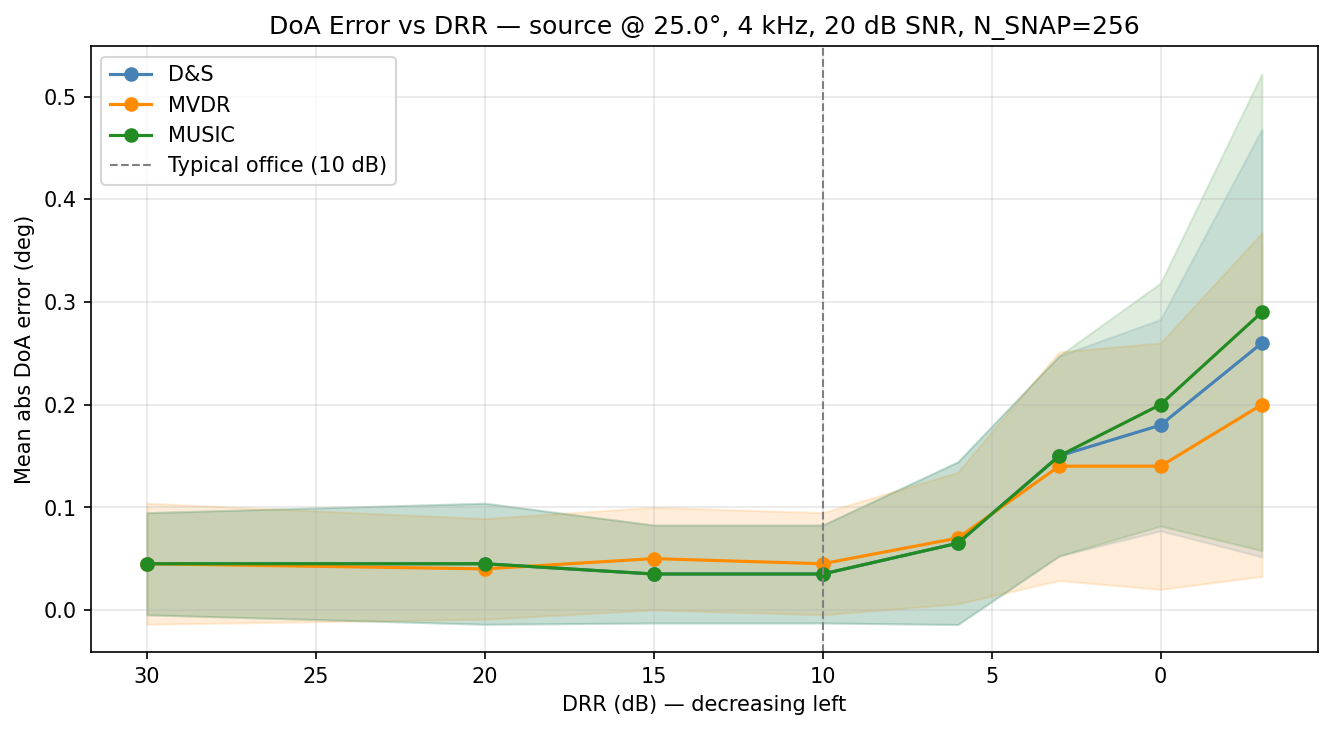
notebooks/reverb_doa_vs_drr.png
