jduanen/Acoustic-Camera/notebooks/reverb_resolution.png

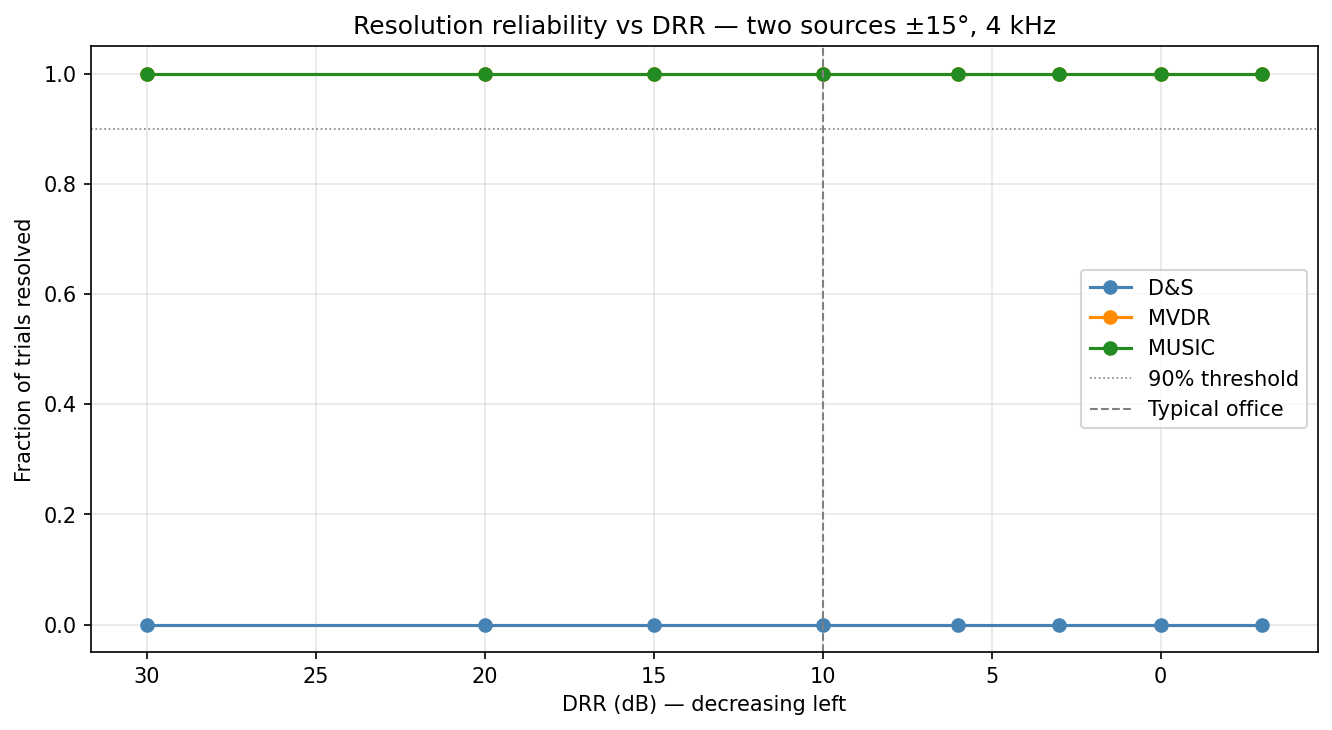
notebooks/reverb_resolution.png
