jduanen/Acoustic-Camera/notebooks/snap_doa_error.png

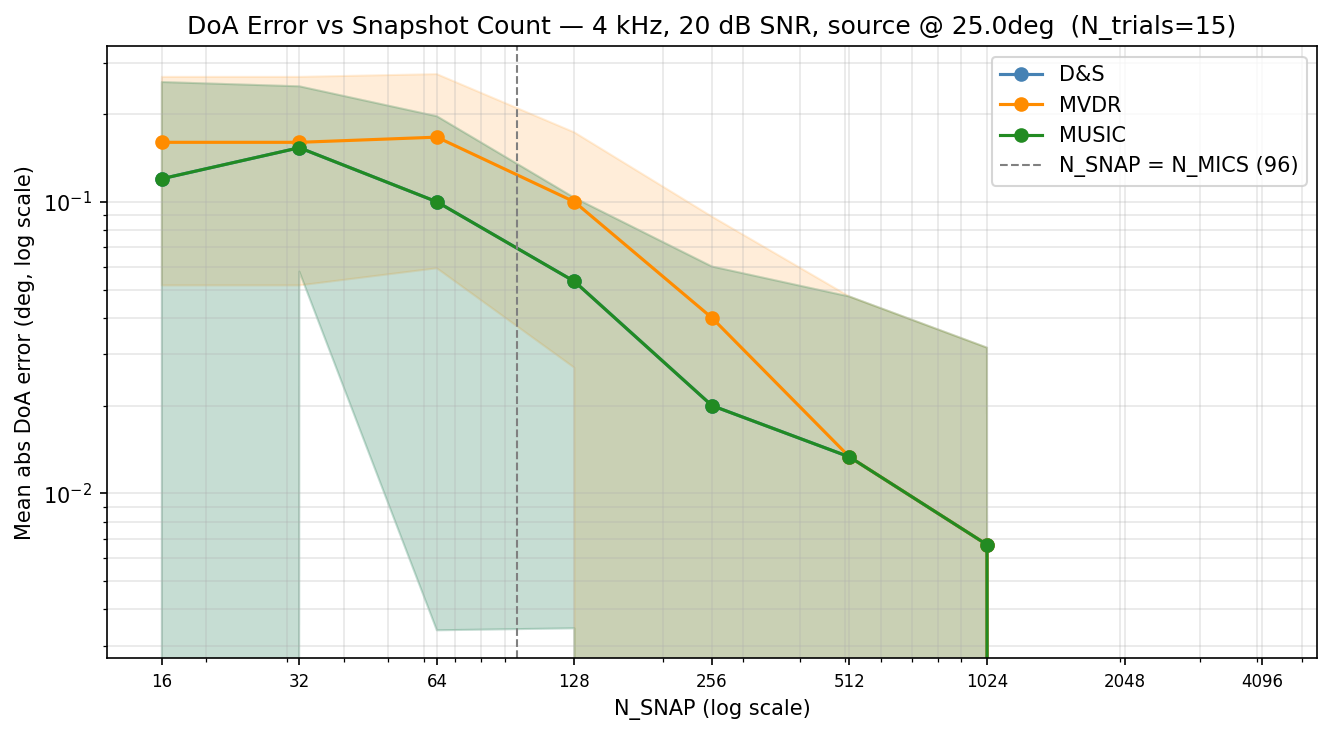
notebooks/snap_doa_error.png
