jduanen/Acoustic-Camera/notebooks/snap_resolution.png

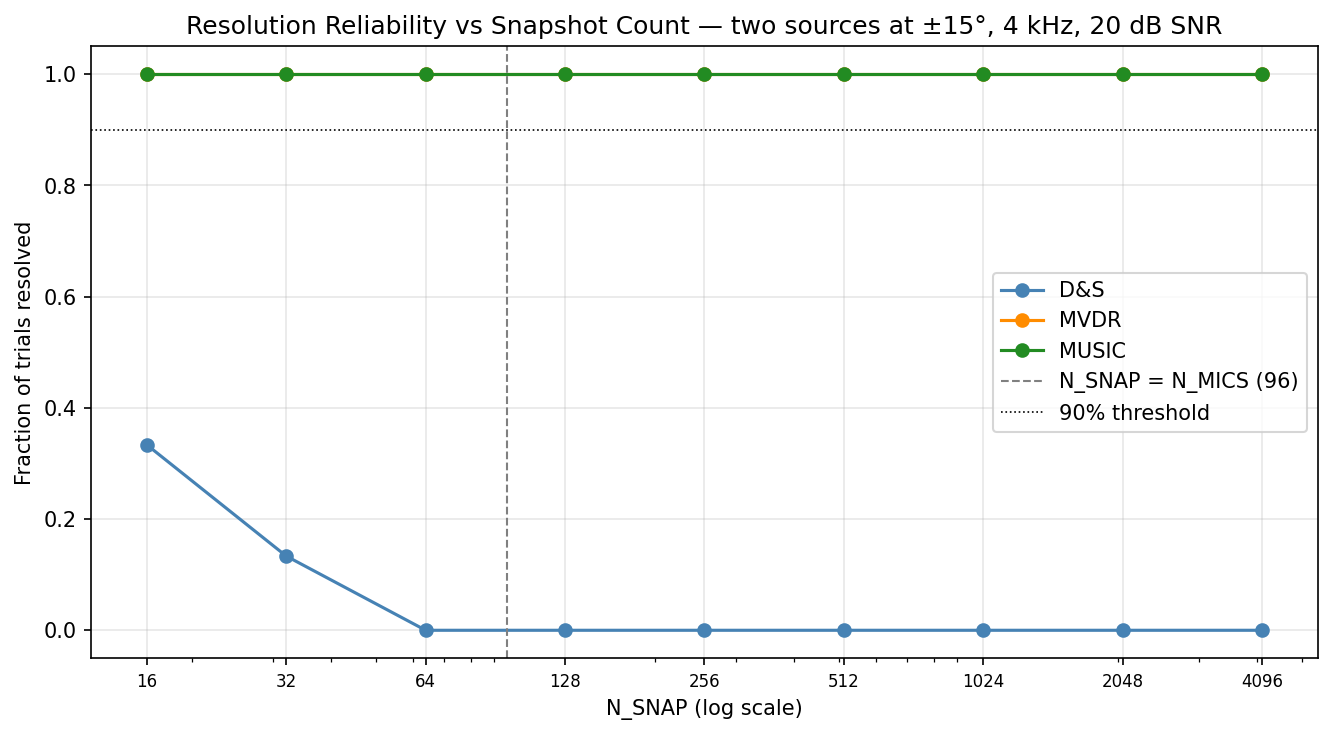
notebooks/snap_resolution.png
