jduanen/Acoustic-Camera/notebooks/snap_snr_comparison.png

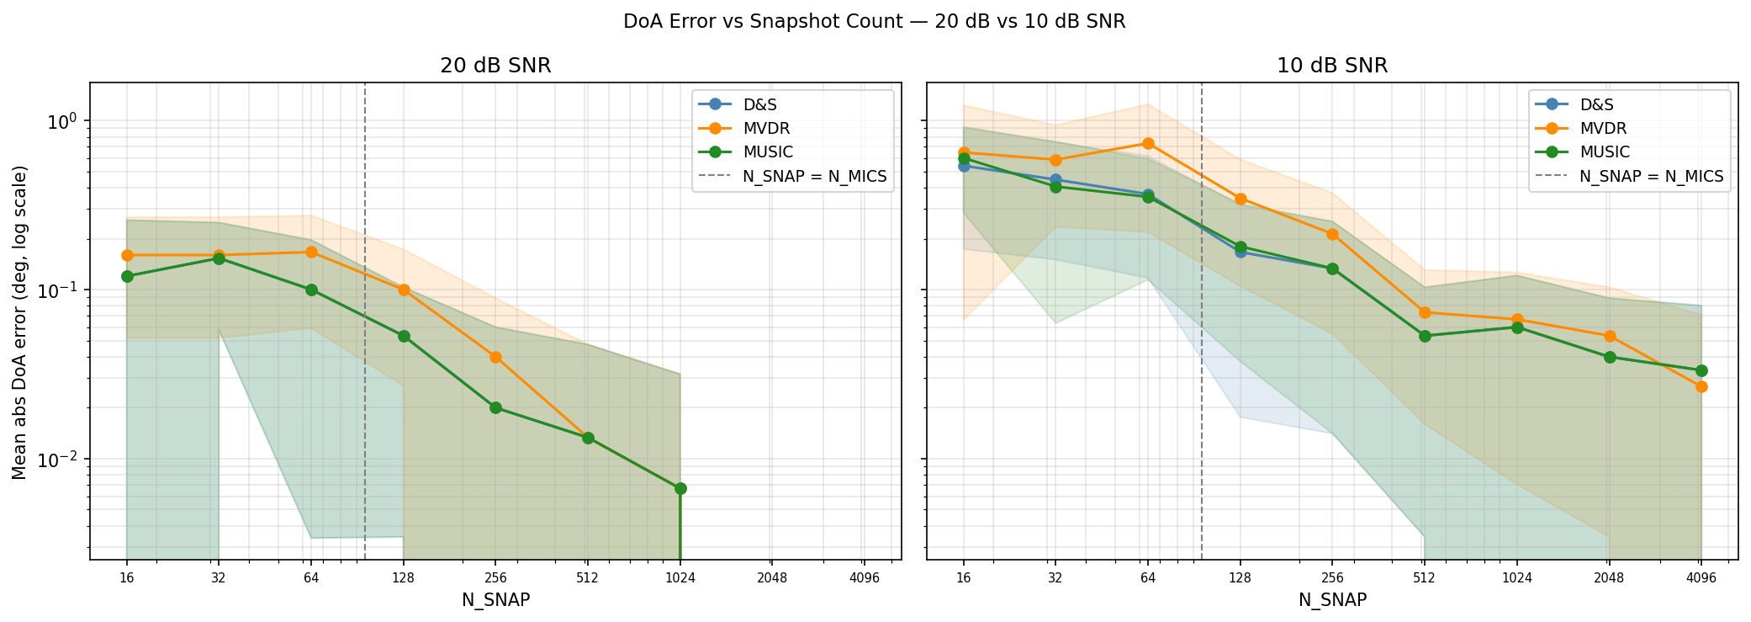
notebooks/snap_snr_comparison.png
