jduanen/Acoustic-Camera/notebooks/uma16_algo_comparison.png

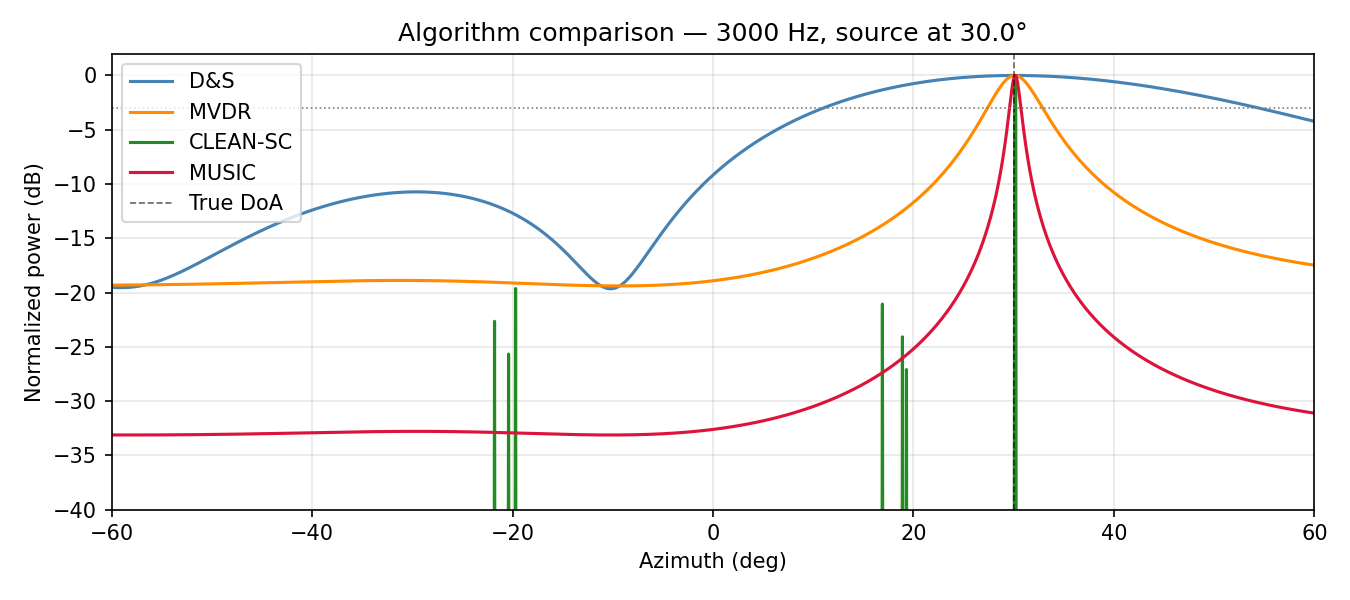
notebooks/uma16_algo_comparison.png
