jduanen/Acoustic-Camera/notebooks/uma16_beamform_1d.png

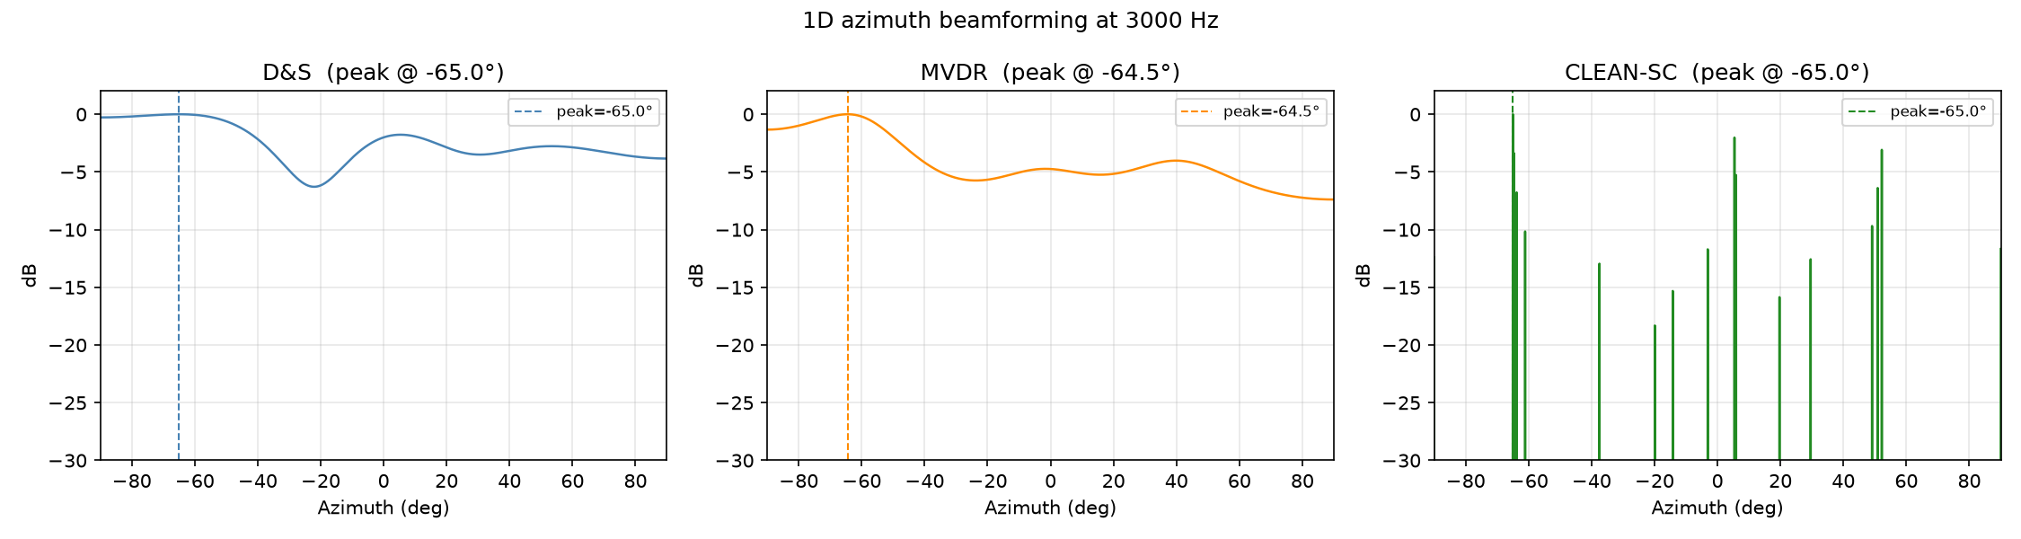
notebooks/uma16_beamform_1d.png
