jduanen/Acoustic-Camera/notebooks/uma16_beamform_2d.png

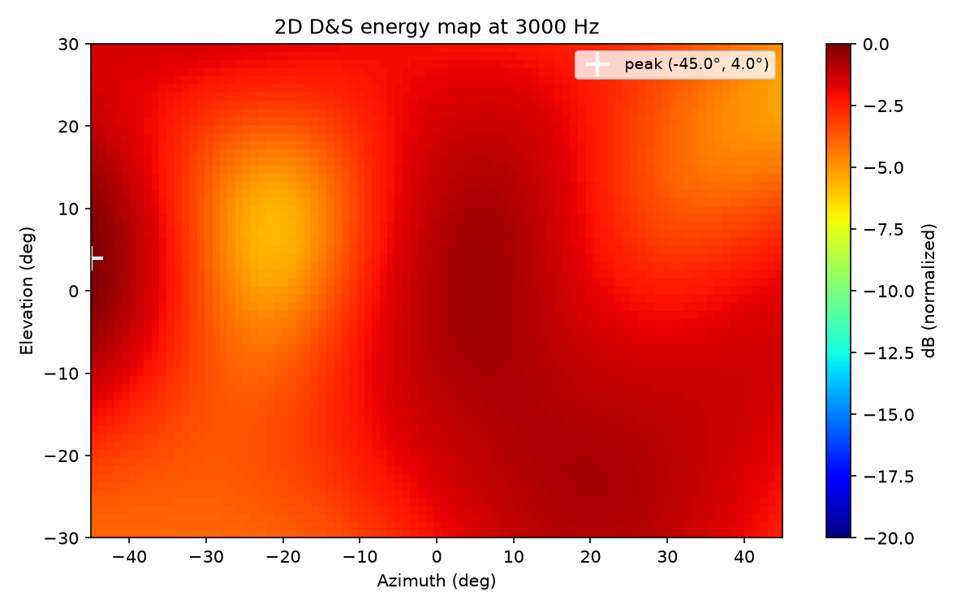
notebooks/uma16_beamform_2d.png
