jduanen/Acoustic-Camera/notebooks/uma16_cal_csm.png

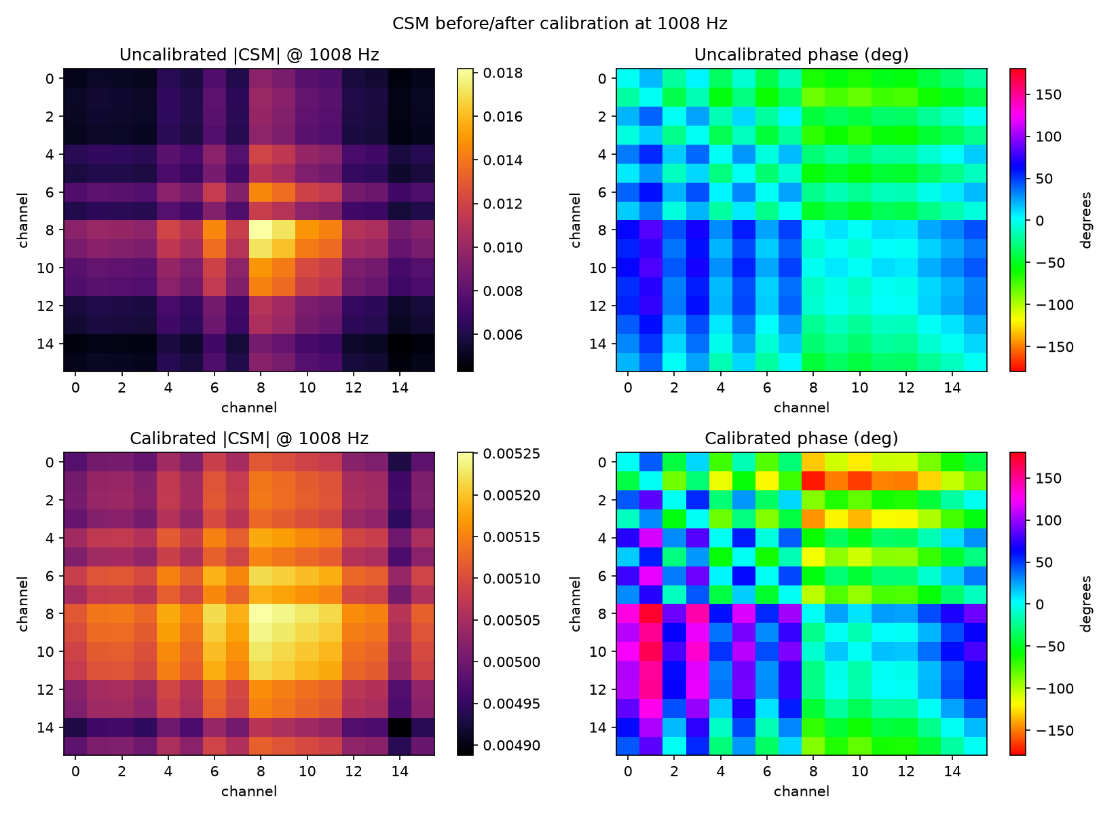
notebooks/uma16_cal_csm.png
