jduanen/Acoustic-Camera/notebooks/uma16_cal_doa.png

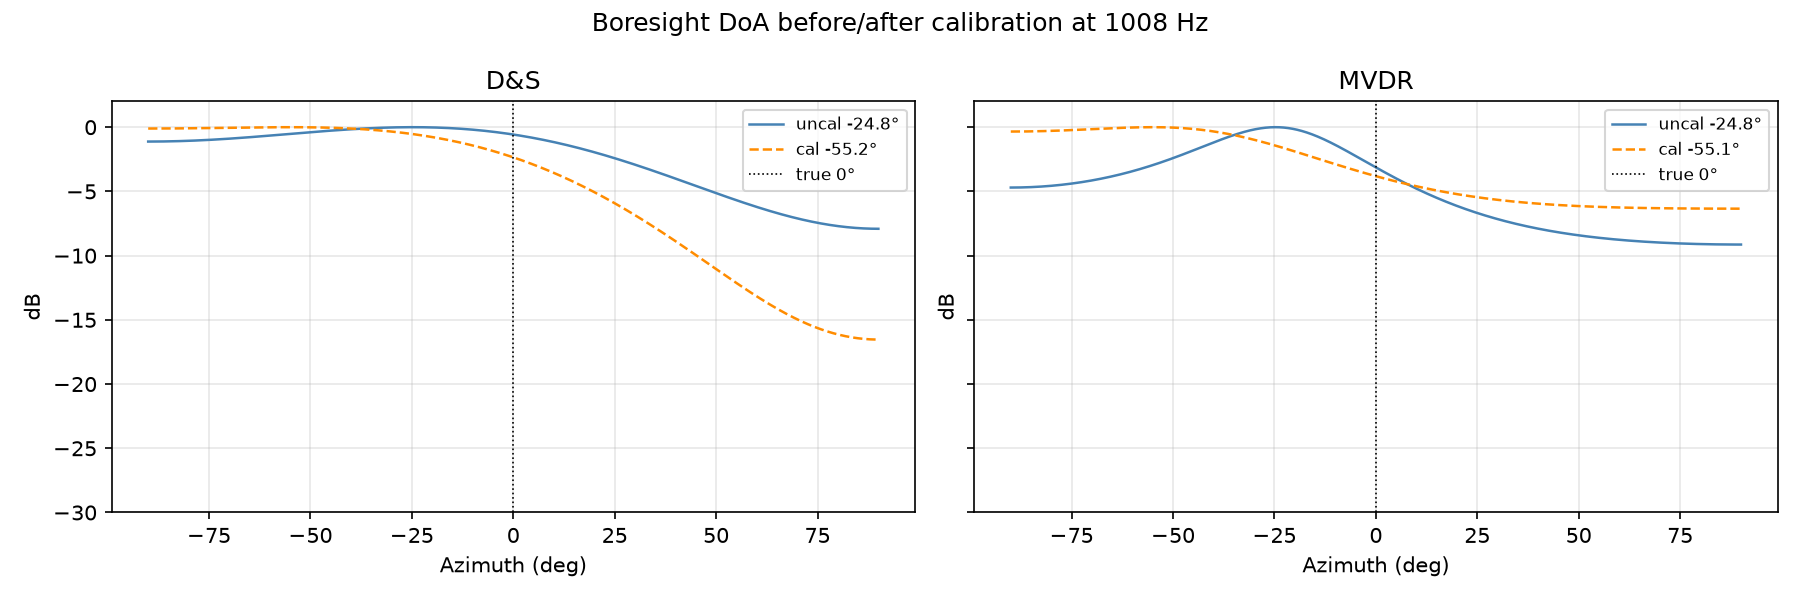
notebooks/uma16_cal_doa.png
