jduanen/Acoustic-Camera/notebooks/uma16_capture_waveforms.png

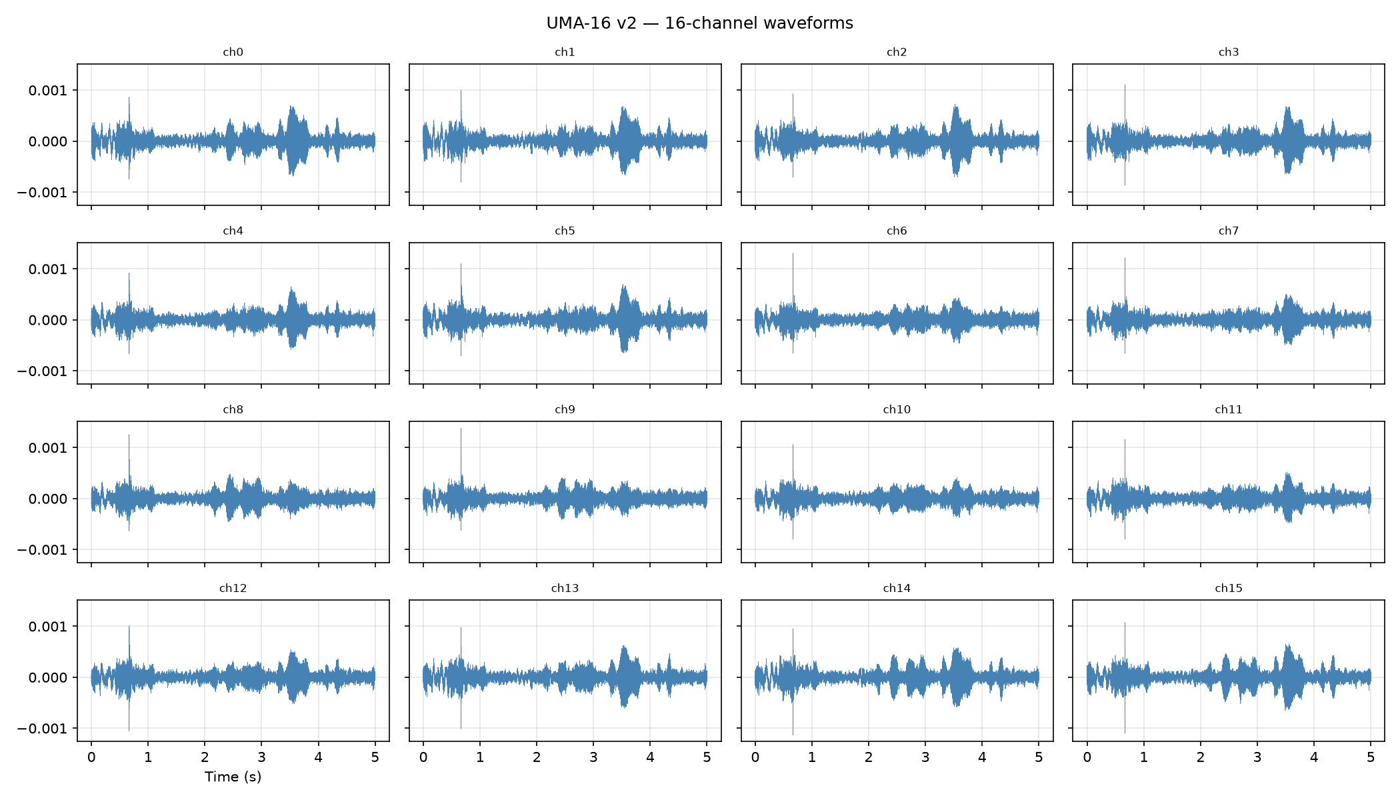
notebooks/uma16_capture_waveforms.png
