jduanen/Acoustic-Camera/notebooks/uma16_csm.png

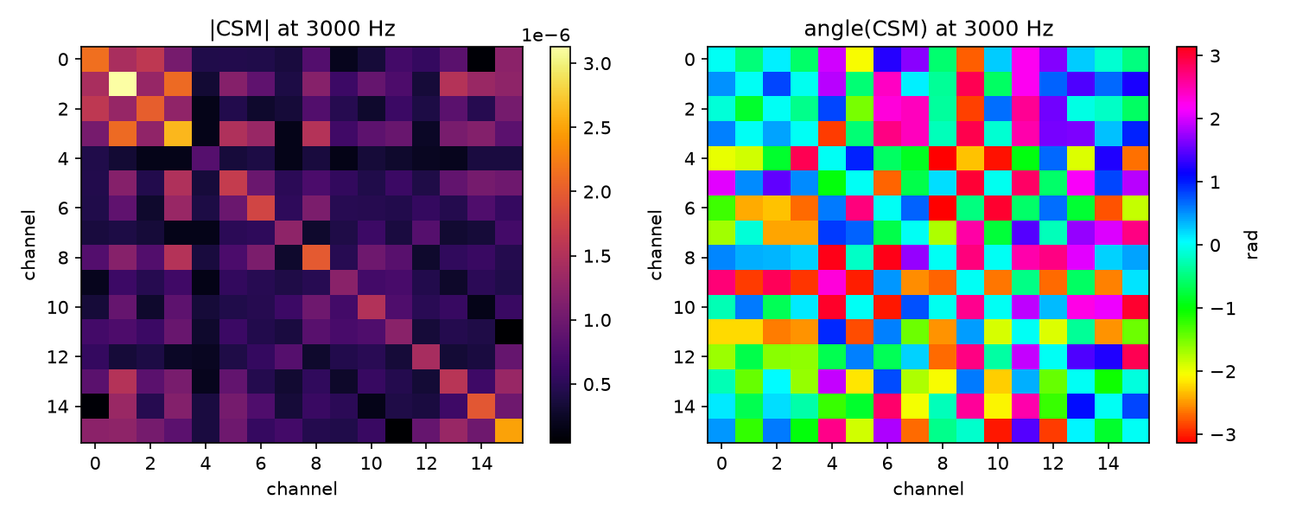
notebooks/uma16_csm.png
