jduanen/Acoustic-Camera/notebooks/uma16_freq_response.png

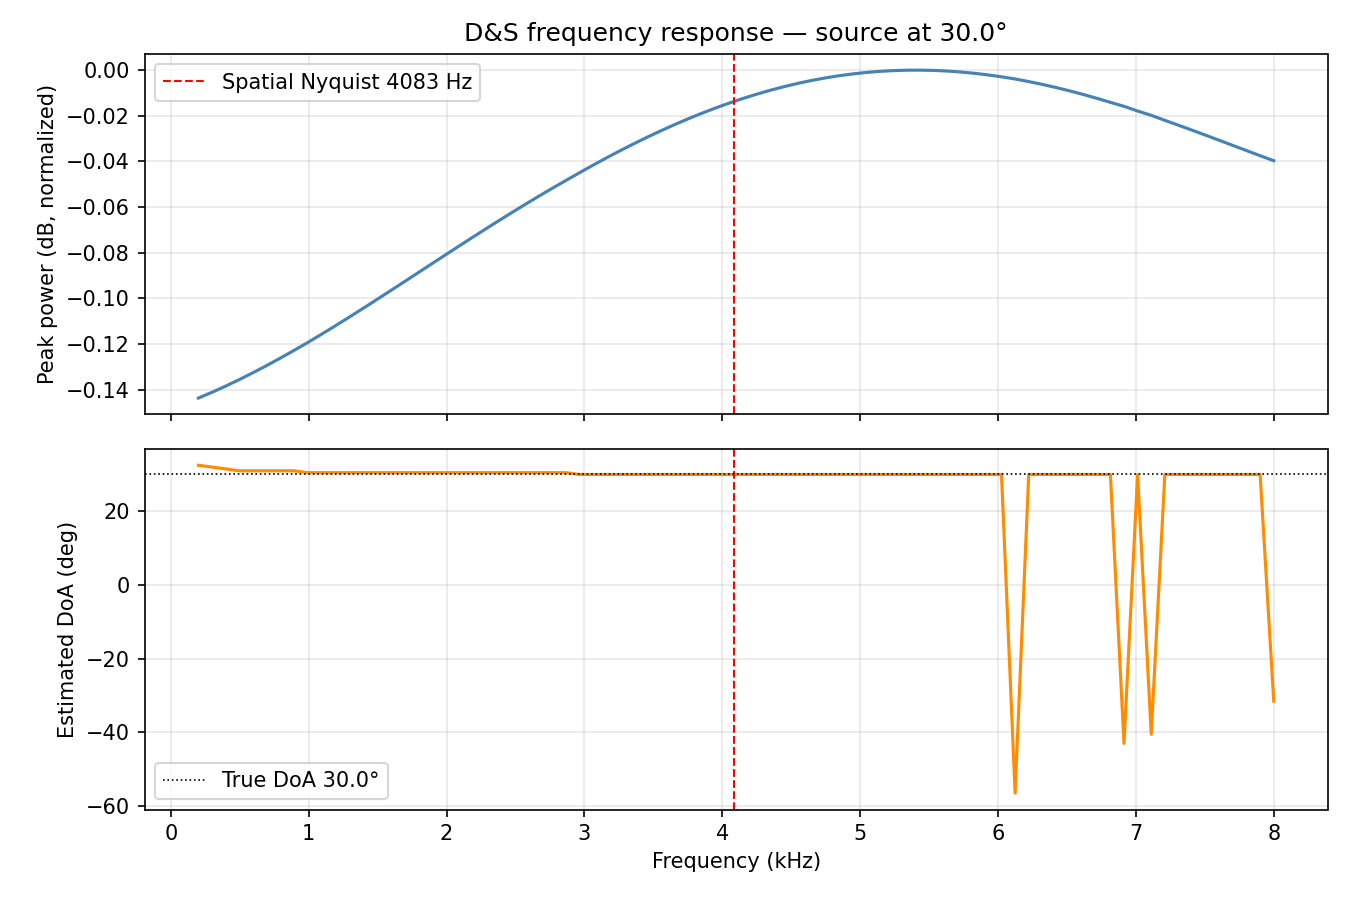
notebooks/uma16_freq_response.png
