jduanen/Acoustic-Camera/notebooks/uma16_freq_sweep.png

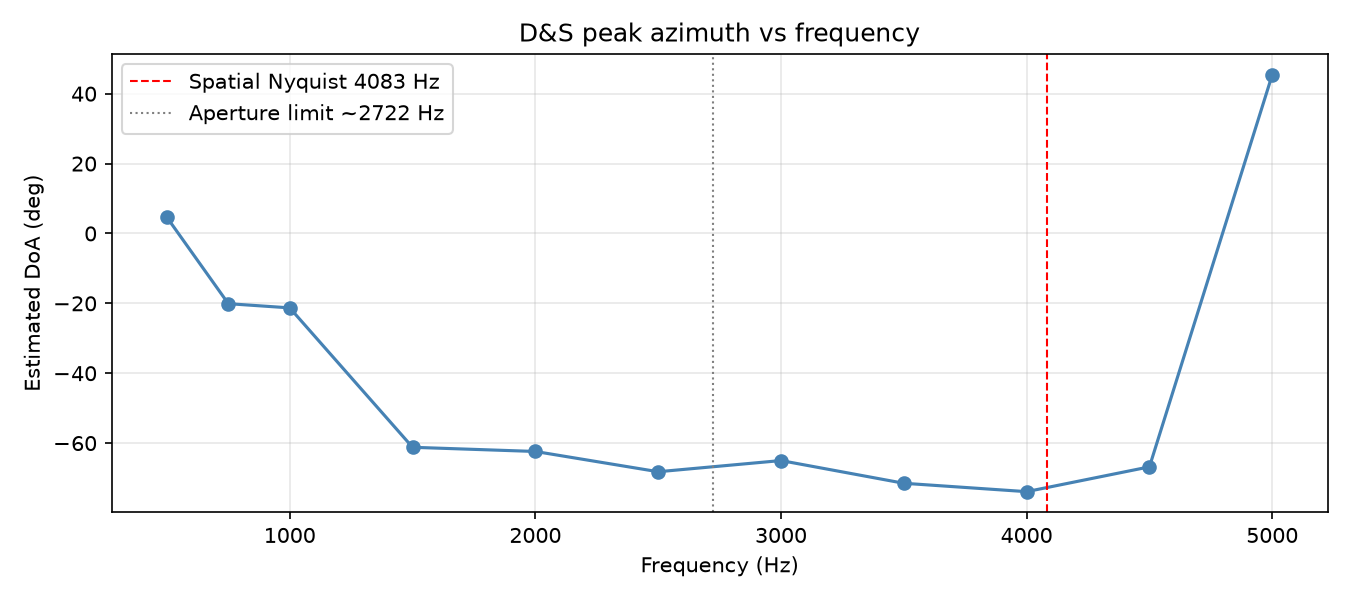
notebooks/uma16_freq_sweep.png
