jduanen/Acoustic-Camera/notebooks/uma16_geometry.png

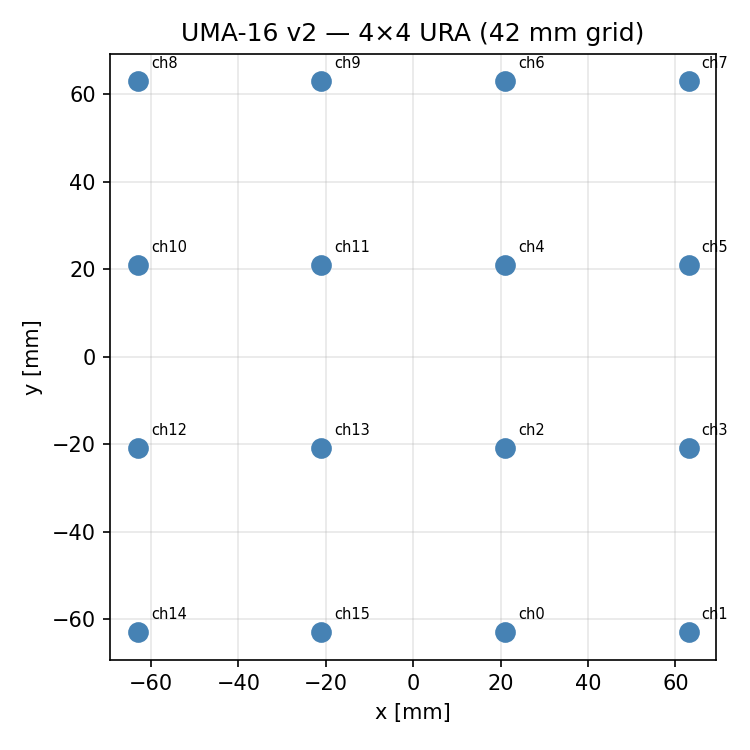
notebooks/uma16_geometry.png
