jduanen/Acoustic-Camera/notebooks/uma16_phase_comparison.png

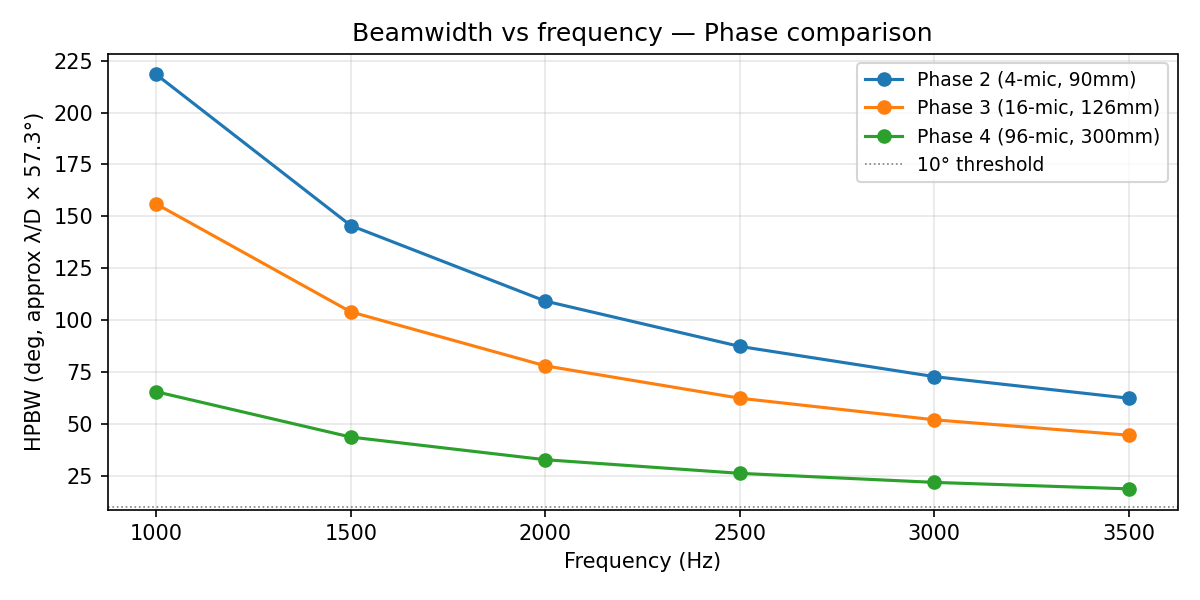
notebooks/uma16_phase_comparison.png
