jduanen/Acoustic-Camera/notebooks/uma16_psf.png

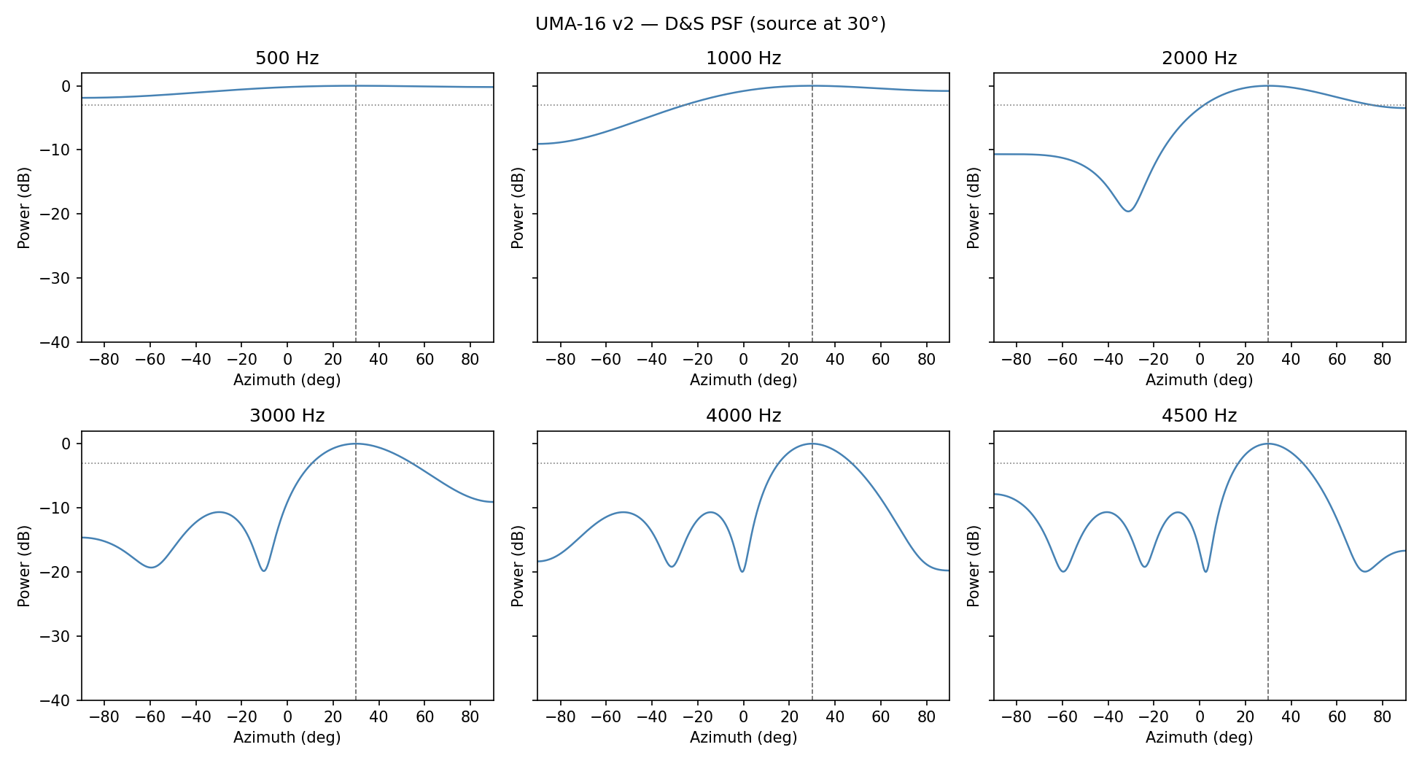
notebooks/uma16_psf.png
