jduanen/Acoustic-Camera/notebooks/uma16_psf_2d.png

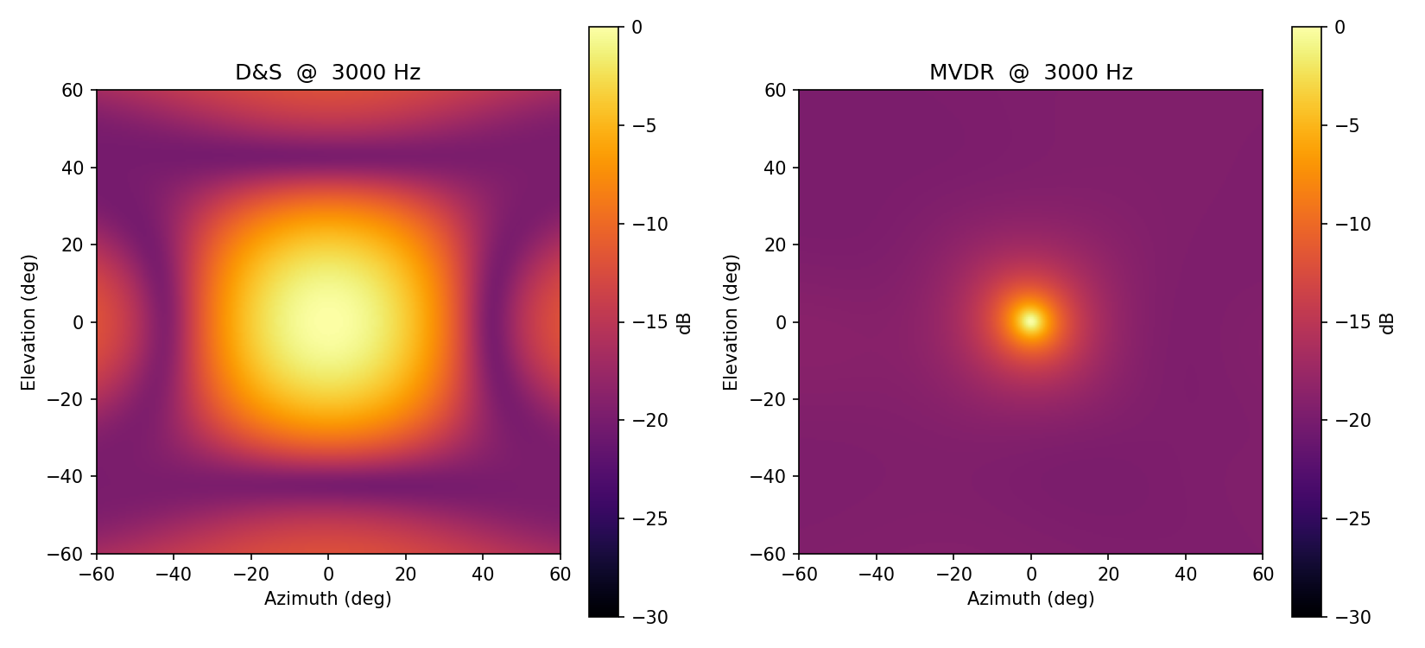
notebooks/uma16_psf_2d.png
