jduanen/Acoustic-Camera/notebooks/uma16_snap_convergence.png

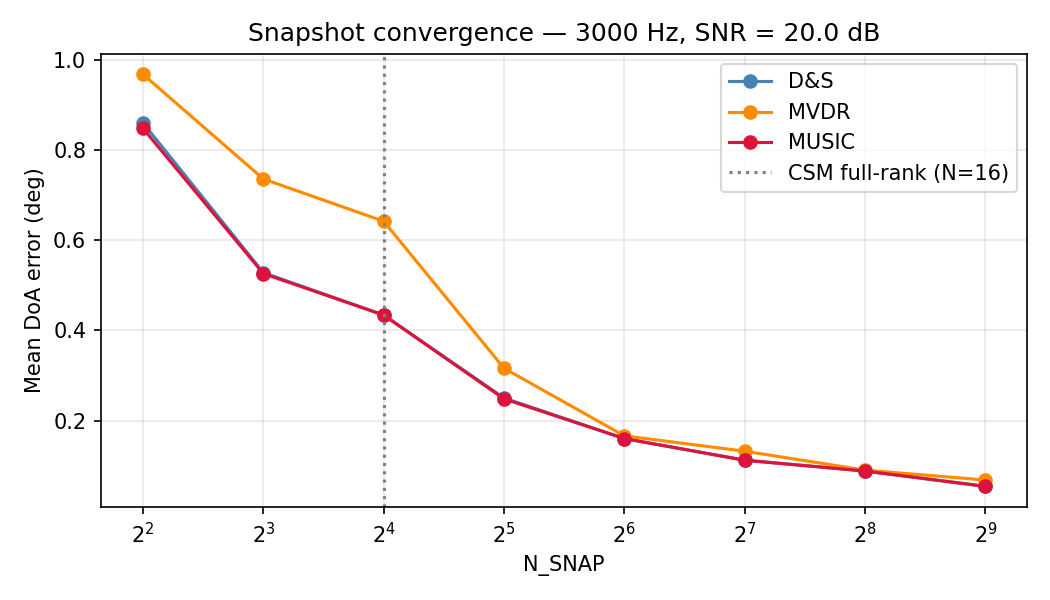
notebooks/uma16_snap_convergence.png
