jduanen/Acoustic-Camera/notebooks/uma16_two_source.png

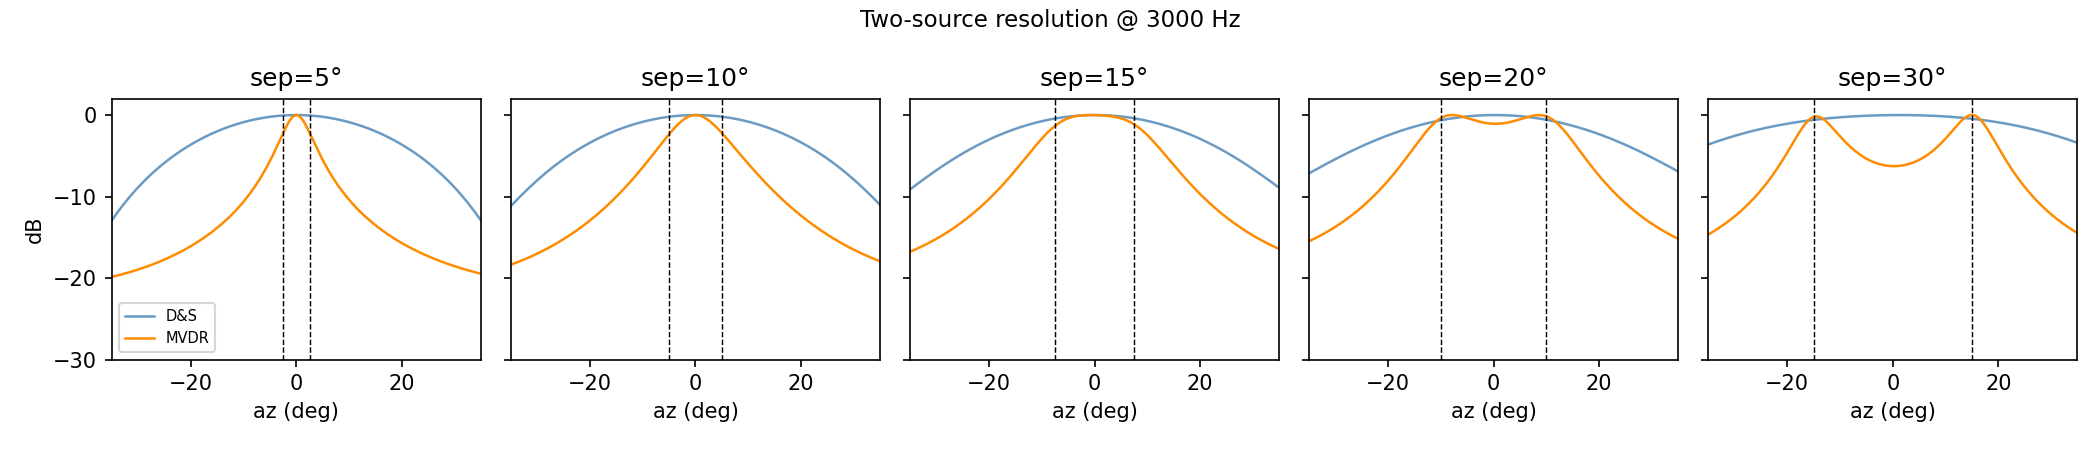
notebooks/uma16_two_source.png
