jduanen/Acoustic-Camera/notebooks/underbrink_angle_sweep.png

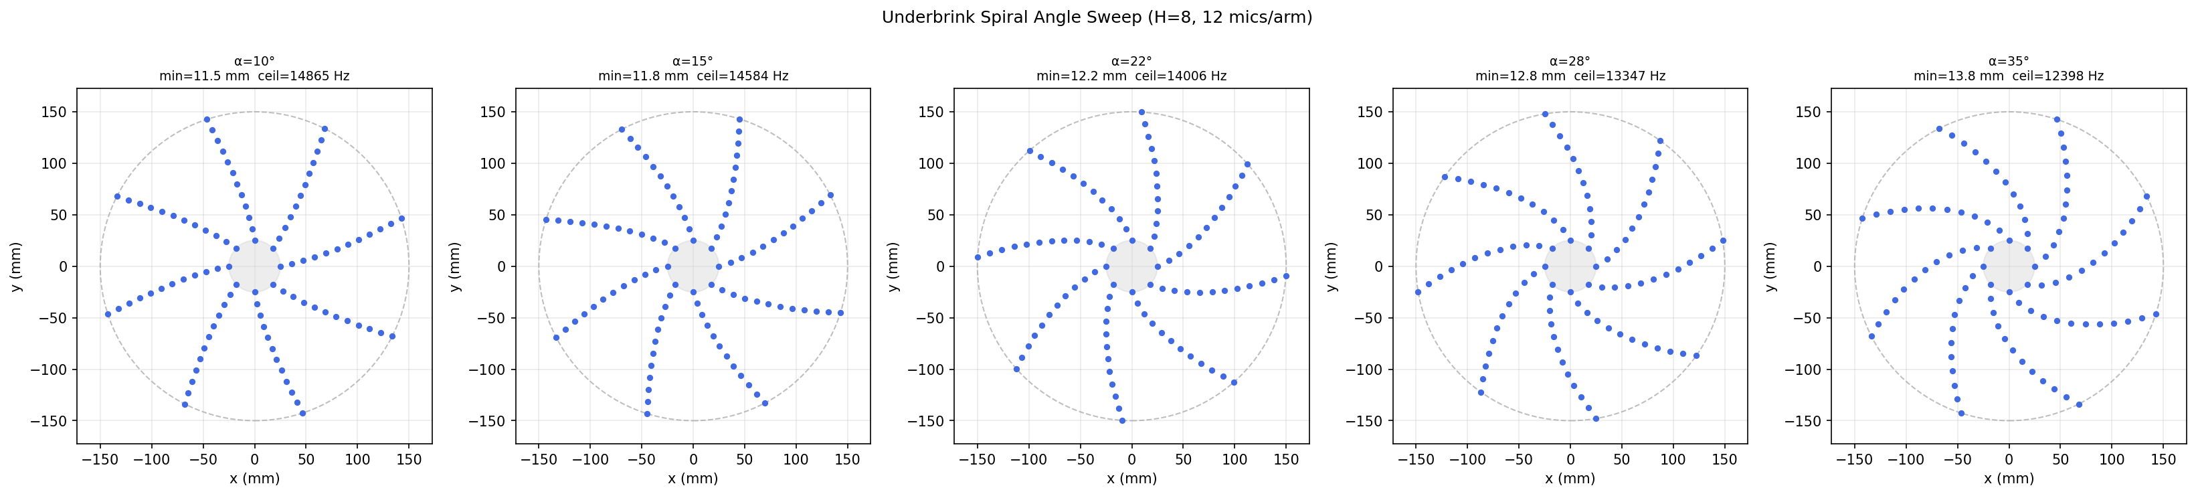
notebooks/underbrink_angle_sweep.png
