jduanen/Acoustic-Camera/notebooks/underbrink_angle_vs_spacing.png

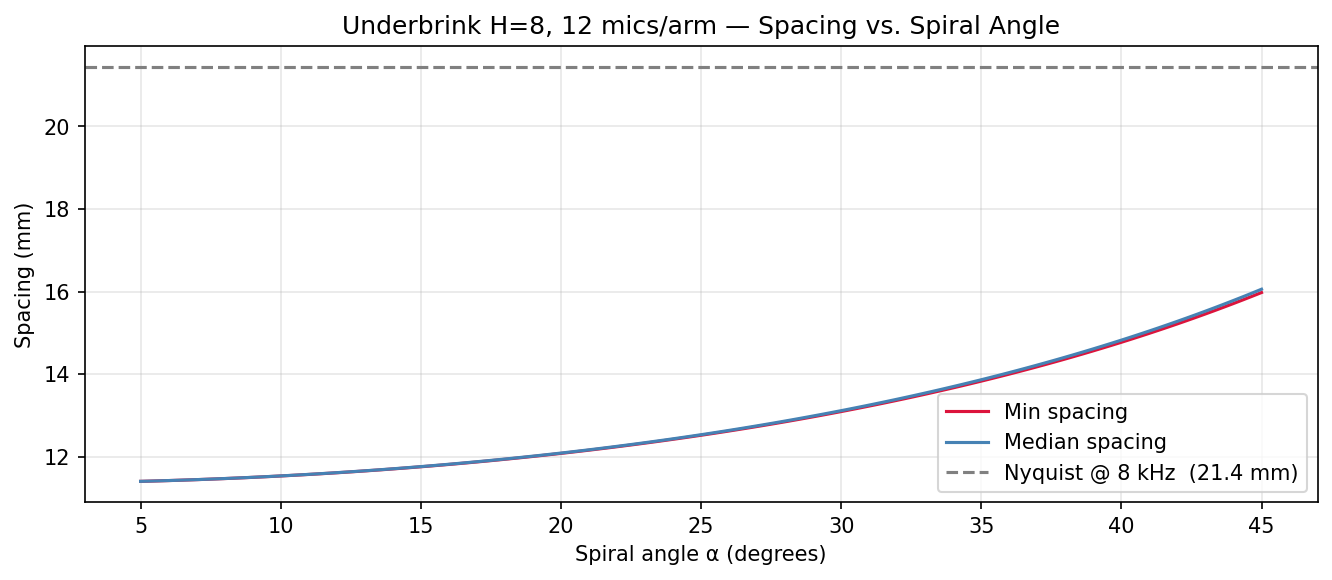
notebooks/underbrink_angle_vs_spacing.png
