jduanen/Acoustic-Camera/notebooks/underbrink_arms_sweep.png

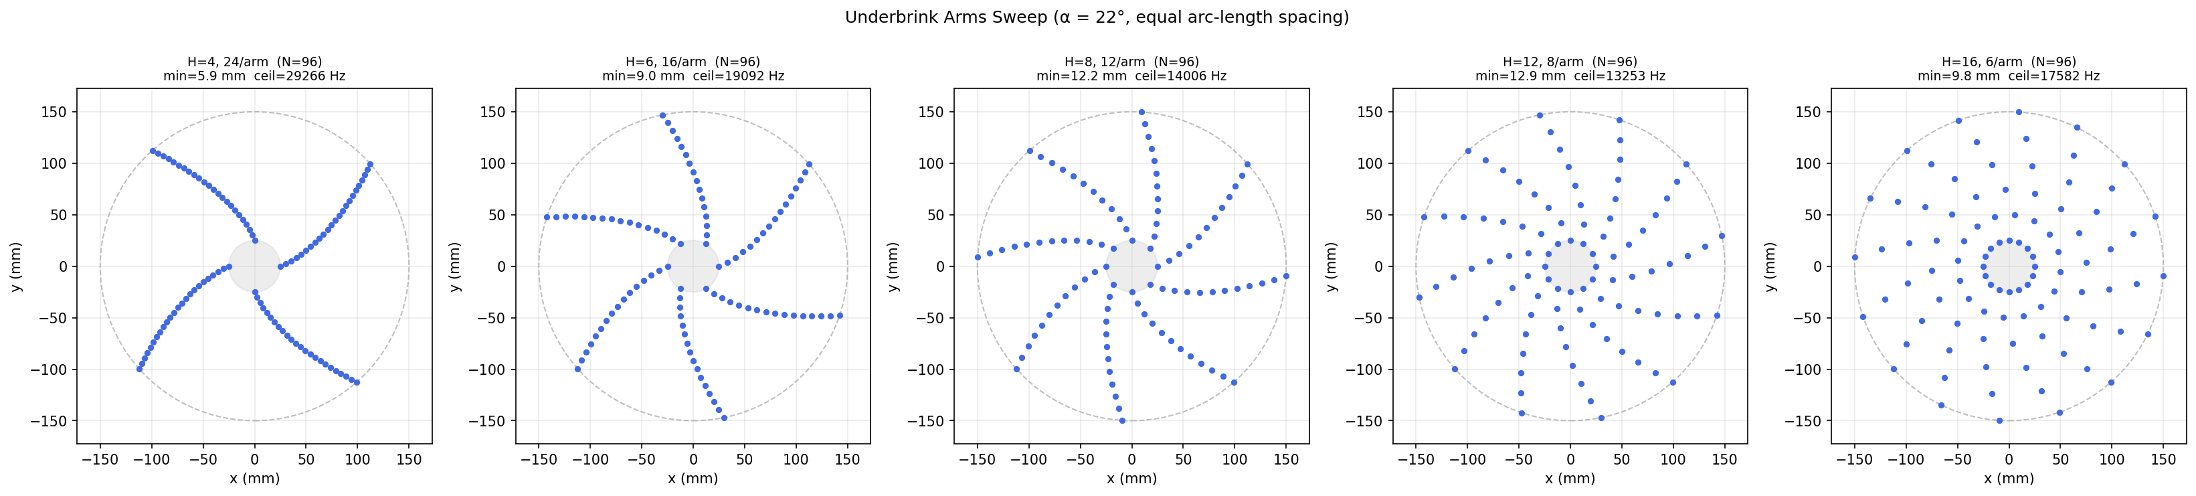
notebooks/underbrink_arms_sweep.png
