jduanen/Acoustic-Camera/notebooks/underbrink_grid_search.png

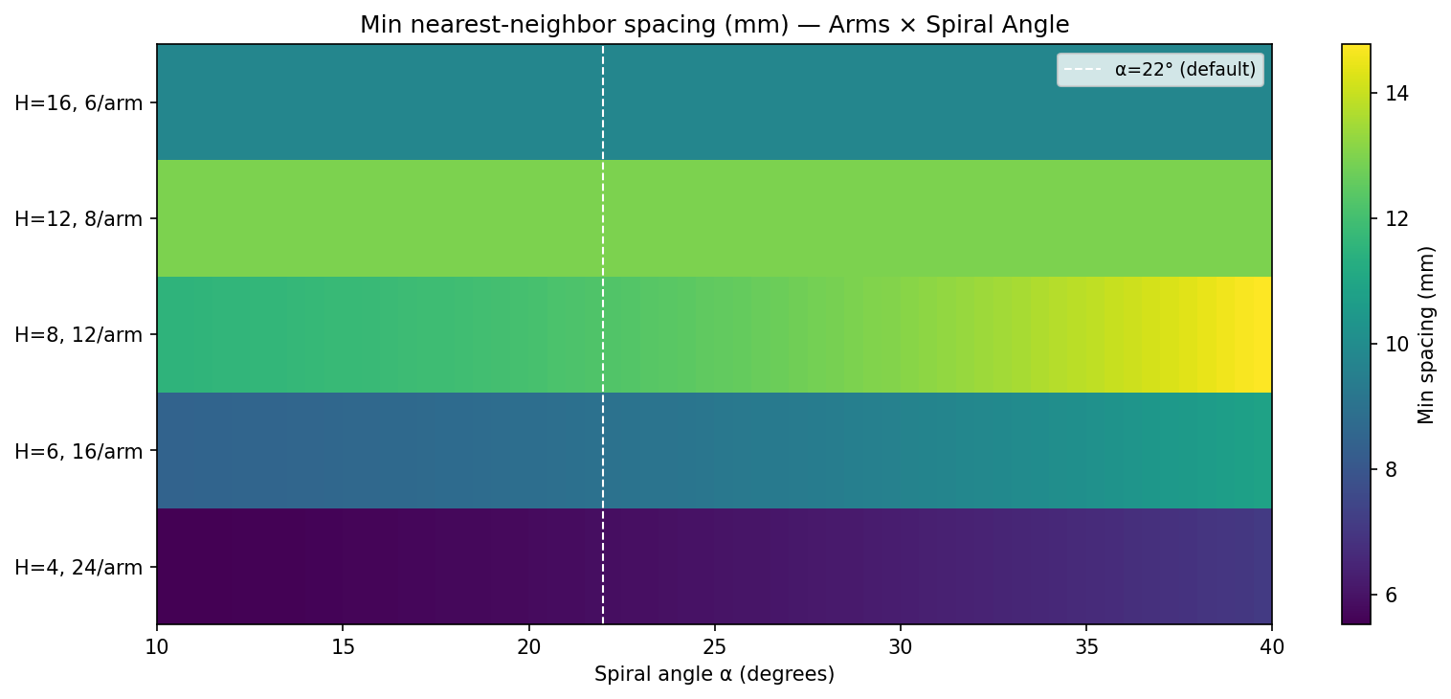
notebooks/underbrink_grid_search.png
