jduanen/Acoustic-Camera/pcb/multi_fpga/tools/layout_multi_fpga.py

#!/usr/bin/env python3
"""
DEPRECATED (2026-08-23): the user now manages pcb/multi_fpga/'s schematics
and PCBs directly in KiCad. Do NOT run this script to (re)generate or
overwrite any .kicad_pcb file -- it will conflict with, and can destroy,
hand-placed/hand-routed state (this has already happened once this
project). Kept in the repo for historical/documentation reference only.

layout_multi_fpga.py -- board outline + footprint placement for the Phase 4
Multi-FPGA (Clustered) alternative: ONE arm board design (Cmod A7-35T + 24
mics + their decoupling caps) and 1 hub board (Cmod A7-35T + FT232H breakout +
TCXO), written as 2 SEPARATE, independently-fabricable files --
arm_board.kicad_pcb + hub.kicad_pcb.

This used to be 4 separate cluster_00..03.kicad_pcb files (one per
quadrant, each built at its own rotated angle) plus the hub. The user then
laid the arm board out by hand in KiCad and asked for that ONE design to be
reused for all 4 quadrants: fabricate arm_board.kicad_pcb 4x and physically
mount those 4 identical boards rotated 0/90/180/270deg around the hub,
rather than designing (and fabricating) 4 distinct boards. This works
because the whole mic array is exactly 4-fold rotationally symmetric by
construction (arm_board is generated at c=0; cluster_outline_points(c) /
find_module_placement(c) / etc. for c=1..3 are the *same* geometry rotated
90c degrees around the array centre, not an independent layout) -- so a
physical copy of the c=0 board, rotated into the c=1 slot, lands exactly on
the c=1 mic positions. The schematic side is unaffected (still models 4
electrically distinct clusters -- cluster_00..03.kicad_sch, different net
names per cluster); only the PCB happens to reuse one physical design 4x.
All 4 physical copies will carry the same silkscreen reference designators
(U1-U24, A1, J1, etc.) -- normal for a repeated identical module, not a
bug, since each board is a standalone electrical + mechanical unit
disambiguated by which quadrant it's mounted in, not by a global unique ref.

The hub is still a genuinely single, non-repeated board, and still needs
all 4 conceptual (rotated) positions internally -- one real physical
connector/standoff per quadrant, at 4 different angles -- even though only
one of those 4 angles (c=0) gets built out into the arm board file itself.

Both files share the same (array-centre-origin) coordinate system before
each one's own cosmetic page-centring shift (center_board_on_page()) is
applied -- this is what lets arm_board's connector/standoff positions be
computed with the exact same formula the hub uses for its own matching
socket/standoff at each of the 4 angles, guaranteeing they align physically
even though (post page-centring) their saved coordinates no longer match
numerically file-to-file.

Scope: board outlines + footprint placement only, no routing (mirrors
pcb/mic_array/tools/place_mics.py's placement-only precedent for the single-FPGA board).
Unlike place_mics.py, this does not require "Update PCB from Schematic" or
KiCad's in-app Scripting Console first -- it builds each board from scratch,
loading footprints directly by library path via pcbnew (confirmed importable
from plain python3 in this environment). Pads are left netless (no netlist
import); wiring/routing is a separate follow-up pass.

Each cluster's board outline is bounded by two Underbrink log-spiral curves
(the same shape used to generate the mic positions themselves, see
notebooks/make_nb18.py's underbrink_array()), offset by a constant 90°
rotation from each other and by 15° from that cluster's own 3 arms. Because
all 12 arms are the same spiral curve rotated by multiples of 30°, a cut
curve offset by +-15° from the outermost/innermost arm of a cluster stays
exactly 90° of arc from its mirror image at every radius -- so the 4
cluster outlines tile the full circle with no gaps or overlaps, even though
each individual arm curls well past its own 30° nominal spacing by the time
it reaches its outermost mic (up to ~41° of spiral sweep at these
R_MIN/R_MAX/SPIRAL_DEG values) -- a straight radial cut would clip mics.

Usage (from project root):
  python3 pcb/multi_fpga/tools/layout_multi_fpga.py
"""

import csv
import math
import os

import pcbnew

# ── array geometry constants -- MUST match notebooks/make_nb18.py's
# underbrink_array(12, 8) call exactly, since these boards are built around
# the same mic positions that notebook derives (test/phase4/array_xy.csv is
# that notebook's own output). ─────────────────────────────────────────────
R_MIN_MM     = 25.0
R_MAX_MM     = 150.0
SPIRAL_DEG   = 22.0
N_ARMS_TOTAL = 12
ARMS_PER_CLUSTER = 3
N_CLUSTERS   = 4

# The board's own inner edge has to sit CLOSER to centre than R_MIN_MM, not
# AT it: mics are placed unrotated (fixed orientation regardless of their
# angular position, matching pcb/mic_array/tools/place_mics.py's precedent for the
# single-FPGA board), so an innermost mic's asymmetric courtyard
# (IM72D128, -2.7..3.15mm x -2.25..2.25mm around its centre) doesn't sit
# symmetrically about its own radial direction -- at some of the 12 arms'
# angles, a footprint corner reaches as close as r=21.15mm to the array
# centre even though the mic's own centre is at r=R_MIN_MM=25mm. Checked
# across all 12 arms' innermost mics, not just arm 0. 20.0mm leaves ~1.1mm
# margin past the worst case.
BOARD_INNER_RADIUS_MM = 20.0

TOOLS_DIR  = os.path.dirname(os.path.abspath(__file__))  # pcb/multi_fpga/tools
OUTDIR     = os.path.dirname(TOOLS_DIR)                   # pcb/multi_fpga
ROOT       = os.path.dirname(OUTDIR)                      # pcb
CSV_PATH   = os.path.join(ROOT, "..", "test", "phase4", "array_xy.csv")


def board_pcb_path(name):
    return os.path.join(OUTDIR, f"{name}.kicad_pcb")

MIC_FP_LIB  = os.path.join(ROOT, "IM72D128", "KiCad")
MIC_FP_NAME = "IFX-PG-LLGA-5-4"
DIP48_LIB   = "/usr/share/kicad/footprints/Package_DIP.pretty"
DIP48_NAME  = "DIP-48_W15.24mm_Socket"
LOCAL_LIB   = os.path.join(ROOT, "libraries", "multi_fpga", "footprints.pretty")
CAP_FP_LIB  = "/usr/share/kicad/footprints/Capacitor_SMD.pretty"
CAP_FP_NAME = "C_0603_1608Metric"
MOUNTHOLE_LIB       = "/usr/share/kicad/footprints/MountingHole.pretty"
STANDOFF_HOLE_NAME  = "MountingHole_2.7mm_M2.5"  # cluster<->hub standoffs + Pi 5's own holes (both M2.5)
ENCLOSURE_HOLE_NAME = "MountingHole_3.2mm_M3"     # cluster board -> outer enclosure
SPOKE_SOCKET_LIB    = "/usr/share/kicad/footprints/Connector_PinSocket_2.54mm.pretty"
SPOKE_SOCKET_NAME   = "PinSocket_2x06_P2.54mm_Vertical"
SPOKE_HEADER_LIB    = "/usr/share/kicad/footprints/Connector_PinHeader_2.54mm.pretty"
SPOKE_HEADER_NAME   = "PinHeader_2x06_P2.54mm_Vertical"

# Power connector (+5V/GND from hub to each arm board) -- separate from the
# spoke connector above: that one mates directly into the cluster's own Cmod
# A7-35T's Pmod JA, whose power-position pins turn out to be that module's OWN
# onboard regulator output (see SCHEMATIC_NOTES.md's power section), not a
# usable 5V input. So +5V has to reach the arm board some other way -- a
# small dedicated 2-pin header/socket, same connector family/pitch as the
# spoke connector for consistency.
PWR_HEADER_LIB  = SPOKE_HEADER_LIB
PWR_HEADER_NAME = "PinHeader_1x02_P2.54mm_Vertical"
PWR_SOCKET_LIB  = SPOKE_SOCKET_LIB
PWR_SOCKET_NAME = "PinSocket_1x02_P2.54mm_Vertical"

# LDO regulators (MCP1700 family, SOT-23-3 -- see SCHEMATIC_NOTES.md for the
# pin-to-function mapping, flagged to confirm against the datasheet).
LDO_FP_LIB  = "/usr/share/kicad/footprints/Package_TO_SOT_SMD.pretty"
LDO_FP_NAME = "SOT-23"

# Cluster's own Cmod A7-35T module: mounted RADIALLY (long axis running outward along the
# gap between two arms, not across it -- see find_module_placement() for
# why), tucked into the natural gap between this cluster's 2nd and 3rd
# arms, as far in towards the array centre as it can go without colliding
# with a mic or its decoupling cap (found by search in
# find_module_placement(), not a fixed margin). R_BOARD_MAX_MM is
# therefore no longer a fixed constant -- it's derived in main() from
# where that search actually lands the 4 (identical, just rotated)
# cluster boards, then applied uniformly to all 4 so they stay identical
# boards. This module-level value is a placeholder overwritten by main()
# before anything reads it; cluster_outline_points()/_cut_curve_points()
# depend on it via the globals below.
R_BOARD_MAX_MM = R_MAX_MM + 40.0

# ── Underbrink log-spiral helpers (mirrors notebooks/make_nb18.py exactly) ──

_B = 1.0 / math.tan(math.radians(SPIRAL_DEG))


def _t_at_r(r_mm):
    """Spiral parameter t (radians of sweep from r_min) at radius r_mm."""
    return math.log(r_mm / R_MIN_MM) / _B


def _r_at_t(t):
    return R_MIN_MM * math.exp(_B * t)


def _cut_curve_points(offset_deg, n=24, t_min=None, t_max=None):
    """Sample points (mm) along the boundary spiral rotated by offset_deg,
    from r=BOARD_INNER_RADIUS_MM (t=t_min) out to r=R_BOARD_MAX_MM
    (t=t_max). t_min is negative (BOARD_INNER_RADIUS_MM < R_MIN_MM, i.e.
    before the spiral's own t=0 point) -- the log-spiral formula is smooth
    and well-defined there too, so this just continues the same curve
    shape a little further inward; the "same shape rotated by a constant
    offset" tiling argument doesn't care what t range is used, only that
    both boundary curves use the same one. Looks up the current
    R_BOARD_MAX_MM fresh each call (rather than a bound default argument)
    since main() finalises that value only after searching for where the
    Cmod A7-35T modules actually land -- see R_BOARD_MAX_MM comment."""
    if t_min is None:
        t_min = _t_at_r(BOARD_INNER_RADIUS_MM)
    if t_max is None:
        t_max = _t_at_r(R_BOARD_MAX_MM)
    pts = []
    for i in range(n):
        t = t_min + (t_max - t_min) * i / (n - 1)
        r = _r_at_t(t)
        theta = t + math.radians(offset_deg)
        pts.append((r * math.cos(theta), r * math.sin(theta)))
    return pts


def _arc_points(r_mm, deg_from, deg_to, n=16):
    pts = []
    for i in range(n):
        deg = deg_from + (deg_to - deg_from) * i / (n - 1)
        theta = math.radians(deg)
        pts.append((r_mm * math.cos(theta), r_mm * math.sin(theta)))
    return pts


def cluster_bounds_deg(c):
    """(before, after) rotation offsets in degrees for cluster c's two
    boundary cut curves -- see module docstring for why +-15deg."""
    before = 90.0 * c - 15.0
    after = 90.0 * c + 75.0
    return before, after


def cluster_outline_points(c):
    before, after = cluster_bounds_deg(c)
    cut_before = _cut_curve_points(before)
    cut_after = _cut_curve_points(after)
    # Inner arc/cut curves now start at BOARD_INNER_RADIUS_MM (< R_MIN_MM),
    # not R_MIN_MM itself -- see that constant's comment for why (innermost
    # mics' unrotated, asymmetric courtyards otherwise poke past the inner
    # edge). Same "actual endpoint, not the un-swept angle" fix as the outer
    # arc below: at t=t_min (now negative), each cut curve's angle is
    # offset_deg + degrees(t_min), not just offset_deg.
    t_min_deg = math.degrees(_t_at_r(BOARD_INNER_RADIUS_MM))
    inner_arc = _arc_points(BOARD_INNER_RADIUS_MM, before + t_min_deg, after + t_min_deg)
    # The outer arc must connect the two cut curves' actual endpoints at
    # r=R_BOARD_MAX_MM, not the "before"/"after" angles -- those only apply
    # at r=R_MIN_MM (t=0). Both curves sweep an extra degrees(t_max) of
    # angle by the outer radius (the same spiral-drift mechanism this file
    # relies on elsewhere), so using the un-swept angles here left a
    # degrees(t_max)-wide gap at each shoulder that add_outline() drew as a
    # straight chord cutting across the board near its outer edge.
    t_max_deg = math.degrees(_t_at_r(R_BOARD_MAX_MM))
    outer_arc = _arc_points(R_BOARD_MAX_MM, after + t_max_deg, before + t_max_deg)
    return inner_arc + cut_after + outer_arc + list(reversed(cut_before))


# ── footprint loading ────────────────────────────────────────────────────

def load_fp(lib_path, name, ref, x_mm, y_mm, rot_deg=0.0):
    fp = pcbnew.FootprintLoad(lib_path, name)
    if fp is None:
        raise RuntimeError(f"footprint not found: {lib_path} / {name}")
    fp.SetReference(ref)
    fp.SetPosition(pcbnew.VECTOR2I_MM(x_mm, y_mm))
    fp.SetOrientationDegrees(rot_deg)
    return fp


def _local_courtyard_corners(lib_path, name):
    """The 4 corners (mm, footprint-local coords) of a freshly-loaded
    footprint's bounding box at 0 rotation/position -- used to test where
    its TRUE corners land once placed+rotated (see _true_corners() below).
    Loaded fresh rather than hardcoded so this stays correct if the
    footprint file changes."""
    fp = pcbnew.FootprintLoad(lib_path, name)
    fp.SetPosition(pcbnew.VECTOR2I_MM(0, 0))
    fp.SetOrientationDegrees(0)
    bb = fp.GetBoundingBox(False)
    x0, x1 = bb.GetLeft() / 1e6, bb.GetRight() / 1e6
    y0, y1 = bb.GetTop() / 1e6, bb.GetBottom() / 1e6
    return [(x0, y0), (x1, y0), (x1, y1), (x0, y1)]


def _true_corners(px_mm, py_mm, rot_deg, local_corners):
    """World-space (mm) positions of a footprint's true corners, given its
    placement and rotation. NB: FOOTPRINT.GetBoundingBox() on an already-
    rotated instance returns an axis-aligned box that circumscribes the
    rotated shape -- combining its Left/Right/Top/Bottom independently
    produces phantom points further out than any real corner. This instead
    transforms the known local corners directly, using the empirically
    confirmed mapping local+X -> world (cos t, -sin t), local+Y -> world
    (sin t, cos t) (see find_module_placement()'s docstring)."""
    t = math.radians(rot_deg)
    xdir = (math.cos(t), -math.sin(t))
    ydir = (math.sin(t), math.cos(t))
    return [(px_mm + lx * xdir[0] + ly * ydir[0],
             py_mm + lx * xdir[1] + ly * ydir[1])
            for lx, ly in local_corners]


def add_outline(board, points_mm, width_mm=0.15, layer=pcbnew.Edge_Cuts):
    shape = pcbnew.PCB_SHAPE(board)
    shape.SetShape(pcbnew.SHAPE_T_POLY)
    poly = pcbnew.SHAPE_POLY_SET()
    poly.NewOutline()
    for x, y in points_mm:
        poly.Append(pcbnew.VECTOR2I_MM(x, y))
    shape.SetPolyShape(poly)
    shape.SetLayer(layer)
    shape.SetWidth(pcbnew.FromMM(width_mm))
    board.Add(shape)


def add_keepout_square(board, half_side_mm, cx_mm=0.0, cy_mm=0.0):
    """A square reference outline on the User.Comments layer (not
    Edge.Cuts) marking a placement-exclusion zone -- documentation only,
    not a physical cutout. Used for the hub's centre camera keepout."""
    pts = [
        (cx_mm - half_side_mm, cy_mm - half_side_mm),
        (cx_mm + half_side_mm, cy_mm - half_side_mm),
        (cx_mm + half_side_mm, cy_mm + half_side_mm),
        (cx_mm - half_side_mm, cy_mm + half_side_mm),
    ]
    add_outline(board, pts, width_mm=0.1, layer=pcbnew.Cmts_User)


def add_circle_cutout(board, cx_mm, cy_mm, radius_mm, n=32, width_mm=0.15):
    """A closed circular Edge.Cuts loop fully inside the board's own outline
    reads as a cutout/hole in KiCad, not a second board -- used for the
    hub's camera lens opening."""
    pts = []
    for i in range(n):
        ang = 2 * math.pi * i / n
        pts.append((cx_mm + radius_mm * math.cos(ang), cy_mm + radius_mm * math.sin(ang)))
    add_outline(board, pts, width_mm=width_mm)


def add_mounting_hole(board, lib_name, x_mm, y_mm, ref):
    board.Add(load_fp(MOUNTHOLE_LIB, lib_name, ref, x_mm, y_mm))


PAGE_W_MM, PAGE_H_MM = 297.0, 210.0  # KiCad's default A4 landscape, matches cluster_00's own page setting


def center_board_on_page(board, x_offset_mm=0.0):
    """Translate every footprint/drawing on board by a single offset so its
    Edge.Cuts content is centred within the default A4 page -- purely
    cosmetic (matches a manual edit the user made on cluster_00: page
    position doesn't affect fabrication, just how the board looks when
    opened in KiCad). Applied last, after all the "logical" array-centred
    placement math above, so that math (and this file's own
    cross-board-alignment verification) stays in the simpler, un-shifted
    coordinate frame -- only the saved file's raw coordinates carry the
    shift.

    x_offset_mm: additional horizontal nudge from true page-centre (e.g.
    negative to shift left) -- added for arm_board, whose true-centred
    position overlapped the drawing frame's title block at the page's
    bottom right corner."""
    bbox = None
    for s in board.GetDrawings():
        if s.GetLayerName() != "Edge.Cuts":
            continue
        bbox = s.GetBoundingBox() if bbox is None else bbox
        bbox.Merge(s.GetBoundingBox())
    if bbox is None:
        return
    cx = (bbox.GetLeft() + bbox.GetRight()) / 2.0
    cy = (bbox.GetTop() + bbox.GetBottom()) / 2.0
    delta = pcbnew.VECTOR2I(int(pcbnew.FromMM(PAGE_W_MM / 2.0 + x_offset_mm) - cx),
                             int(pcbnew.FromMM(PAGE_H_MM / 2.0) - cy))
    for fp in board.GetFootprints():
        fp.Move(delta)
    for s in board.GetDrawings():
        s.Move(delta)


# ── cluster board ────────────────────────────────────────────────────────

# Mic-local offset/rotation for its own decoupling cap, chosen so the cap's
# 2 pads land as close as possible to the mic's real VDD (pin 2) and GND
# (pin 5) pads specifically -- not just "somewhere near the mic" (the old
# radial-3mm-offset scheme, which didn't target any particular pin and
# could leave VDD/GND on the far side from the cap). See the real
# IM72D128V01 pin positions this is based on (pin 2/VDD at (-0.39,-0.85),
# pin 5/GND at (0.285,0), mic-local, unrotated, per the corrected pinout --
# see route_arm_board.py's module docstring for the pin-numbering fix this
# depends on).
#
# Two earlier attempts at this offset were both wrong:
# 1. A tight-fit search (~0.28-0.49mm stubs) only checked clearance against
#    the mic's *other pads* and NPTH hole -- not its real physical body.
#    The mic's actual silkscreen/F.Fab outline (its real ~4.4x3.4mm
#    package, not just the courtyard keepout) turned out to extend well
#    past the pads themselves (x: -1.8 to 2.6, y: -1.7 to 1.7, mic-local),
#    so that "tight" placement had the cap's own body sitting *inside*
#    where the mic package physically is -- not buildable, two solid parts
#    can't occupy the same space (found by the user visually spotting the
#    overlap, not by this project's own courtyard-based collision checks,
#    which treat mic+own-cap courtyard overlap as expected/skipped and so
#    never flagged this).
# 2. The first fix used a precise 290deg rotation to claw back some of
#    that closeness once real-body clearance was enforced -- but
#    Freerouting choked on it badly (15+ min, 142/176 still unrouted, vs
#    ~3 min/~28 unrouted for every axis-aligned board this session).
#
# This offset clears the mic's real body (F.Silkscreen outline, +0.5mm
# margin) at rot=0 (no rotation at all -- simplest possible, and pad "1"
# still lands nearer VDD, pad "2" nearer GND, matching the existing
# pad-to-net convention below) -- found by a directed search minimising
# the worse of the 2 resulting stub lengths subject to that real-body
# clearance. ~1.7mm from VDD, ~2.6mm from GND: not as tight as either
# earlier (invalid) attempt, but a real, buildable placement that's still
# smaller than and consistently on the correct side of the mic, unlike the
# old radial scheme (whose distance to VDD/GND varied arbitrarily per mic
# depending on that mic's angular position in the array). The margin was
# widened from 0.2mm to 0.5mm on request for more breathing room between
# cap and mic bodies -- verified via direct body-to-body AABB check (0
# collisions against own mic, all neighboring mics, and all other caps).
#
# A second request asked for the mic/cap *courtyards* (not just real
# bodies) to stop overlapping too -- that needs -2.95 (0.35mm past the
# 0.33mm of courtyard overlap the -2.6 offset above has). Pushing every
# mic that far is fine almost everywhere, but 4 mics on the arm board
# (U4, U9, U16, U21) sit close enough to *other nets'* pre-existing
# routing that the extra 0.35mm push creates real shorts there (found by
# DRC diff before/after, not by the courtyard check itself, which is
# blind to routing). Those 4 keep the old -2.6 offset and its
# already-accepted 0.33mm courtyard overlap rather than introduce a new
# short -- a per-board tightness, not something a different offset fixes.
CAP_TO_MIC_DX_MM = -0.49
CAP_TO_MIC_DY_MM = -2.95
CAP_TO_MIC_DY_MM_EXCEPTIONS = {4: -2.6, 9: -2.6, 16: -2.6, 21: -2.6}  # mic number (Un), not index
CAP_ROT_DEG = 0.0


def _mic_and_cap_xy(x, y, mic_num=None):
    """Cap position (and rotation) for a mic at (x,y) -- mics are placed
    unrotated regardless of array position, so this fixed mic-local offset
    applies directly in world coordinates too. Shared by the obstacle check
    (find_module_placement()) and the actual placement (build_cluster())
    so the check sees exactly what gets placed. mic_num (Un's number, 1-based)
    selects the courtyard-overlap-tolerant exception offset for a few mics
    too close to other routing -- see CAP_TO_MIC_DY_MM_EXCEPTIONS above."""
    dy = CAP_TO_MIC_DY_MM_EXCEPTIONS.get(mic_num, CAP_TO_MIC_DY_MM)
    return x + CAP_TO_MIC_DX_MM, y + dy, CAP_ROT_DEG


# Cluster's own Cmod A7-35T placement: fixed constants approximating the
# user's latest manual edit on cluster_00 (moved A1, alongside J1 -- see
# CLUSTER_HUB_CONNECTOR_* below) -- recovered the same way as always: find
# the file's manual page-centring translation from a mic's actual position
# vs. its known array_xy.csv position (confirmed a pure translation -- U1
# and U2 agreed exactly), subtract it back out to recover A1's true
# array-centred (r, angle, rotation). Rotation is now 0deg (was 30-90c) --
# reset to the footprint's default orientation, not derived from the
# position angle. Chip-agnostic: this places the generic DIP48_LIB/
# DIP48_NAME footprint (see find_module_placement() below), so the Cmod S7
# -> Cmod A7-35T FPGA swap didn't change these numbers, only which part is
# silkscreened there.
CLUSTER_CMOD_PLACEMENT_R_MM     = 91.47
CLUSTER_CMOD_PLACEMENT_ANGLE_DEG = 43.75  # offset from each cluster's own 90*c base
CLUSTER_CMOD_PLACEMENT_ROT_DEG   = 0.0    # rot_deg = CLUSTER_CMOD_PLACEMENT_ROT_DEG - 90*c


def find_module_placement(c, mic_rows):
    """Cluster c's own Cmod A7-35T placement -- see
    CLUSTER_CMOD_PLACEMENT_* comment above. mic_rows is unused (kept in the
    signature since build_cluster() and main() already pass it, and a
    future revision may want it again for a collision check) but the
    placement itself is now a fixed formula, not searched. Returns (mx, my,
    rot_deg, max_corner_radius_mm)."""
    angle_deg = 90.0 * c + CLUSTER_CMOD_PLACEMENT_ANGLE_DEG
    rot_deg = CLUSTER_CMOD_PLACEMENT_ROT_DEG - 90.0 * c
    theta = math.radians(angle_deg)
    mx, my = CLUSTER_CMOD_PLACEMENT_R_MM * math.cos(theta), CLUSTER_CMOD_PLACEMENT_R_MM * math.sin(theta)

    local_corners = _local_courtyard_corners(DIP48_LIB, DIP48_NAME)
    corners = _true_corners(mx, my, rot_deg, local_corners)
    max_r = max(math.hypot(x, y) for x, y in corners)
    return mx, my, rot_deg, max_r


# Board-to-board spoke connector: fixed constants approximating the user's
# latest manual edit on cluster_00 (moved J1, alongside A1 above) --
# recovered the same way as always (see CLUSTER_CMOD_PLACEMENT_* comment).
# Rotation is also now 0deg (was 45deg).
CLUSTER_HUB_CONNECTOR_R_MM = 48.30
CLUSTER_HUB_CONNECTOR_ANGLE_DEG = 25.55  # offset from each cluster's own 90*c base
CLUSTER_HUB_CONNECTOR_ROT_DEG = 0.0      # rot_deg = CLUSTER_HUB_CONNECTOR_ROT_DEG - 90*c

CLUSTER_STANDOFF_R_MM = 69.64
CLUSTER_STANDOFF_ANGLE_DEG = 37.43  # offset from each cluster's own 90*c base


def cluster_hub_connector_xy(c):
    """(mx, my, rot_deg) for cluster c's spoke connector -- see
    CLUSTER_HUB_CONNECTOR_* comment above."""
    angle_deg = 90.0 * c + CLUSTER_HUB_CONNECTOR_ANGLE_DEG
    rot_deg = CLUSTER_HUB_CONNECTOR_ROT_DEG - 90.0 * c
    theta = math.radians(angle_deg)
    return (CLUSTER_HUB_CONNECTOR_R_MM * math.cos(theta),
            CLUSTER_HUB_CONNECTOR_R_MM * math.sin(theta),
            rot_deg)


def cluster_standoff_xy(c):
    """Mechanical standoff position for cluster c's hub connection -- see
    CLUSTER_STANDOFF_* comment above. Same (x,y) is used on both the
    cluster board (build_cluster()) and the hub board (place_hub())."""
    angle_deg = 90.0 * c + CLUSTER_STANDOFF_ANGLE_DEG
    theta = math.radians(angle_deg)
    return (CLUSTER_STANDOFF_R_MM * math.cos(theta),
            CLUSTER_STANDOFF_R_MM * math.sin(theta))


# Enclosure-mounting holes: 2 per cluster board, near the outer rim, at
# +-40deg from that cluster's wedge bisector (90c+30) -- clear of both the
# cluster's own Cmod A7-35T (which sits at +20.2deg from the bisector, see
# CLUSTER_CMOD_PLACEMENT_ANGLE_DEG=50.2 vs the 30deg bisector) and the
# wedge's own +-45deg boundary (5deg margin so a hole doesn't land right at
# the board edge).
ENCLOSURE_HOLE_OFFSET_DEG = 40.0


def build_cluster(board, c, mic_rows, module_placement):
    add_outline(board, cluster_outline_points(c))

    for row in mic_rows:
        mic_idx = int(row["mic_idx"])
        x, y = float(row["x_mm"]), float(row["y_mm"])
        mic_fp = load_fp(MIC_FP_LIB, MIC_FP_NAME, f"U{mic_idx + 1}", x, y)
        # IFX-PG-LLGA-5-4's Value field is a vendor placeholder literally
        # reading "Comment" (not a real part value) -- hide it rather than
        # clear it, so the underlying footprint data isn't touched, only
        # this board's rendering of it.
        mic_fp.Value().SetVisible(False)
        board.Add(mic_fp)
        cx, cy, crot = _mic_and_cap_xy(x, y, mic_num=mic_idx + 1)
        board.Add(load_fp(CAP_FP_LIB, CAP_FP_NAME, f"C{mic_idx + 1}", cx, cy, rot_deg=crot))

    mx, my, rot_deg = module_placement
    board.Add(load_fp(DIP48_LIB, DIP48_NAME, f"A{c + 1}", mx, my, rot_deg=rot_deg))

    # Board-to-board spoke connector (header; mates with a socket at the
    # identical (x,y) on the hub board -- see place_hub()). Connects to
    # this cluster's own Cmod A7-35T Pmod JA pins via traces, not yet routed.
    jx, jy, jrot = cluster_hub_connector_xy(c)
    board.Add(load_fp(SPOKE_HEADER_LIB, SPOKE_HEADER_NAME, f"J{c + 1}", jx, jy, rot_deg=jrot))

    # Cluster<->hub mechanical standoff.
    sx, sy = cluster_standoff_xy(c)
    add_mounting_hole(board, STANDOFF_HOLE_NAME, sx, sy, f"H{c + 1}A")

    # Power connector (+5V/GND from hub, see PWR_HEADER_* above) + this
    # cluster's own +1.8V LDO (VR1) + bypass caps -- placed in the open area
    # near the spoke connector/standoff (only built once, at c=0, same as
    # everything else on this board). Only c=0's build call matters (only
    # arm_board.kicad_pcb is actually saved), but the formula stays
    # rotation-general the same way cluster_hub_connector_xy() does.
    if c == 0:
        px, py = jx + 14.1, jy + 5.13
        board.Add(load_fp(PWR_HEADER_LIB, PWR_HEADER_NAME, "J2", px, py))
        vx, vy = px + 14.0, py
        board.Add(load_fp(LDO_FP_LIB, LDO_FP_NAME, "VR1", vx, vy))
        board.Add(load_fp(CAP_FP_LIB, CAP_FP_NAME, "C25", vx - 6.0, vy + 6.0))
        board.Add(load_fp(CAP_FP_LIB, CAP_FP_NAME, "C26", vx + 6.0, vy + 6.0))

    # Enclosure mounting, 2 per board, near the outer rim. The wedge centre
    # drifts with radius (same spiral-drift reasoning as cluster_outline_
    # points()/find_module_placement()), so it's evaluated at r_enc, not
    # taken as the fixed 90c+30 that only holds at r=R_MIN.
    r_enc = R_BOARD_MAX_MM - 15.0
    bisector_deg_at_r = 90.0 * c + 30.0 + math.degrees(_t_at_r(r_enc))
    for i, sign in enumerate((-1.0, 1.0)):
        deg = bisector_deg_at_r + sign * ENCLOSURE_HOLE_OFFSET_DEG
        ex = r_enc * math.cos(math.radians(deg))
        ey = r_enc * math.sin(math.radians(deg))
        add_mounting_hole(board, ENCLOSURE_HOLE_NAME, ex, ey, f"H{c + 1}E{i + 1}")


# ── hub board ────────────────────────────────────────────────────────────
# The hub now mounts at the physical centre of the array (not a
# disconnected board off to one side): a circular board, standoff- and
# connector-mated to all 4 cluster boards, with the camera looking forward
# through a centre cutout and the Pi 5 stacked on the same standoffs
# behind it. See PHASE4.md / SCHEMATIC_NOTES.md "Spoke connector" for the
# board-to-board connector choice (plain 2x6 2.54mm header/socket -- now a
# standalone connector reached by a PCB trace from each cluster's Cmod A7-35T's Pmod JA,
# not plugged directly into it, see cluster_hub_connector_xy()) and its
# flagged signal-integrity caveat (shared Pmod ground / spoke CLK jitter
# risk, not solved in this pass).

HUB_HALF_SIDE_MM = R_MAX_MM  # placeholder, overwritten in main() once the hub's
                          # own component placements (below) are known -- see
                          # that override for why this can no longer be a
                          # fixed guess now that the spoke connectors moved
                          # close to centre (they used to be the limiting
                          # factor; the hub's own CMOD_A7_35T etc. are now)

# Camera (Pi Camera Module 3 Wide): PCB 25x24mm, lens module ~12.4mm tall
# (Raspberry Pi's spec sheet). Lens-barrel diameter wasn't found this
# session -- cutout sized generously and flagged to confirm against
# Raspberry Pi's mechanical drawing before fab, same for the mounting-hole
# spacing (placeholder, camera modules typically use 2 small holes).
# Shrunk from 20mm so there's real annular clearance to HCAM1/HCAM2 (at
# +-CAMERA_MOUNT_HOLE_SPACING_MM/2 = +-10.5mm, courtyard half-extent
# ~2.975mm) -- 20mm dia (10mm radius) left the mount holes' courtyards
# overlapping the cutout edge.
CAMERA_CUTOUT_DIA_MM = 12.0
CAMERA_MOUNT_HOLE_SPACING_MM = 21.0

# Placement-exclusion zone reserved for the camera module, centred on the
# hub -- drawn as a User.Comments reference square (add_keepout_square()),
# not a physical Edge.Cuts cutout. All 3 hub modules below are placed
# clear of this.
KEEPOUT_SIZE_MM = 35.0

# Raspberry Pi 5: 85x56mm board, M2.5 mounting holes on the same pattern as
# Pi 4 (official mechanical drawing referenced but exact offsets not
# pulled this session -- placeholder centred rectangle, confirm before
# fab). Stacks behind the hub on its own standoffs (own hole pattern, not
# the 4 cluster-facing ones), connected by a short USB cable (Pi 5's USB
# port is fixed hardware, not a rigid board-to-board link) -- so only its
# mounting holes are modelled here, not a fabricated outline (it's a
# purchased board, not one this project cuts).
RPI5_HOLE_HALF_SPACING_MM = (29.0, 24.5)  # placeholder half-spacing (58x49mm pattern)
RPI5_CENTRE_XY_MM = (0.0, -160.0)  # clear of the hub's own footprint entirely -- Pi 5 is a
                                    # purchased board on its own standoffs, doesn't need to
                                    # share the hub board's own footprint at all


# Hub's own CMOD_A7_35T + FT232H + TCXO placements -- module-level so both
# place_hub() and main()'s HUB_HALF_SIDE_MM computation use the exact same
# numbers (previously duplicated by hand in both places, which is exactly
# how a mismatch slipped in once already).
#
# Axis-aligned ("horizontal and vertical", 0/90/180/270deg only, no
# tangential/angled mounting) per the user's request, placed clear of the
# KEEPOUT_SIZE_MM centre keepout and the 4 spoke sockets/standoffs
# (obstacle field computed from cluster_hub_connector_xy()/
# cluster_standoff_xy() for all 4 quadrants -- those sockets/standoffs
# happen to already be axis-aligned themselves since
# CLUSTER_HUB_CONNECTOR_ROT_DEG=0.0, so a plain AABB check against them is
# exact, not just a conservative approximation):
#   CMOD_A7_35T: vertical, tucked between the centre keepout and the
#   J3/J4/H3B/H4B connectors in the lower-right, clear of everything --
#   position/rotation match the user's manual edit of A5 on hub.kicad_pcb
#   (extracted the same way as CLUSTER_CMOD_PLACEMENT_*/CLUSTER_HUB_CONNECTOR_*
#   above: recovered the file's page-centring shift from A6/H*B/J*/HCAM*,
#   which all matched a single uniform translation exactly, then subtracted
#   it back out of A5's saved position).
#   FT232H: vertical, straddling the +Y axis, clear of J1/H1B and J2/H2B
#   in the quadrants either side of it.
#   TCXO (small): vertical, on the -Y axis, clear of J3/H3B/J4/H4B.
HUB_CMOD_A7_XY_MM = (41.88, -44.705)
HUB_CMOD_A7_ROT_DEG = 0.0
HUB_FT232H_XY_MM = (0.0, 48.0)
HUB_FT232H_ROT_DEG = 0.0
HUB_TCXO_XY_MM = (0.0, -30.0)
HUB_TCXO_ROT_DEG = 0.0


def place_hub(board):
    half = HUB_HALF_SIDE_MM
    add_outline(board, [(-half, -half), (half, -half), (half, half), (-half, half)])
    add_circle_cutout(board, 0.0, 0.0, CAMERA_CUTOUT_DIA_MM / 2.0)
    add_keepout_square(board, KEEPOUT_SIZE_MM / 2.0)

    # 4x spoke connector sockets -- exact same (x,y) as each cluster's own
    # connector (cluster_hub_connector_xy() reused directly), so the
    # socket lines up under that cluster's header. Rotation matched too,
    # though pin-1 alignment between the two facing connectors still needs
    # a physical check once parts are in hand (flagged, not verified here).
    for c in range(N_CLUSTERS):
        sx, sy, srot = cluster_hub_connector_xy(c)
        board.Add(load_fp(SPOKE_SOCKET_LIB, SPOKE_SOCKET_NAME, f"J{c + 1}", sx, sy, rot_deg=srot))
        hx, hy = cluster_standoff_xy(c)
        add_mounting_hole(board, STANDOFF_HOLE_NAME, hx, hy, f"H{c + 1}B")

        # Power socket (+5V/GND out to that cluster's arm board, see
        # PWR_HEADER_*/PWR_SOCKET_* above) -- same local offset from the
        # spoke socket as the arm board's own J2 (build_cluster()), rotated
        # into this cluster's own orientation the same way every other
        # per-quadrant item on this board already is.
        t = math.radians(srot)
        dx, dy = 14.1, 5.13
        wx = sx + dx * math.cos(t) + dy * math.sin(t)
        wy = sy - dx * math.sin(t) + dy * math.cos(t)
        board.Add(load_fp(PWR_SOCKET_LIB, PWR_SOCKET_NAME, f"J{N_CLUSTERS + 1 + c}", wx, wy, rot_deg=srot))

    # Hub's own CMOD_A7_35T + FT232H + TCXO -- see the HUB_CMOD_A7_*/
    # HUB_FT232H_*/HUB_TCXO_* constants above for placement reasoning.
    ax, ay = HUB_CMOD_A7_XY_MM
    board.Add(load_fp(DIP48_LIB, DIP48_NAME, f"A{N_CLUSTERS + 1}", ax, ay, rot_deg=HUB_CMOD_A7_ROT_DEG))

    fx, fy = HUB_FT232H_XY_MM
    board.Add(load_fp(LOCAL_LIB, "Adafruit_FT232H", f"A{N_CLUSTERS + 2}", fx, fy, rot_deg=HUB_FT232H_ROT_DEG))

    tx, ty = HUB_TCXO_XY_MM
    board.Add(load_fp(LOCAL_LIB, "TCXO_Can", "Y1", tx, ty, rot_deg=HUB_TCXO_ROT_DEG))

    # Hub's own +3.3V LDO (VR2, for FT232H + TCXO) + bypass caps -- placed
    # in the open lower-left quadrant, clear of A5/A6/Y1/the keepout/all 4
    # spoke sockets+standoffs+power sockets (verified, not just assumed).
    vr2x, vr2y = -55.0, -20.0
    board.Add(load_fp(LDO_FP_LIB, LDO_FP_NAME, f"VR{N_CLUSTERS + 1}", vr2x, vr2y))
    board.Add(load_fp(CAP_FP_LIB, CAP_FP_NAME, "C1", vr2x - 6.0, vr2y + 6.0))
    board.Add(load_fp(CAP_FP_LIB, CAP_FP_NAME, "C2", vr2x + 6.0, vr2y + 6.0))

    # Camera mount (placeholder mounting holes either side of the cutout).
    cx0, cy0 = CAMERA_MOUNT_HOLE_SPACING_MM / 2.0, 0.0
    add_mounting_hole(board, STANDOFF_HOLE_NAME, -cx0, cy0, "HCAM1")
    add_mounting_hole(board, STANDOFF_HOLE_NAME, cx0, cy0, "HCAM2")

    # Raspberry Pi 5 mounting holes (own standoffs, stacked behind the hub).
    prx, pry = RPI5_CENTRE_XY_MM
    hx, hy = RPI5_HOLE_HALF_SPACING_MM
    for i, (sx, sy) in enumerate([(-hx, -hy), (hx, -hy), (-hx, hy), (hx, hy)]):
        add_mounting_hole(board, STANDOFF_HOLE_NAME, prx + sx, pry + sy, f"HPI{i + 1}")


# ── main ─────────────────────────────────────────────────────────────────

def main():
    with open(CSV_PATH, newline="") as f:
        rows = list(csv.DictReader(f))

    # Plan pass: find each cluster's mic rows + its Cmod A7-35T placement
    # before drawing anything. R_BOARD_MAX_MM depends on how far out the
    # search actually needs to go, and the 4 boards must stay identical
    # (just rotated 90deg each) -- so every cluster_outline_points() call
    # has to use the SAME final R_BOARD_MAX_MM, decided only after all 4
    # searches are in.
    cluster_mic_rows = []
    placements = []
    max_reach = 0.0
    for c in range(N_CLUSTERS):
        arms = range(c * ARMS_PER_CLUSTER, (c + 1) * ARMS_PER_CLUSTER)
        mic_rows = [r for r in rows if int(r["arm_idx"]) in arms]
        cluster_mic_rows.append(mic_rows)

        mx, my, rot_deg, max_r = find_module_placement(c, mic_rows)
        placements.append((mx, my, rot_deg))
        max_reach = max(max_reach, max_r)

    global R_BOARD_MAX_MM
    R_BOARD_MAX_MM = max(R_MAX_MM + 5.0, max_reach + 3.0)  # 3mm clearance past the furthest module corner found

    # HUB_HALF_SIDE_MM likewise depends on where the hub's own content
    # actually lands -- computed the same way as R_BOARD_MAX_MM: place
    # everything (in local coordinate math only, nothing drawn yet), find
    # the furthest |x| and |y| reach (not Euclidean radius -- the hub is a
    # SQUARE now, so what matters is the largest axis-aligned extent, not
    # distance from centre), add a small margin.
    global HUB_HALF_SIDE_MM
    hub_reach = 0.0
    dip48_corners = _local_courtyard_corners(DIP48_LIB, DIP48_NAME)
    socket_corners = _local_courtyard_corners(SPOKE_SOCKET_LIB, SPOKE_SOCKET_NAME)
    ft_corners = _local_courtyard_corners(LOCAL_LIB, "Adafruit_FT232H")
    tcxo_corners = _local_courtyard_corners(LOCAL_LIB, "TCXO_Can")

    def _reach(corners):
        return max(max(abs(x), abs(y)) for x, y in corners)

    pwr_socket_corners = _local_courtyard_corners(PWR_SOCKET_LIB, PWR_SOCKET_NAME)
    ldo_corners = _local_courtyard_corners(LDO_FP_LIB, LDO_FP_NAME)
    cap_corners = _local_courtyard_corners(CAP_FP_LIB, CAP_FP_NAME)
    for c in range(N_CLUSTERS):
        sx, sy, srot = cluster_hub_connector_xy(c)
        hub_reach = max(hub_reach, _reach(_true_corners(sx, sy, srot, socket_corners)))
        hx, hy = cluster_standoff_xy(c)
        hub_reach = max(hub_reach, _reach(_true_corners(hx, hy, 0.0, _local_courtyard_corners(MOUNTHOLE_LIB, STANDOFF_HOLE_NAME))))
        t = math.radians(srot)
        wx = sx + 14.1 * math.cos(t) + 5.13 * math.sin(t)
        wy = sy - 14.1 * math.sin(t) + 5.13 * math.cos(t)
        hub_reach = max(hub_reach, _reach(_true_corners(wx, wy, srot, pwr_socket_corners)))
    ax, ay = HUB_CMOD_A7_XY_MM
    hub_reach = max(hub_reach, _reach(_true_corners(ax, ay, HUB_CMOD_A7_ROT_DEG, dip48_corners)))
    fx, fy = HUB_FT232H_XY_MM
    hub_reach = max(hub_reach, _reach(_true_corners(fx, fy, HUB_FT232H_ROT_DEG, ft_corners)))
    tx, ty = HUB_TCXO_XY_MM
    hub_reach = max(hub_reach, _reach(_true_corners(tx, ty, HUB_TCXO_ROT_DEG, tcxo_corners)))
    vr2x, vr2y = -55.0, -20.0
    hub_reach = max(hub_reach, _reach(_true_corners(vr2x, vr2y, 0.0, ldo_corners)))
    hub_reach = max(hub_reach, _reach(_true_corners(vr2x - 6.0, vr2y + 6.0, 0.0, cap_corners)))
    hub_reach = max(hub_reach, _reach(_true_corners(vr2x + 6.0, vr2y + 6.0, 0.0, cap_corners)))
    HUB_HALF_SIDE_MM = hub_reach + 10.0  # margin past the furthest corner found

    # Build pass: now that R_BOARD_MAX_MM is final, draw outlines + place
    # everything. ONE arm board design (built at c=0, the canonical/
    # reference orientation) -- not 4 separate files any more, see module
    # docstring -- plus the hub, which is still genuinely a single board
    # and still needs all 4 conceptual (rotated) positions for its own 4
    # sockets/standoffs.
    os.makedirs(OUTDIR, exist_ok=True)
    total_fp = 0
    # 24 mics + 24 caps + 1 Cmod A7-35T + 1 spoke connector header + 1 cluster<->hub
    # standoff + 2 enclosure holes + 1 power header (J2) + 1 LDO (VR1) + 2 bypass caps
    expected_per_cluster = 24 + 24 + 1 + 1 + 1 + 2 + 1 + 1 + 2
    arm_board = pcbnew.CreateEmptyBoard()
    build_cluster(arm_board, 0, cluster_mic_rows[0], placements[0])
    center_board_on_page(arm_board, x_offset_mm=-25.0)
    arm_path = board_pcb_path("arm_board")
    arm_board.Save(arm_path)
    n_fp_arm = len(arm_board.GetFootprints())
    total_fp += n_fp_arm
    print(f"Saved {arm_path} -- {n_fp_arm} footprints (expected {expected_per_cluster})")
    print(f"  (this one design gets fabricated {N_CLUSTERS}x and physically rotated")
    print(f"   0/90/180/270deg around the hub to form the full {N_CLUSTERS}-quadrant array --")
    print(f"   see module docstring)")

    hub_board = pcbnew.CreateEmptyBoard()
    place_hub(hub_board)
    center_board_on_page(hub_board)
    hub_path = board_pcb_path("hub")
    hub_board.Save(hub_path)
    n_fp_hub = len(hub_board.GetFootprints())
    total_fp += n_fp_hub
    # CMOD_A7_35T + FT232H + TCXO + 4 spoke sockets + 4 hub-side standoffs
    # + 2 camera holes + 4 Pi 5 holes + 4 power sockets (J5-J8) + VR2 + 2 bypass caps
    expected_hub = 3 + N_CLUSTERS + N_CLUSTERS + 2 + 4 + N_CLUSTERS + 1 + 2
    print(f"Saved {hub_path} -- {n_fp_hub} footprints (expected {expected_hub})")

    print(f"Total footprints across both files: {total_fp}")
    print(f"R_BOARD_MAX_MM = {R_BOARD_MAX_MM:.2f}")
    print(f"HUB_HALF_SIDE_MM = {HUB_HALF_SIDE_MM:.2f} (square hub, side = {2 * HUB_HALF_SIDE_MM:.2f}mm)")


if __name__ == "__main__":
    main()
