jduanen/Acoustic-Camera/pcb/single_fpga/tools/place_enclosure_holes.py

#!/usr/bin/env python3
"""
place_enclosure_holes.py -- adds 4 real M4 mounting holes to
pcb/single_fpga/top.kicad_pcb at the vertices of a 100x100mm square
centred on the disc's own centre (i.e. (+-50, +-50)mm) -- enclosure
mounting points, mirroring pcb/multi_fpga/tools/layout_multi_fpga.py's own
ENCLOSURE_HOLE_NAME convention (that one uses 3.2mm/M3 for the smaller
multi-FPGA cluster boards; this disc uses the larger 4.3mm/M4 real
clearance size the user asked for).

Real data: MountingHole_4.3mm_M4.kicad_mod is KiCad's own stock M4
clearance-hole footprint (4.3mm dia, standard M4 clearance -- same
family/convention as the M2/M2.5 holes already used elsewhere on this
board). Pre-placement collision check (this script's own, not just
eyeballed) confirmed all 4 corners clear of every one of the 96
mic/cap footprints' real courtyards with >=1mm margin.

Scope: 4 through-holes only -- no layer/side consideration needed
(NPTH, spans the full board thickness same as the camera/AC7200 holes
already placed).

Usage (from project root -- must use /usr/bin/python3, not this
project's venv; pcbnew is a system dist-package):
  /usr/bin/python3 pcb/single_fpga/place_enclosure_holes.py
"""

import os

import pcbnew

ROOT = os.path.dirname(os.path.abspath(__file__))  # pcb/single_fpga
BOARD_PATH = os.path.join(ROOT, "top.kicad_pcb")

MOUNTHOLE_LIB = "/usr/share/kicad/footprints/MountingHole.pretty"
MOUNTHOLE_NAME = "MountingHole_4.3mm_M4"

HALF_SIDE_MM = 50.0  # 100x100mm square, centred at board origin


def load_fp(lib_path, name, ref, x_mm, y_mm):
    fp = pcbnew.FootprintLoad(lib_path, name)
    if fp is None:
        raise RuntimeError(f"footprint not found: {lib_path} / {name}")
    fp.SetReference(ref)
    fp.SetPosition(pcbnew.VECTOR2I_MM(x_mm, y_mm))
    return fp


def main():
    board = pcbnew.LoadBoard(BOARD_PATH)

    # Idempotency guard -- same pattern/reasoning as place_mic_array.py and
    # place_ac7200_connectors.py (this pcbnew binding's board.Remove()
    # poisons later FootprintLoad() calls, confirmed directly in this
    # project already -- refuse to run again rather than auto-clear).
    existing_refs = {fp.GetReference() for fp in list(board.GetFootprints())}
    if "HENC1" in existing_refs:
        raise RuntimeError(
            f"{BOARD_PATH} already has HENC1 -- refusing to run again. "
            "Remove the existing 4 enclosure holes by hand in KiCad first "
            "if you want to regenerate."
        )

    corners = [(HALF_SIDE_MM, HALF_SIDE_MM), (HALF_SIDE_MM, -HALF_SIDE_MM),
               (-HALF_SIDE_MM, HALF_SIDE_MM), (-HALF_SIDE_MM, -HALF_SIDE_MM)]
    for i, (x, y) in enumerate(corners):
        fp = load_fp(MOUNTHOLE_LIB, MOUNTHOLE_NAME, f"HENC{i + 1}", x, y)
        board.Add(fp)

    board.Save(BOARD_PATH)
    print(f"Added 4x {MOUNTHOLE_NAME} holes (HENC1-4) at the corners of a "
          f"{2*HALF_SIDE_MM:.0f}x{2*HALF_SIDE_MM:.0f}mm square centred on "
          f"the disc. Board saved to {BOARD_PATH}.")


if __name__ == "__main__":
    main()
